Xinyuan-LilyGO/T-Deck-MAX/hardware/T-Deck Pro Max V0.1 25-09-11/T-Deck Pro Max V0.1 25-09-11.pdf

# DCDC电源

# TYPE-C

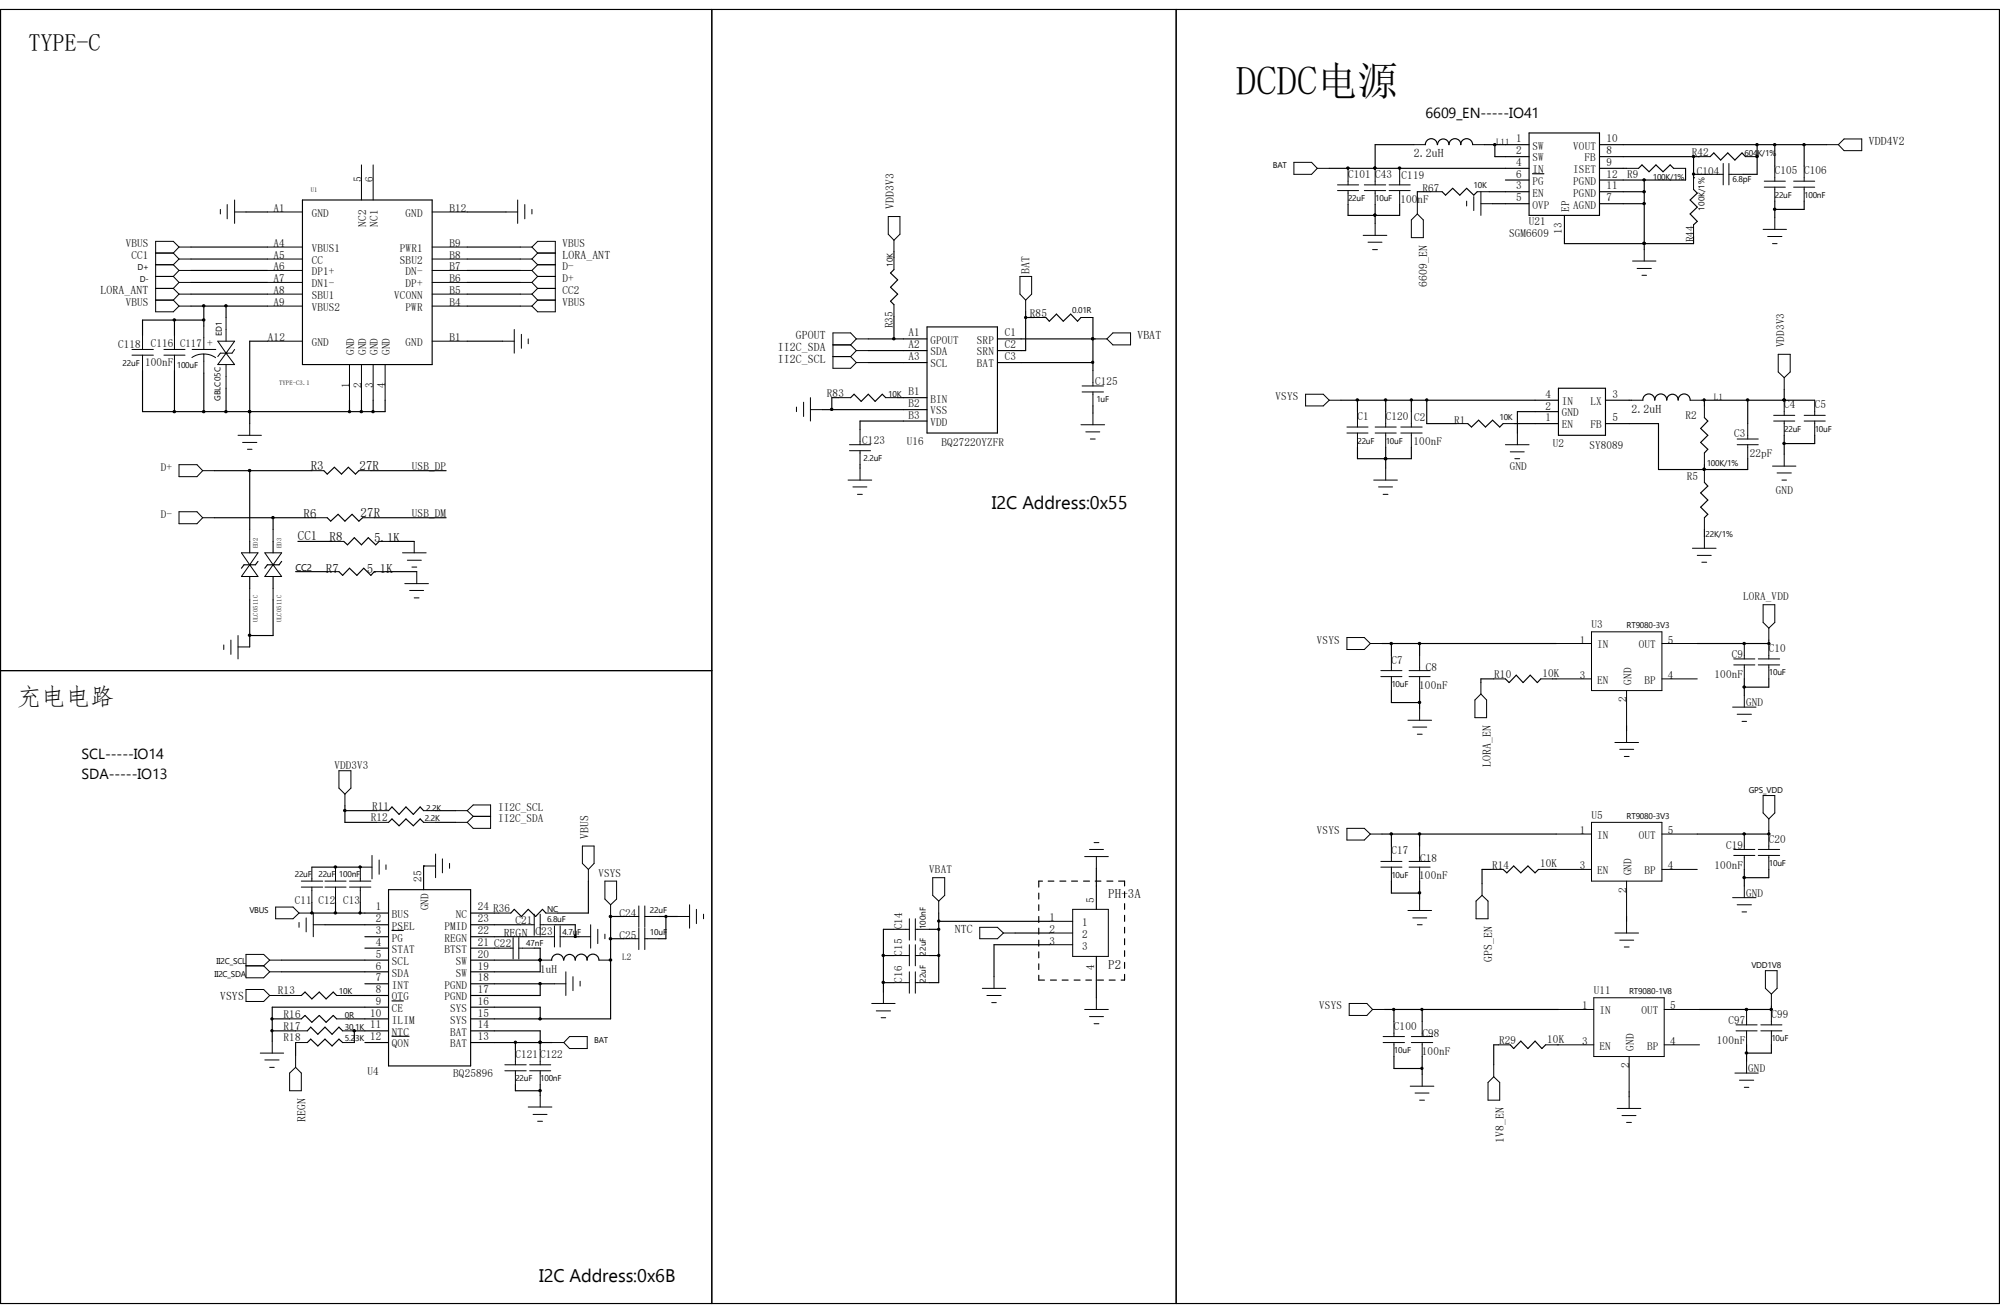
[picture p18: page 1]

STAT 5 | 20 SW
SCL 6 | 19 SW

# ESP32-S3

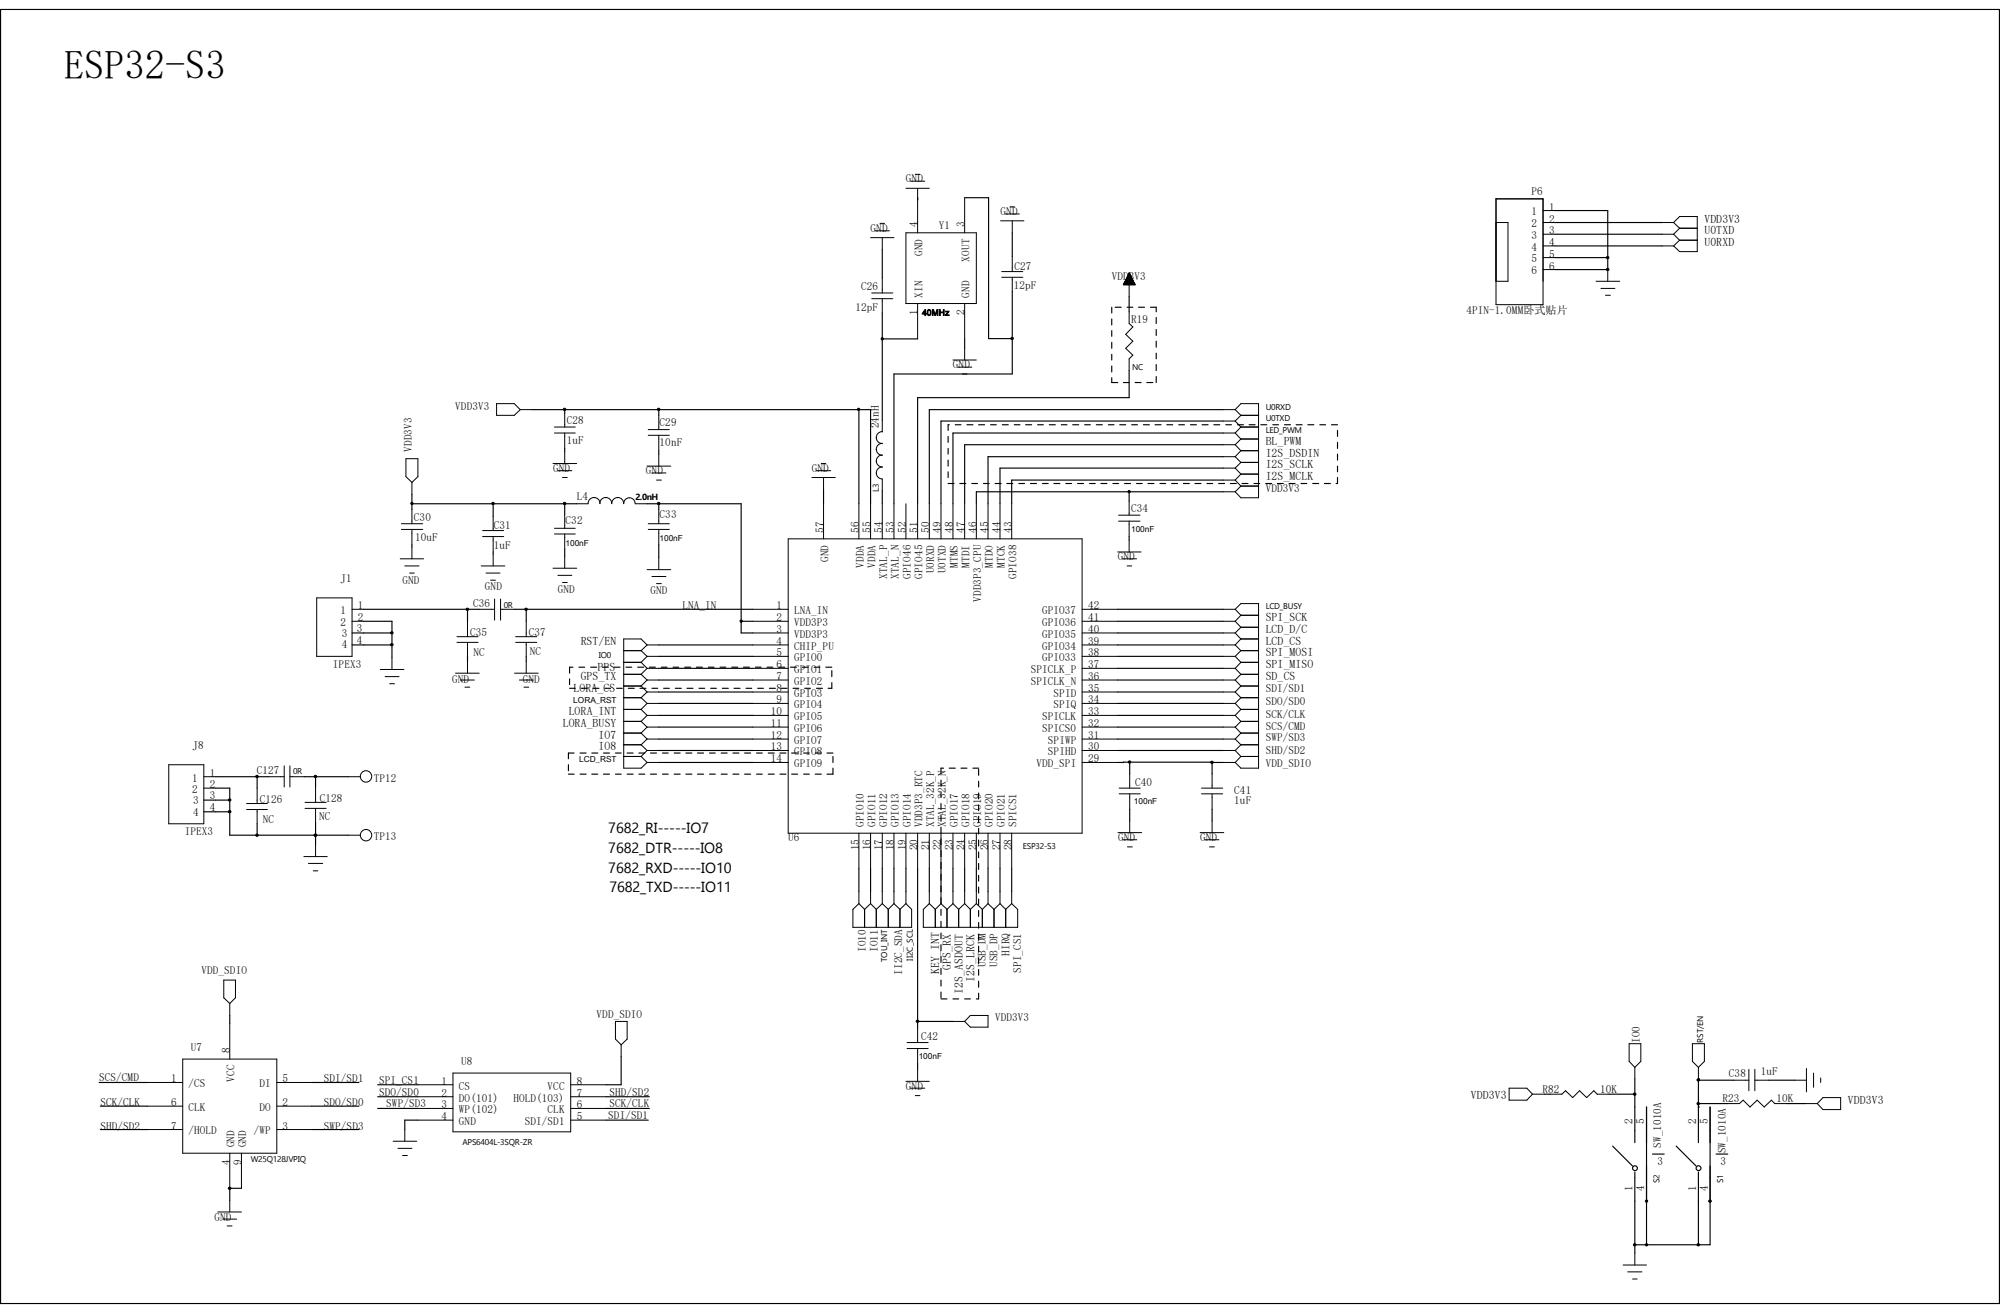
[picture p19: page 2]

# LORA_INT-----IO5 LORA_BUSY-----IO6

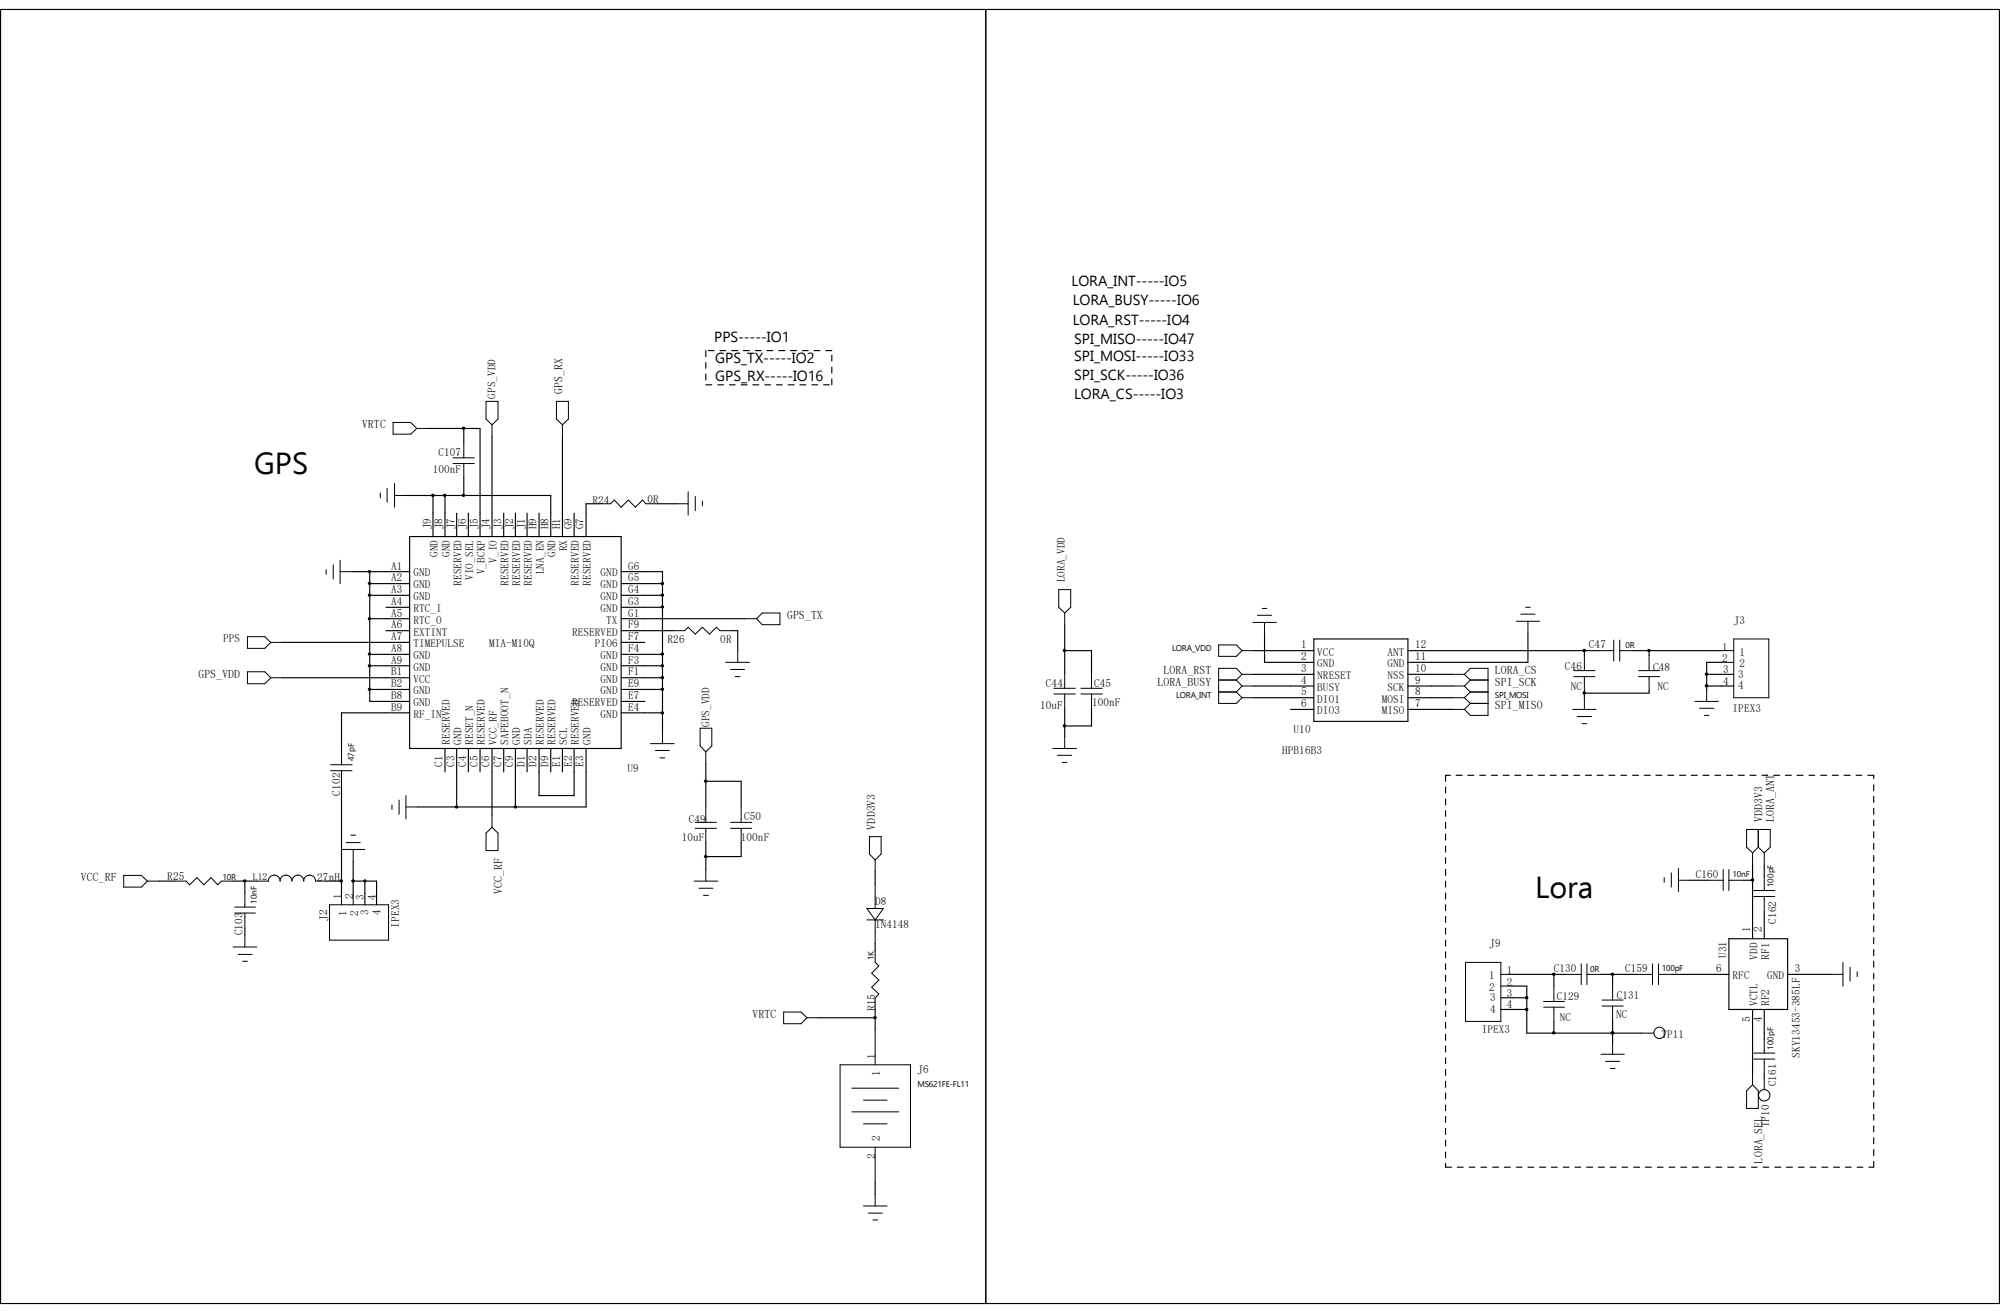
[picture p20: page 3]

G6 GND G7 RESERVED G9 RESERVED H1 RX H8 GND H9 LNA_EN J1 RESERVED J2 RESERVED J3 RESERVED J4 V_IO J5 V_BCKP J6 VIO_SEL J7 RESERVED J8 GND J9 GND

# SCL-----IO14 SDA-----IO13

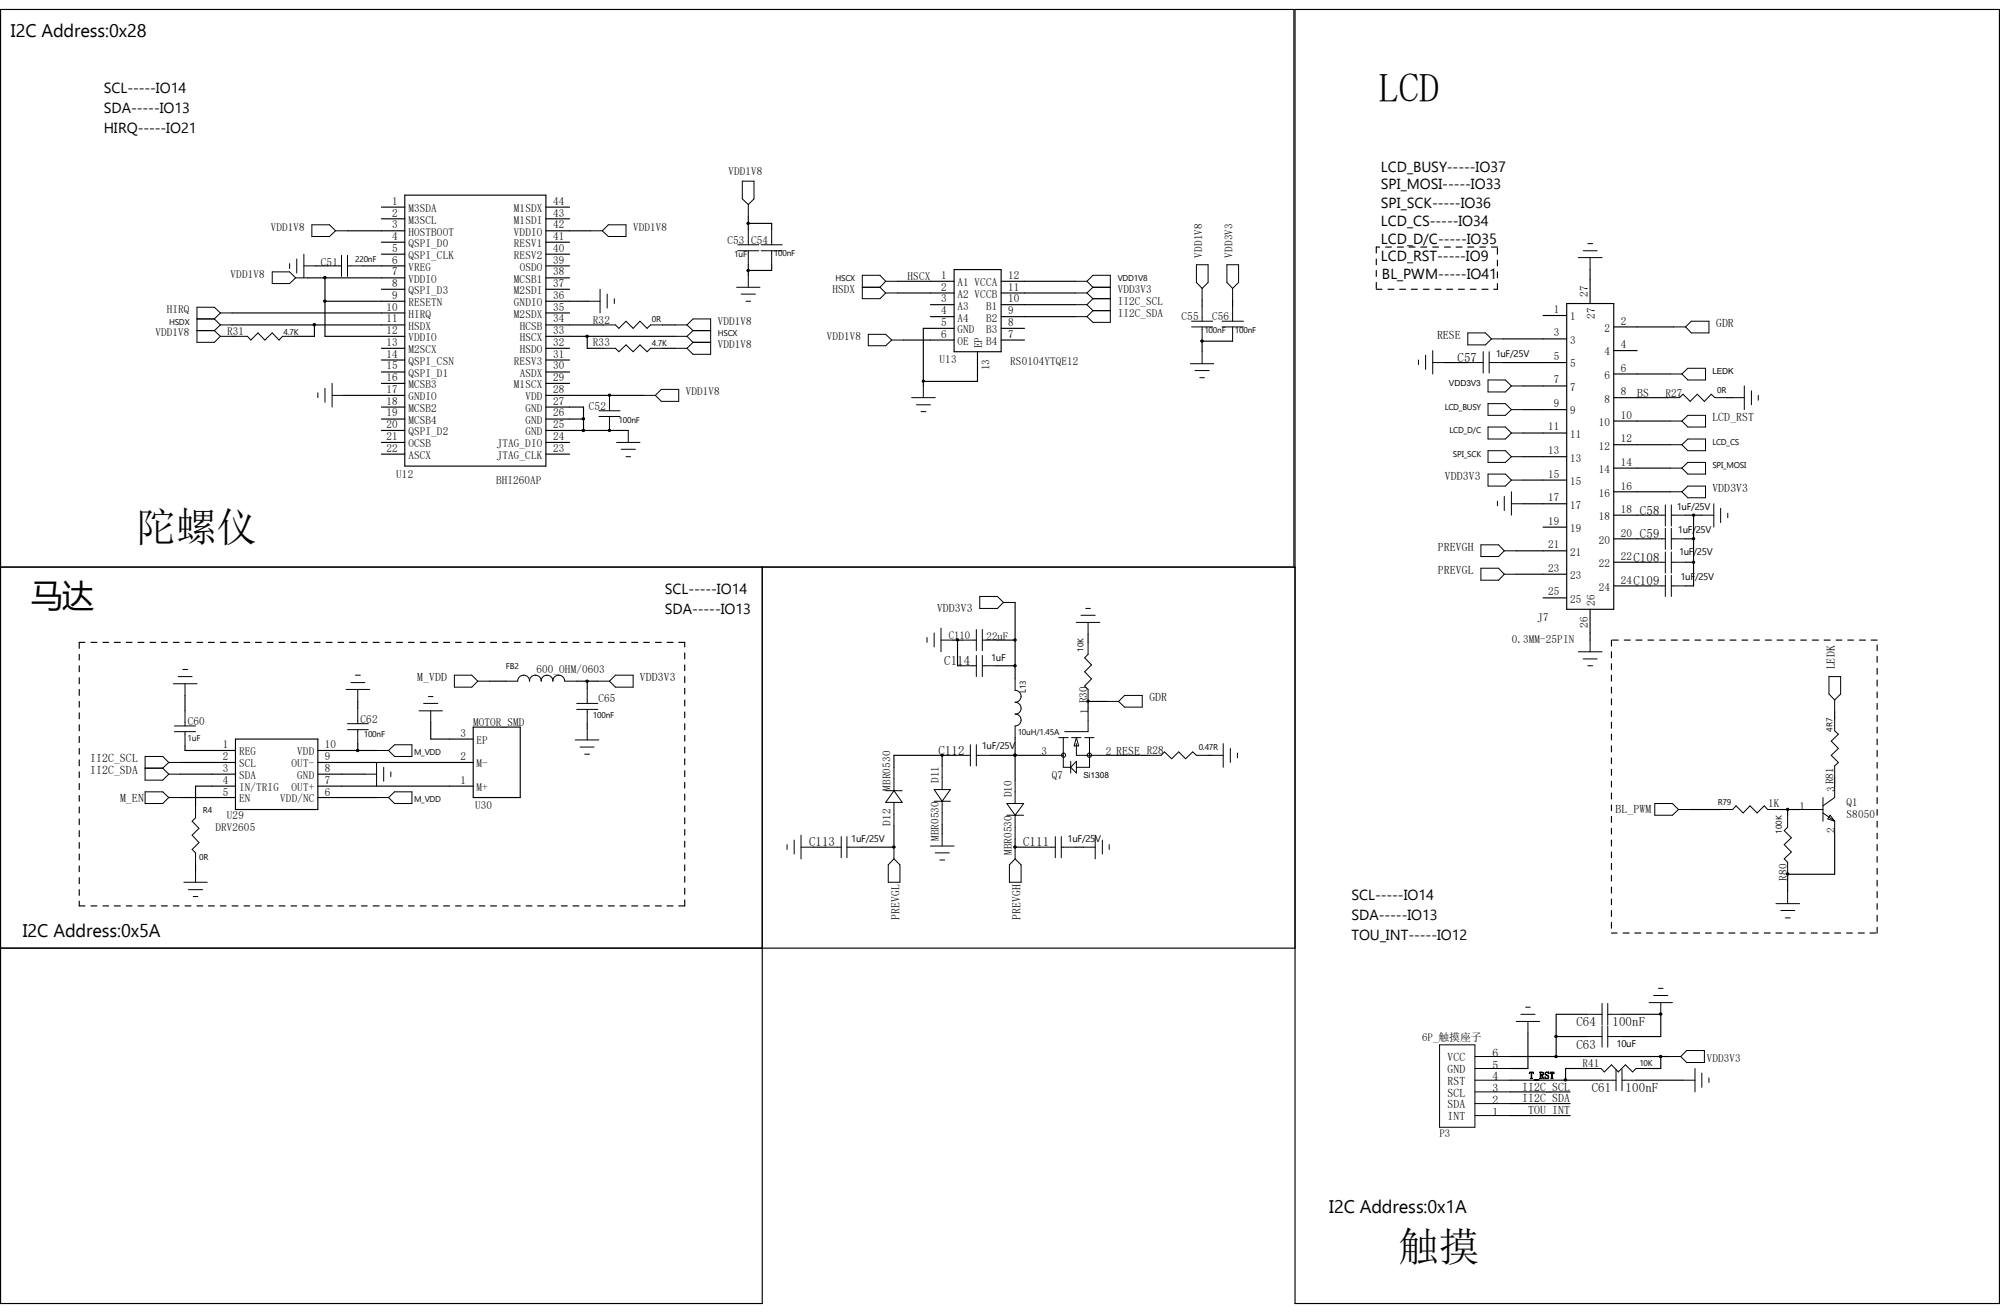
[picture p21: page 4]

7682模块

| UART1 | UART3 | DBG_UART | GSM_ANT

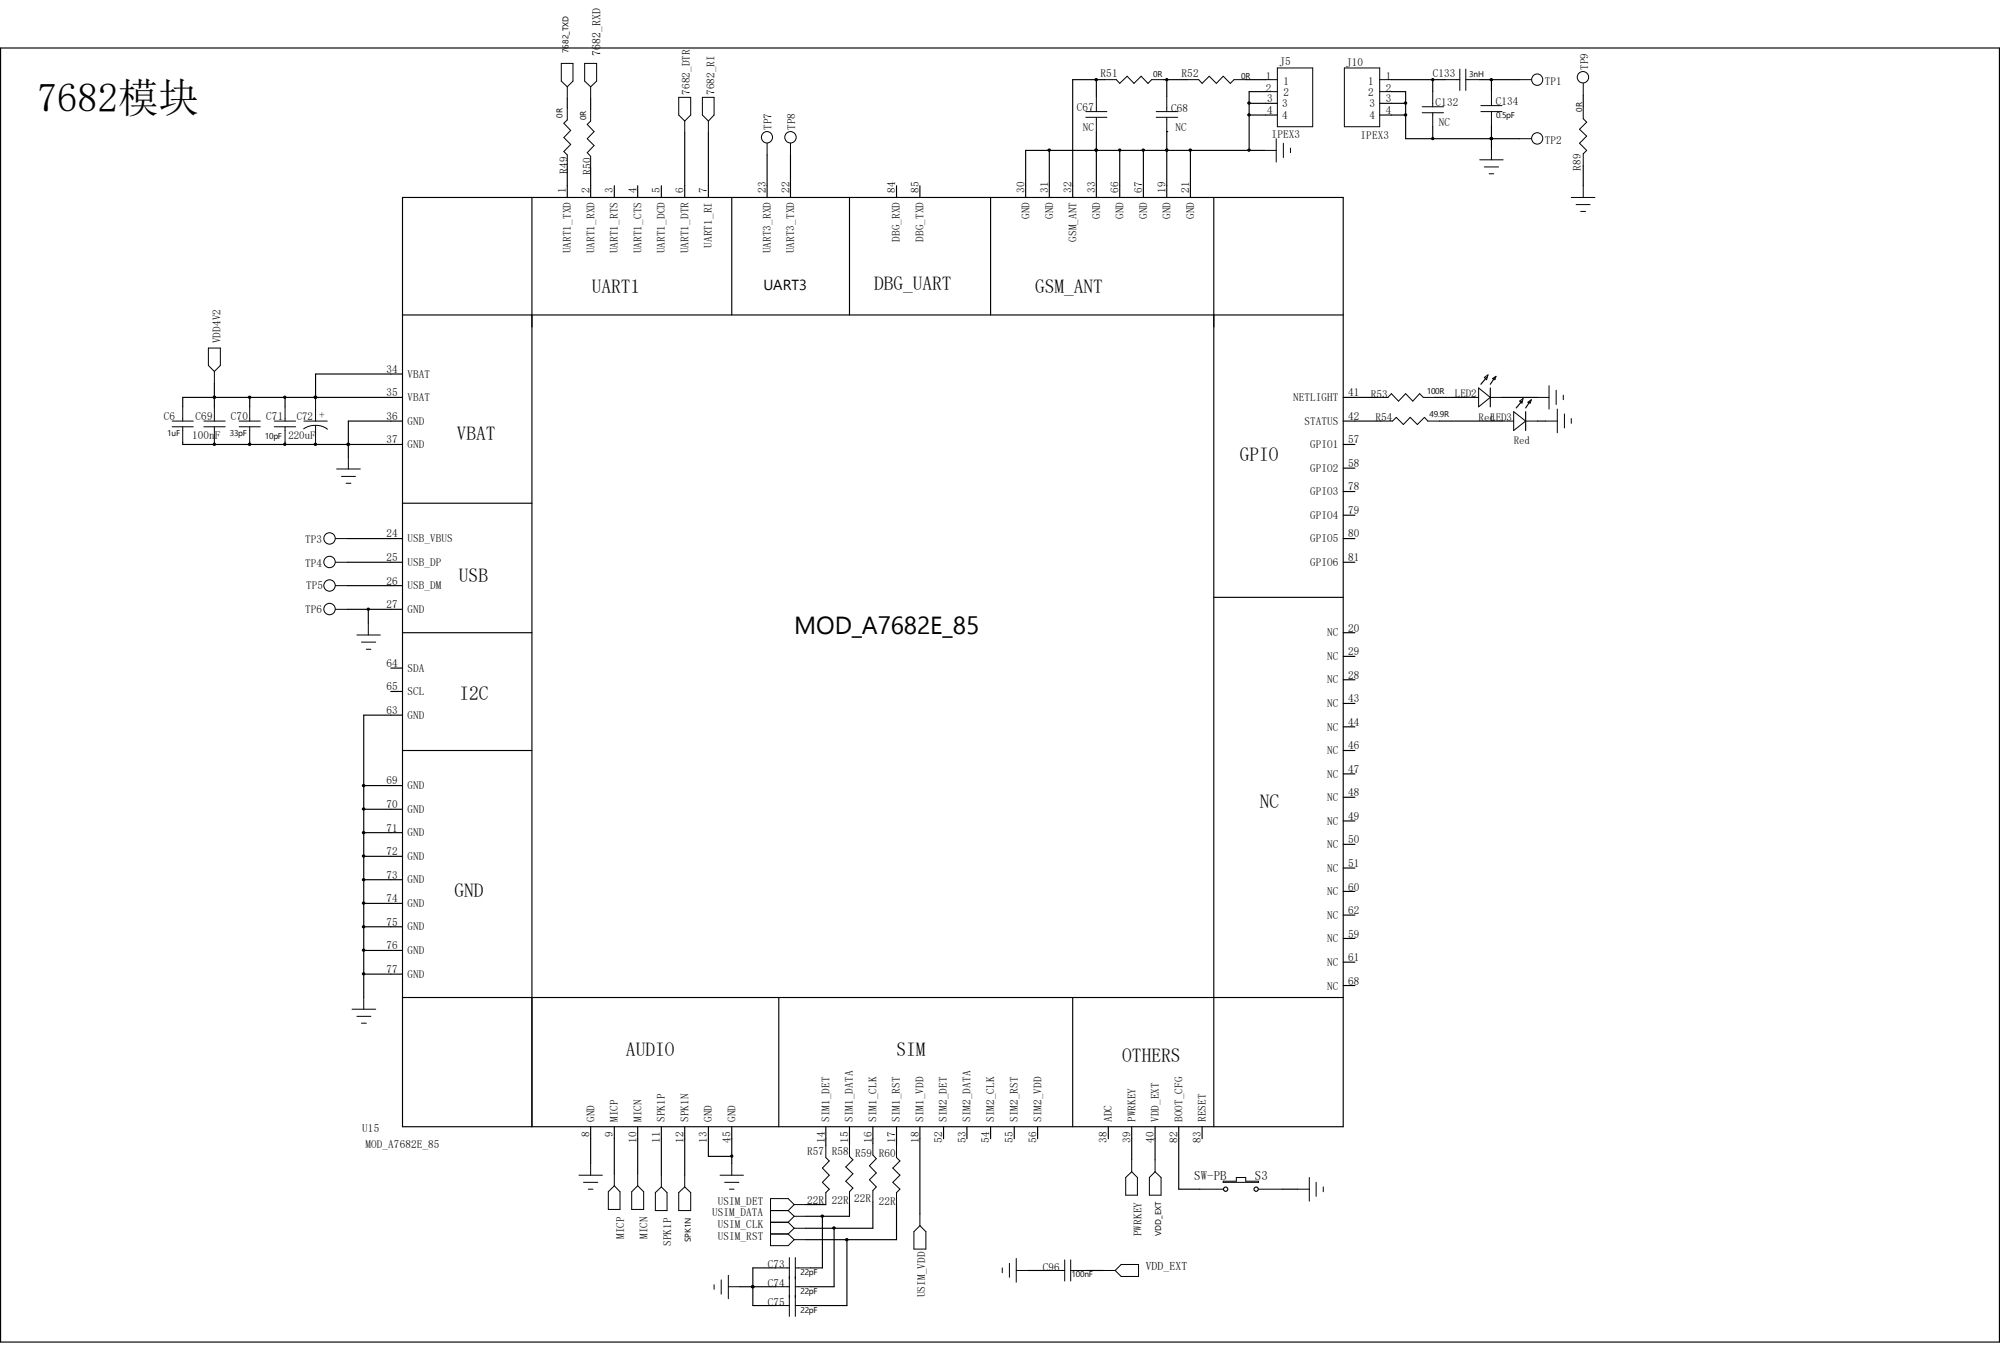
[picture p22: page 5]

9 MICP 10 MICN 11 SPK1P 12 SPK1N 13 GND 14 SIM1_DET 15 SIM1_DATA 16 SIM1_CLK 17 SIM1_RST 18 SIM1_VDD 19 GND

VBAT | | | | | GPIO | 41 NETLIGHT 42 STATUS 57 GPIO1 58 GPIO2 78 GPIO3 79 GPIO4 80 GPIO5 81 GPIO6

# SIM&SD卡座

# PWRKEY

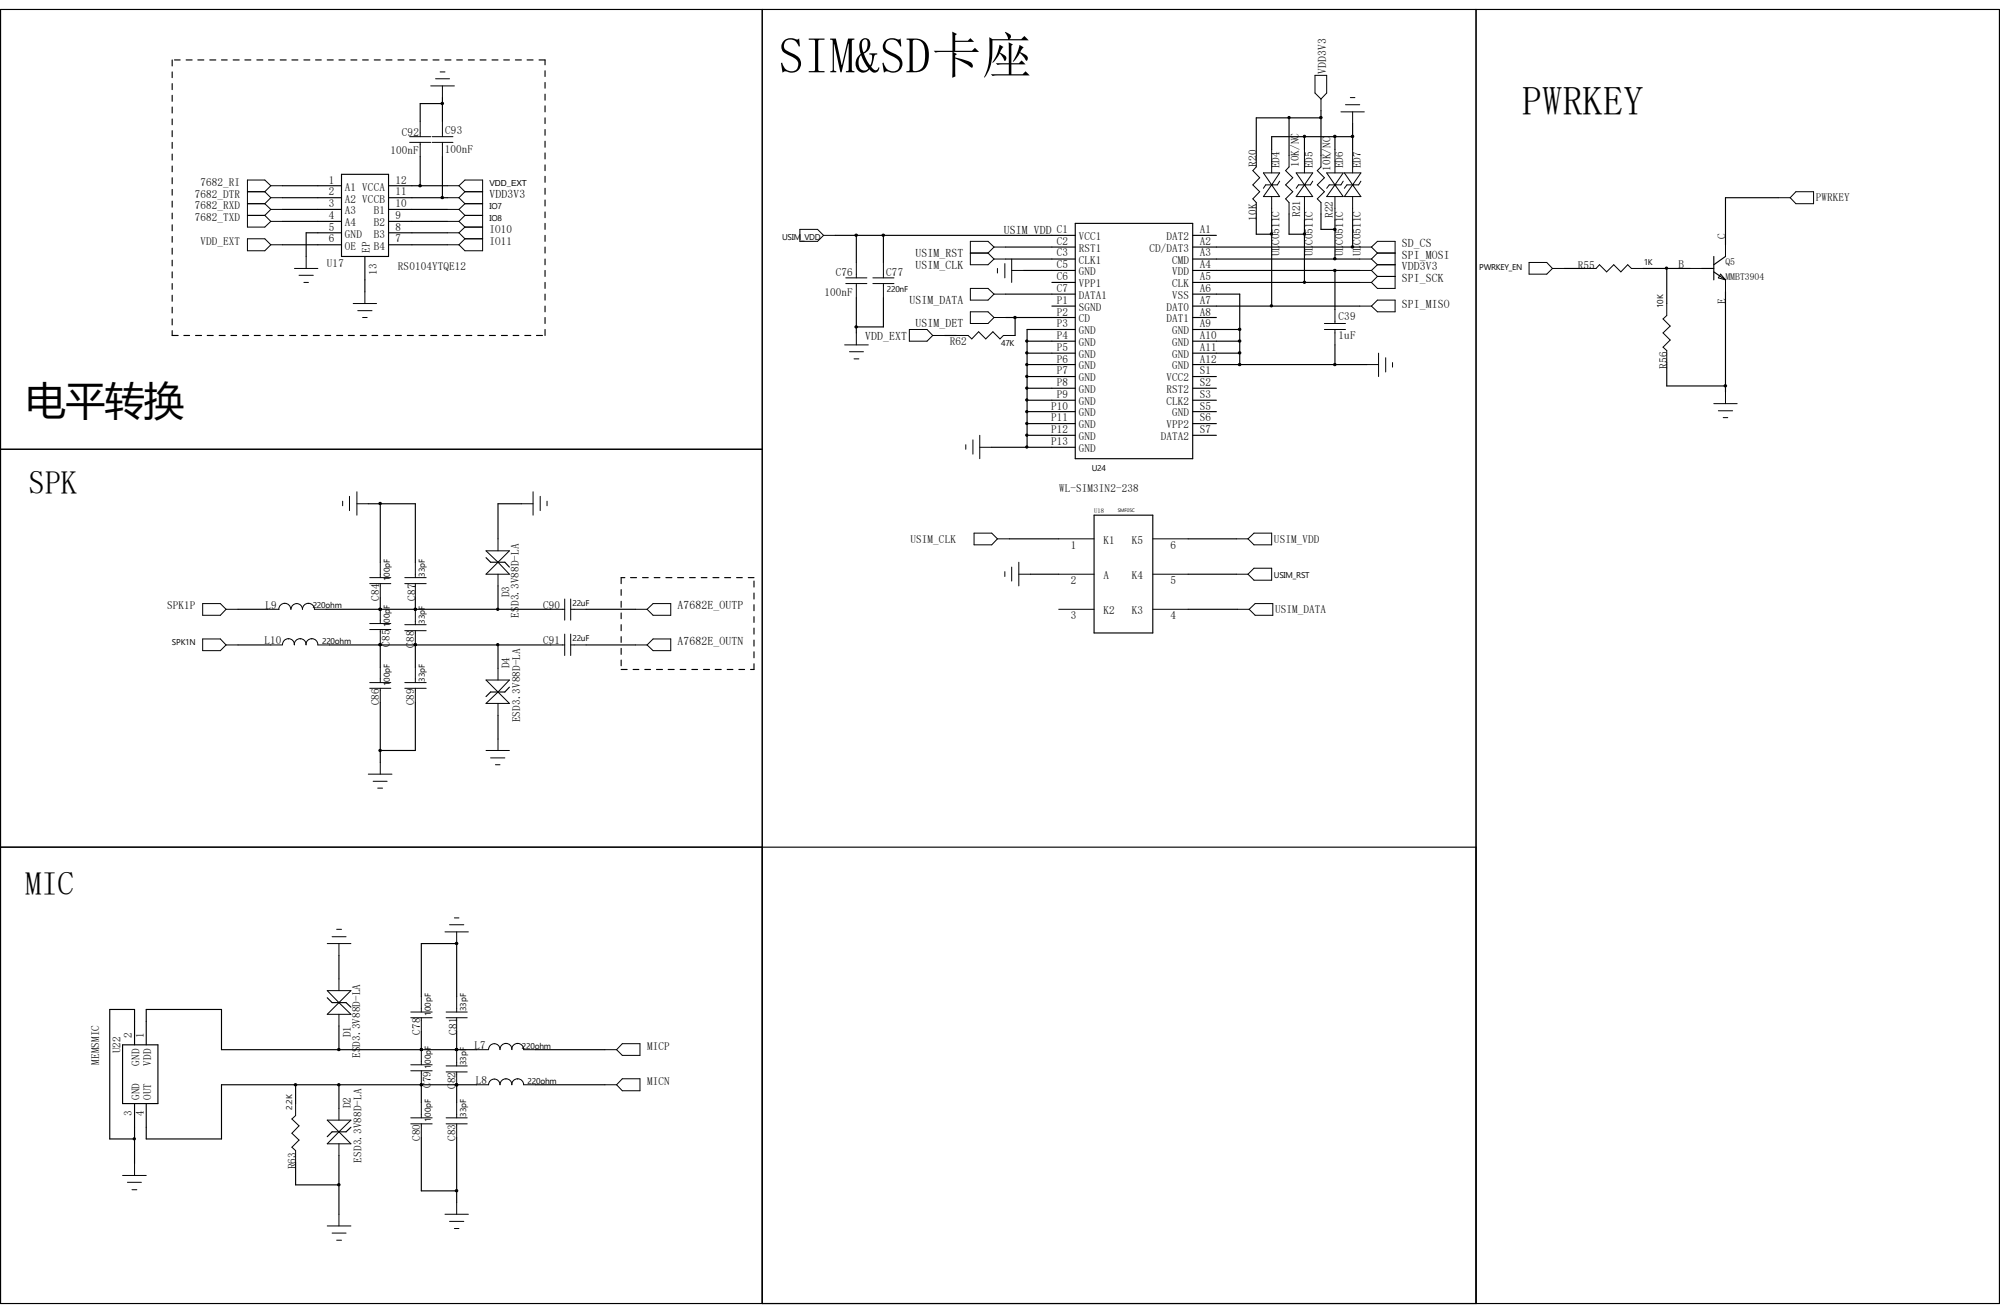
[picture p23: page 6]

# 矩阵按键

# SCL-----IO14

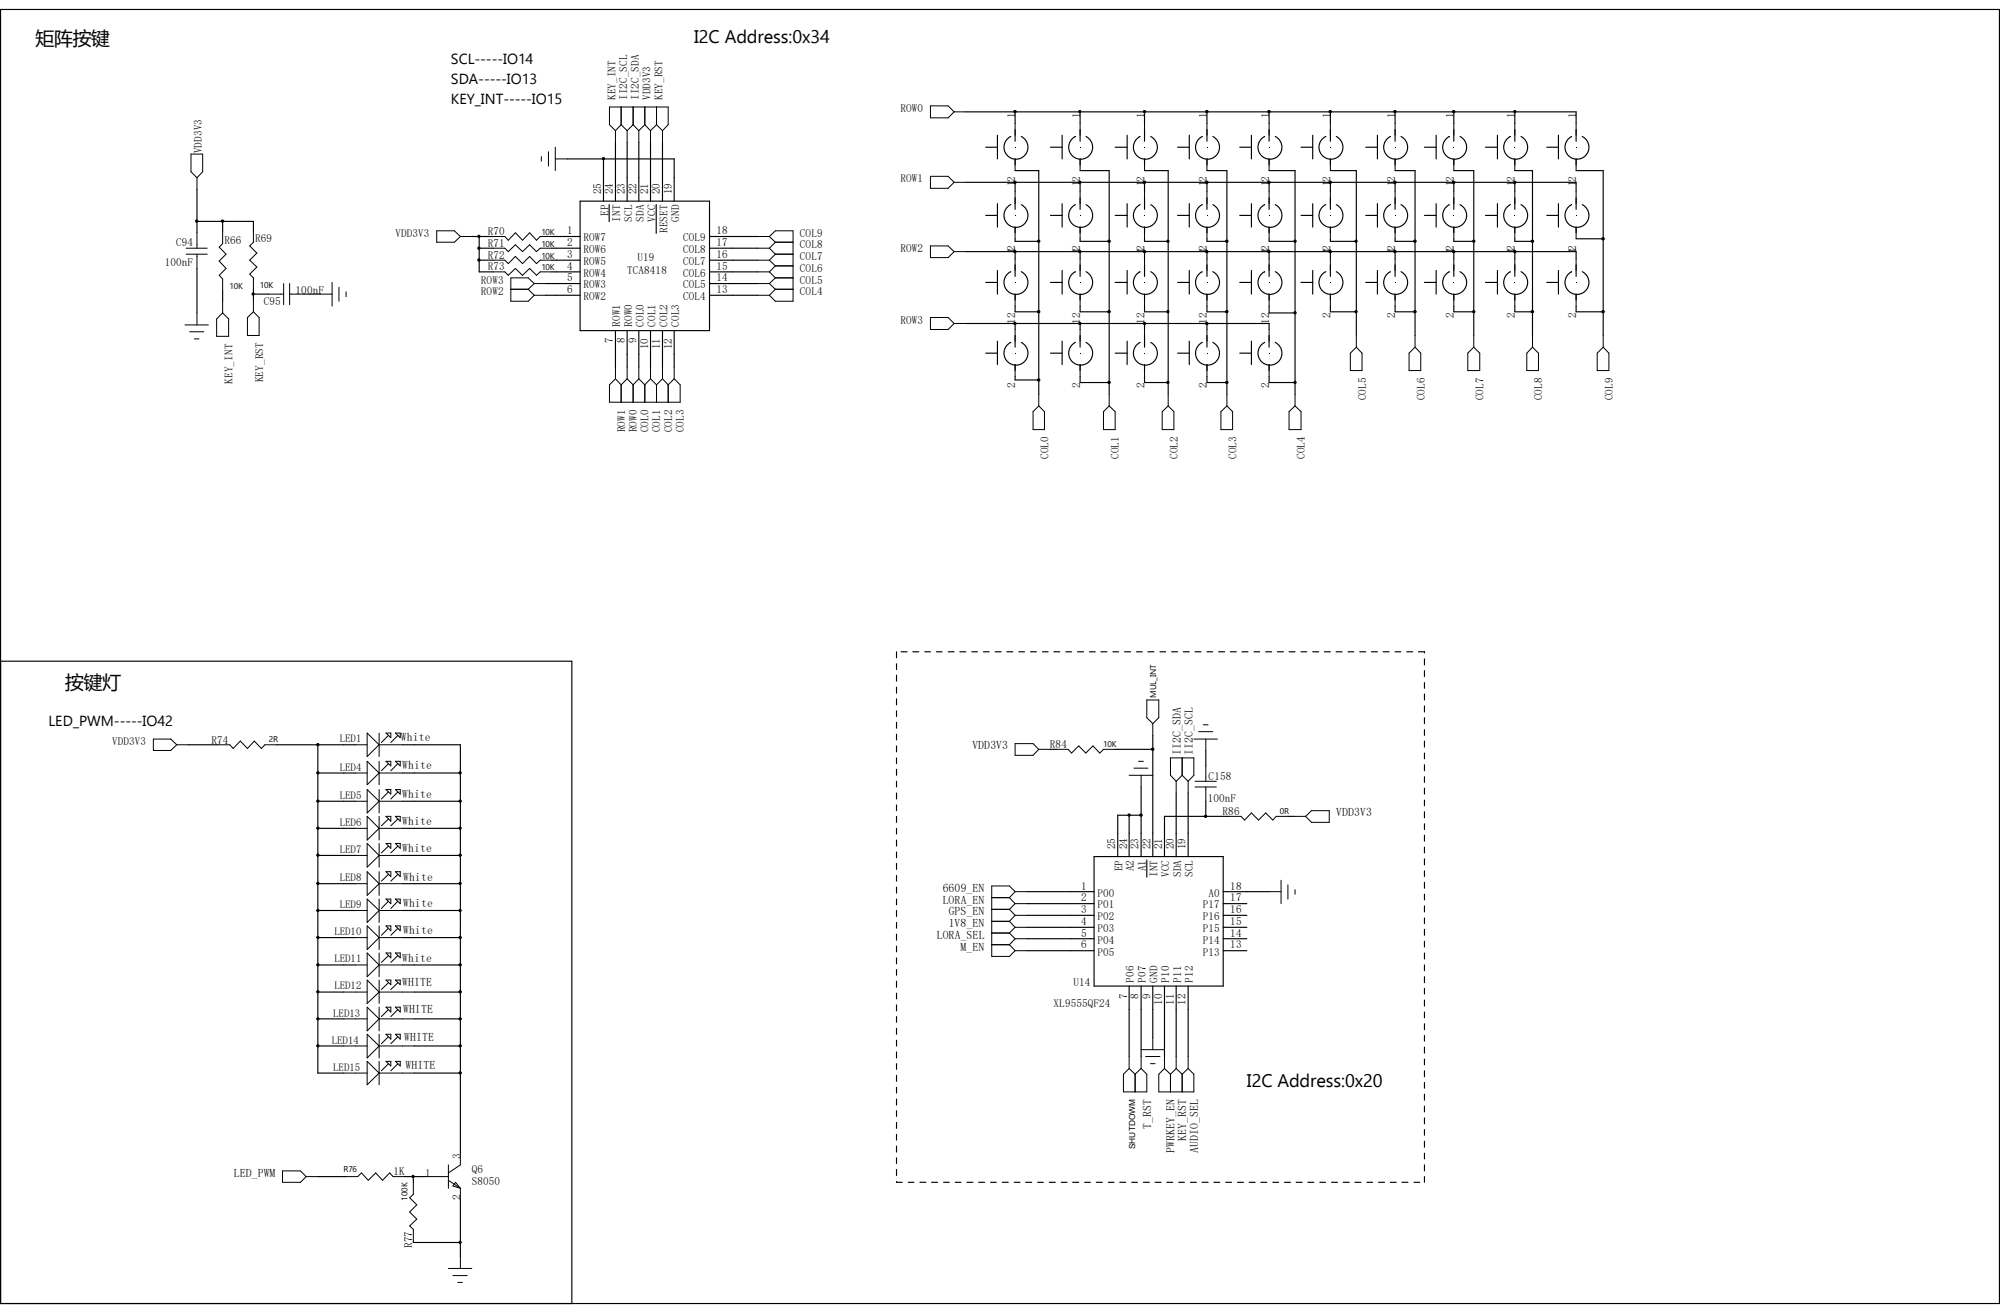
[picture p24: page 7]

18 COL9 ¹⁹ GND 20 RESET 21 VCC 22 SDA 23 SCL 24 INT 25 EP

18 A0 ¹⁹ SCL 20 SDA 21 VCC 22 INT 23 A1 24 A2 25 EP

D

6 | 5 | 4 | 3 | 2 | 1

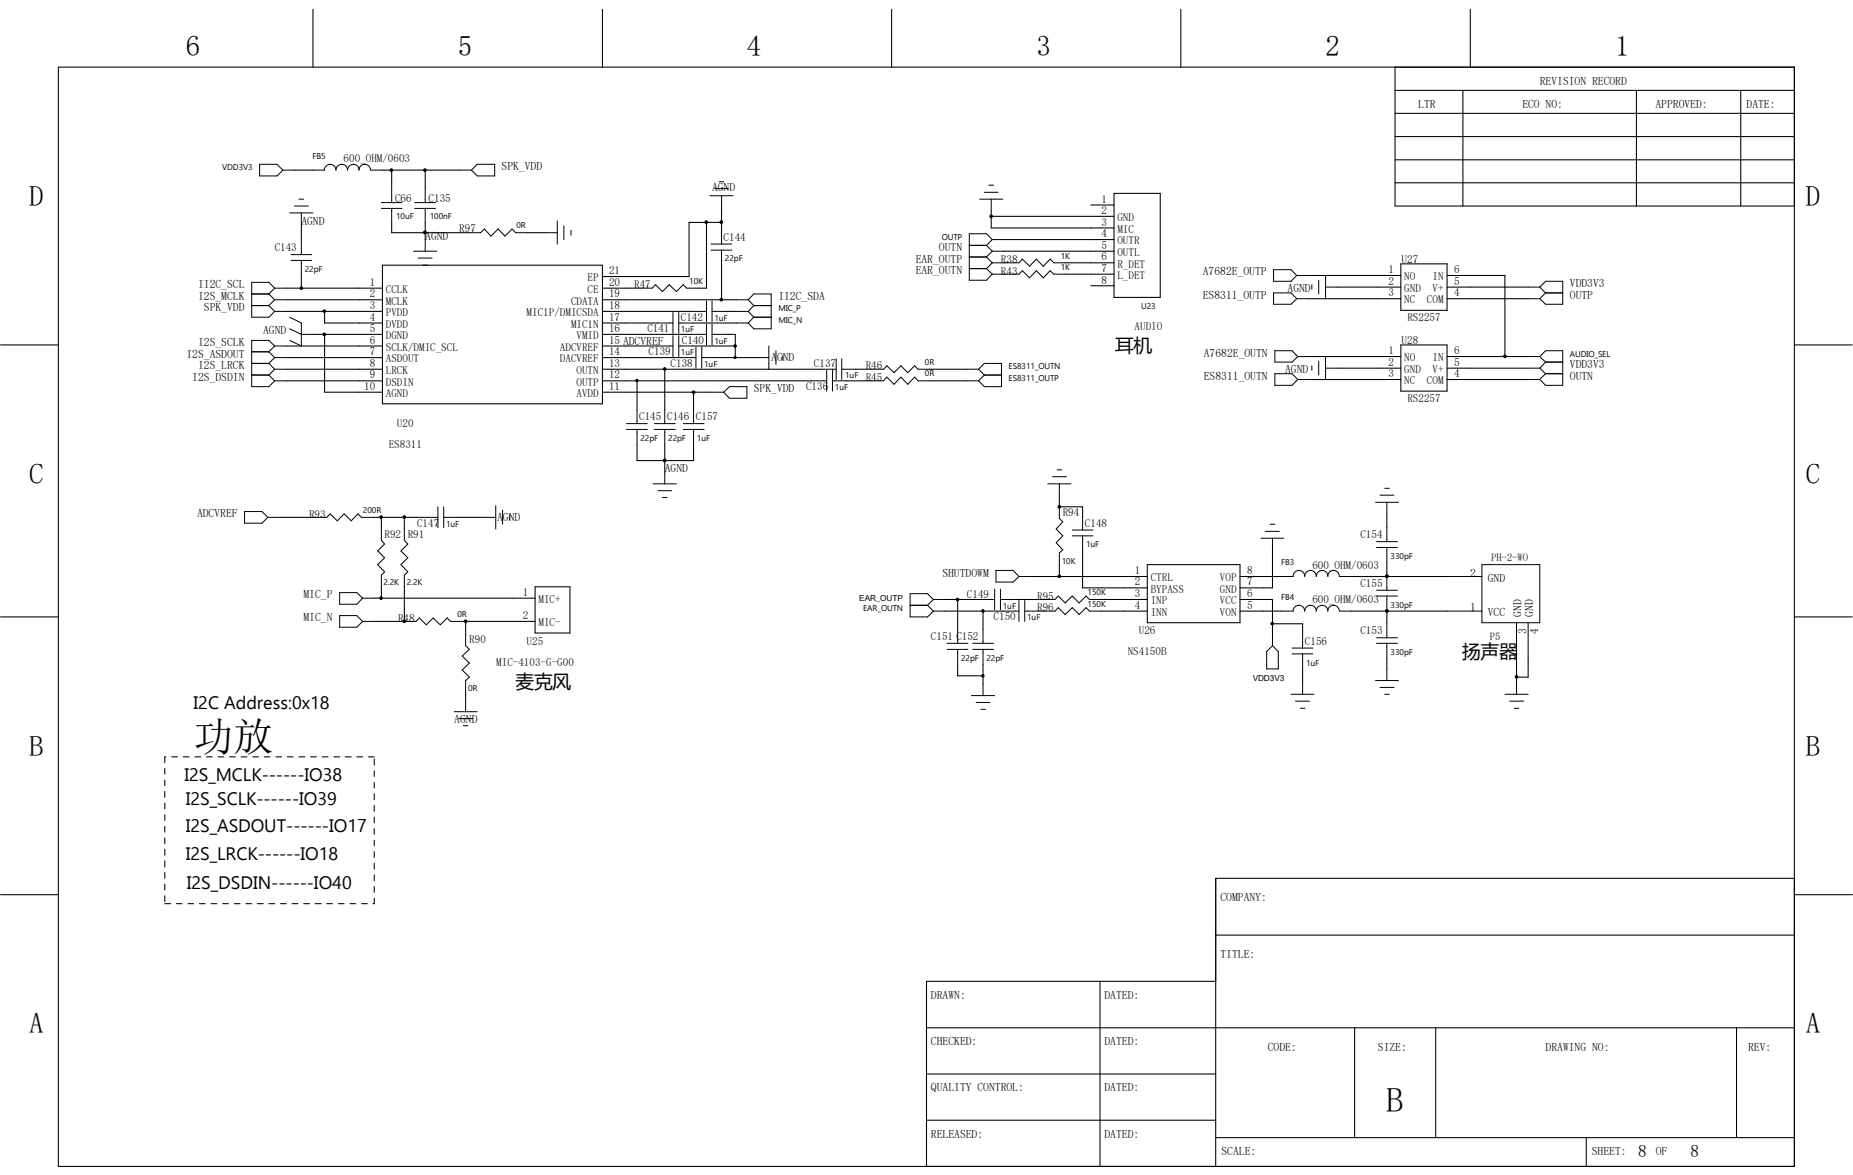
[picture p25: page 8]

REVISION RECORD

LTR | ECO NO: | APPROVED: | DATE:

17 MIC1N | C142 | 1uF

DVDD 5 | 16 VMID C141 | 1uF

DRAWN: | DATED:
CHECKED: | DATED: | CODE: | SIZE: B | DRAWING NO: | REV:

QUALITY CONTROL: | DATED:

RELEASED: | DATED:

SCALE: | 8 8 SHEET: OF
