Xinyuan-LilyGO/T-Deck-MAX/examples/motor/basic/basic.ino

// Waveform Library Effects List
// see datasheet part 11.2
// datasheet : https://github.com/Xinyuan-LilyGO/T-Deck-Pro/blob/HD-V3-250911/hardware/drv2605.pdf

#include <Wire.h>
#include <TDeckMaxBoard.h>
#include "Adafruit_DRV2605.h"
#include "ExtensionIOXL9555.hpp"

Adafruit_DRV2605 drv;
ExtensionIOXL9555 io;

void setup()
{
    Serial.begin(115200);

    Wire.begin(BOARD_I2C_SDA, BOARD_I2C_SCL);

    // XL9555 Init
    if (!io.init(Wire, BOARD_I2C_SDA, BOARD_I2C_SCL, XL9555_SLAVE_ADDRESS0)) {
        while (1) {
            Serial.println("Failed to find XL9555 - check your wiring!");
            delay(1000);
        }
    }
    io.configPort(ExtensionIOXL9555::PORT0, 0x00);   // Set PORT0 as output ,mask = 0x00 = all pin output
    io.configPort(ExtensionIOXL9555::PORT1, 0x00);   // Set PORT1 as output ,mask = 0x00 = all pin output
    io.digitalWrite(BOARD_XL9555_05_MOTOR_EN, HIGH); // Enable LoRa power

    // DRV2605 Init
    Serial.println("Adafruit DRV2605 Basic test");
    if (!drv.begin())
    {
        Serial.println("Could not find DRV2605");
        while (1)
            delay(10);
    }

    drv.selectLibrary(1);

    // I2C trigger by sending 'go' command
    // default, internal trigger when sending GO command
    drv.setMode(DRV2605_MODE_INTTRIG);
}

uint8_t effect = 1;

void loop()
{
    //  Serial.print("Effect #"); Serial.println(effect);

    if (effect == 1)
    {
        Serial.println("11.2 Waveform Library Effects List");
    }

    if (effect == 1)
    {
        Serial.println(F("1 - Strong Click - 100%"));
    }
    if (effect == 2)
    {
        Serial.println(F("2 - Strong Click - 60%"));
    }
    if (effect == 3)
    {
        Serial.println(F("3 - Strong Click - 30%"));
    }
    if (effect == 4)
    {
        Serial.println(F("4 - Sharp Click - 100%"));
    }
    if (effect == 5)
    {
        Serial.println(F("5 - Sharp Click - 60%"));
    }
    if (effect == 6)
    {
        Serial.println(F("6 - Sharp Click - 30%"));
    }
    if (effect == 7)
    {
        Serial.println(F("7 - Soft Bump - 100%"));
    }
    if (effect == 8)
    {
        Serial.println(F("8 - Soft Bump - 60%"));
    }
    if (effect == 9)
    {
        Serial.println(F("9 - Soft Bump - 30%"));
    }
    if (effect == 10)
    {
        Serial.println(F("10 - Double Click - 100%"));
    }
    if (effect == 11)
    {
        Serial.println(F("11 - Double Click - 60%"));
    }
    if (effect == 12)
    {
        Serial.println(F("12 - Triple Click - 100%"));
    }
    if (effect == 13)
    {
        Serial.println(F("13 - Soft Fuzz - 60%"));
    }
    if (effect == 14)
    {
        Serial.println(F("14 - Strong Buzz - 100%"));
    }
    if (effect == 15)
    {
        Serial.println(F("15 - 750 ms Alert 100%"));
    }
    if (effect == 16)
    {
        Serial.println(F("16 - 1000 ms Alert 100%"));
    }
    if (effect == 17)
    {
        Serial.println(F("17 - Strong Click 1 - 100%"));
    }
    if (effect == 18)
    {
        Serial.println(F("18 - Strong Click 2 - 80%"));
    }
    if (effect == 19)
    {
        Serial.println(F("19 - Strong Click 3 - 60%"));
    }
    if (effect == 20)
    {
        Serial.println(F("20 - Strong Click 4 - 30%"));
    }
    if (effect == 21)
    {
        Serial.println(F("21 - Medium Click 1 - 100%"));
    }
    if (effect == 22)
    {
        Serial.println(F("22 - Medium Click 2 - 80%"));
    }
    if (effect == 23)
    {
        Serial.println(F("23 - Medium Click 3 - 60%"));
    }
    if (effect == 24)
    {
        Serial.println(F("24 - Sharp Tick 1 - 100%"));
    }
    if (effect == 25)
    {
        Serial.println(F("25 - Sharp Tick 2 - 80%"));
    }
    if (effect == 26)
    {
        Serial.println(F("26 - Sharp Tick 3 - 60%"));
    }
    if (effect == 27)
    {
        Serial.println(F("27 - Short Double Click Strong 1 - 100%"));
    }
    if (effect == 28)
    {
        Serial.println(F("28 - Short Double Click Strong 2 - 80%"));
    }
    if (effect == 29)
    {
        Serial.println(F("29 - Short Double Click Strong 3 - 60%"));
    }
    if (effect == 30)
    {
        Serial.println(F("30 - Short Double Click Strong 4 - 30%"));
    }
    if (effect == 31)
    {
        Serial.println(F("31 - Short Double Click Medium 1 - 100%"));
    }
    if (effect == 32)
    {
        Serial.println(F("32 - Short Double Click Medium 2 - 80%"));
    }
    if (effect == 33)
    {
        Serial.println(F("33 - Short Double Click Medium 3 - 60%"));
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
    }

    // set the effect to play
    drv.setWaveform(0, effect); // play effect
    drv.setWaveform(1, 0);      // end waveform

    // play the effect!
    drv.go();

    // wait a bit
    delay(1000);

    effect++;
    if (effect > 117)
        effect = 1;
}
