Xinyuan-LilyGO/T-Deck-MAX/examples/LoRa_sx1262/lora_recv/lora_recv.ino

// notice:
// The power control pin LORA_EN of LoRa is connected to the XL9555 chip.
// So when using LoRa, you need to first enable the LORA_EN through the XL9555 chip;

/* LORA_SEL determines whether to use the internal antenna 
/  or the external antenna; Connected to XL9555 IO04
/   HIGH --- internal antenna
/   LOW --- external antenna  */

#include <RadioLib.h>
#include <TDeckMaxBoard.h>
#include "ExtensionIOXL9555.hpp"

#define RADIO_FREQ  850.0

SX1262 radio = new Module(BOARD_LORA_CS, BOARD_LORA_INT, BOARD_LORA_RST, BOARD_LORA_BUSY);
ExtensionIOXL9555 io;

// receive 
int receiveState = RADIOLIB_ERR_NONE;
volatile bool receivedFlag = false;

void set_receive_flag(void){
    receivedFlag = true;
}

void setup(){
    Serial.begin(115200);
    // while(!Serial) { delay (10); }

    // XL9555 Init
    if (!io.init(Wire, BOARD_I2C_SDA, BOARD_I2C_SCL, XL9555_SLAVE_ADDRESS0)) {
        while (1) {
            Serial.println("Failed to find XL9555 - check your wiring!");
            delay(1000);
        }
    }
    io.configPort(ExtensionIOXL9555::PORT0, 0x00); // Set PORT0 as output ,mask = 0x00 = all pin output
    io.configPort(ExtensionIOXL9555::PORT1, 0x00);  // Set PORT1 as output ,mask = 0x00 = all pin output
    io.digitalWrite(BOARD_XL9555_01_LORA_EN, HIGH); // Enable LoRa power
    io.digitalWrite(BOARD_XL9555_04_LORA_SEL, HIGH); // use internal antenna

    // LoRa Init
    SPI.begin(BOARD_SPI_SCK, BOARD_SPI_MISO, BOARD_SPI_MOSI, BOARD_LORA_CS);

    Serial.print(F("[SX1262] Initializing ... "));
    int state = radio.begin(RADIO_FREQ);
    if (state == RADIOLIB_ERR_NONE) {
        Serial.println(F("success!"));
    } else {
        Serial.print(F("failed, code "));
        Serial.println(state);
        while (true);
    }

    if (radio.setFrequency(RADIO_FREQ) == RADIOLIB_ERR_INVALID_FREQUENCY) {
        Serial.println(F("Selected frequency is invalid for this module!"));
        while (true);
    }

    // set bandwidth to 250 kHz
    if (radio.setBandwidth(125.0) == RADIOLIB_ERR_INVALID_BANDWIDTH) {
        Serial.println(F("Selected bandwidth is invalid for this module!"));
        while (true);
    }

    // set spreading factor to 10
    if (radio.setSpreadingFactor(10) == RADIOLIB_ERR_INVALID_SPREADING_FACTOR) {
        Serial.println(F("Selected spreading factor is invalid for this module!"));
        while (true);
    }

    // set coding rate to 6
    if (radio.setCodingRate(6) == RADIOLIB_ERR_INVALID_CODING_RATE) {
        Serial.println(F("Selected coding rate is invalid for this module!"));
        while (true);
    }

    // set LoRa sync word to 0xAB
    if (radio.setSyncWord(0xAB) != RADIOLIB_ERR_NONE) {
        Serial.println(F("Unable to set sync word!"));
        while (true);
    }

    // set output power to 10 dBm (accepted range is -17 - 22 dBm)
    if (radio.setOutputPower(22) == RADIOLIB_ERR_INVALID_OUTPUT_POWER) {
        Serial.println(F("Selected output power is invalid for this module!"));
        while (true);
    }

    // set over current protection limit to 80 mA (accepted range is 45 - 240 mA)
    // NOTE: set value to 0 to disable overcurrent protection
    if (radio.setCurrentLimit(140) == RADIOLIB_ERR_INVALID_CURRENT_LIMIT) {
        Serial.println(F("Selected current limit is invalid for this module!"));
        while (true);
    }

    // set LoRa preamble length to 15 symbols (accepted range is 0 - 65535)
    if (radio.setPreambleLength(15) == RADIOLIB_ERR_INVALID_PREAMBLE_LENGTH) {
        Serial.println(F("Selected preamble length is invalid for this module!"));
        while (true);
    }

    // disable CRC
    if (radio.setCRC(false) == RADIOLIB_ERR_INVALID_CRC_CONFIGURATION) {
        Serial.println(F("Selected CRC is invalid for this module!"));
        while (true);
    }

    // Some SX126x modules have TCXO (temperature compensated crystal
    // oscillator). To configure TCXO reference voltage,
    // the following method can be used.
    if (radio.setTCXO(2.4) == RADIOLIB_ERR_INVALID_TCXO_VOLTAGE) {
        Serial.println(F("Selected TCXO voltage is invalid for this module!"));
        while (true);
    }

    // Some SX126x modules use DIO2 as RF switch. To enable
    // this feature, the following method can be used.
    // NOTE: As long as DIO2 is configured to control RF switch,
    //       it can't be used as interrupt pin!
    if (radio.setDio2AsRfSwitch() != RADIOLIB_ERR_NONE) {
        Serial.println(F("Failed to set DIO2 as RF switch!"));
        while (true);
    }

    Serial.println(F("All settings succesfully changed!"));

    radio.setPacketReceivedAction(set_receive_flag);
    Serial.print(F("[SX1262] Starting to listen ... "));
    state = radio.startReceive();
    if (state == RADIOLIB_ERR_NONE) {
        Serial.println(F("success!"));
    } else {
        Serial.print(F("failed, code "));
        Serial.println(state);
    }
}

void loop()
{
  // check if the flag is set
  if(receivedFlag) {
    // reset flag
    receivedFlag = false;

    // you can read received data as an Arduino String
    String str;
    int state = radio.readData(str);

    // you can also read received data as byte array
    /*
      byte byteArr[8];
      int numBytes = radio.getPacketLength();
      int state = radio.readData(byteArr, numBytes);
    */

    if (state == RADIOLIB_ERR_NONE) {
      // packet was successfully received
      Serial.println(F("[SX1262] Received packet!"));

      // print data of the packet
      Serial.print(F("[SX1262] Data:\t\t"));
      Serial.println(str);

      // print RSSI (Received Signal Strength Indicator)
      Serial.print(F("[SX1262] RSSI:\t\t"));
      Serial.print(radio.getRSSI());
      Serial.println(F(" dBm"));

      // print SNR (Signal-to-Noise Ratio)
      Serial.print(F("[SX1262] SNR:\t\t"));
      Serial.print(radio.getSNR());
      Serial.println(F(" dB"));

      // print frequency error
      Serial.print(F("[SX1262] Frequency error:\t"));
      Serial.print(radio.getFrequencyError());
      Serial.println(F(" Hz"));

    } else if (state == RADIOLIB_ERR_CRC_MISMATCH) {
      // packet was received, but is malformed
      Serial.println(F("CRC error!"));

    } else {
      // some other error occurred
      Serial.print(F("failed, code "));
      Serial.println(state);

    }
  }
}
