Xinyuan-LilyGO/T-Deck-MAX/examples/test_BHI260AP/test_BHI260AP.ino

/**
 *
 * @license MIT License
 *
 * Copyright (c) 2023 lewis he
 *
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
 * @file      BHI260AP_6DoF.ino
 * @author    Lewis He (lewishe@outlook.com)
 * @date      2023-09-06
 *
 */
#include <Wire.h>
#include <SPI.h>
#include <Arduino.h>
#include <TDeckMaxBoard.h>
#include "SensorBHI260AP.hpp"
#include "ExtensionIOXL9555.hpp"

// The power control pin 1V8_EN of Gyroscope is connected to the XL9555 chip.
// So when using Gyroscope, you need to first enable the 1V8_EN through the XL9555 chip;

// Gyroscope
#define BHI260AP_SDA BOARD_GYROSCOPDE_SDA
#define BHI260AP_SCL BOARD_GYROSCOPDE_SCL
#define BHI260AP_IRQ BOARD_GYROSCOPDE_INT
#define BHI260AP_RST BOARD_GYROSCOPDE_RST

SensorBHI260AP bhy;
ExtensionIOXL9555 io;

void accel_process_callback(uint8_t sensor_id, uint8_t *data_ptr, uint32_t len, uint64_t *timestamp)
{
    struct bhy2_data_xyz data;
    float scaling_factor = get_sensor_default_scaling(sensor_id);
    bhy2_parse_xyz(data_ptr, &data);
    Serial.print(bhy.getSensorName(sensor_id));
    Serial.print(":");
    Serial.printf("x: %f, y: %f, z: %f;\r\n",
                  data.x * scaling_factor,
                  data.y * scaling_factor,
                  data.z * scaling_factor
                 );
}

void gyro_process_callback(uint8_t sensor_id, uint8_t *data_ptr, uint32_t len, uint64_t *timestamp)
{
    struct bhy2_data_xyz data;
    float scaling_factor = get_sensor_default_scaling(sensor_id);
    bhy2_parse_xyz(data_ptr, &data);
    Serial.print(bhy.getSensorName(sensor_id));
    Serial.print(":");
    Serial.printf("x: %f, y: %f, z: %f;\r\n",
                  data.x * scaling_factor,
                  data.y * scaling_factor,
                  data.z * scaling_factor
                 );
}

void setup()
{
    Serial.begin(115200);
    while (!Serial);

    // IO : enable gyroscope module
    // XL9555 Init
    if (!io.init(Wire, BOARD_I2C_SDA, BOARD_I2C_SCL, XL9555_SLAVE_ADDRESS0)) {
        while (1) {
            Serial.println("Failed to find XL9555 - check your wiring!");
            delay(1000);
        }
    }
    io.configPort(ExtensionIOXL9555::PORT0, 0x00); // Set PORT0 as output ,mask = 0x00 = all pin output
    io.configPort(ExtensionIOXL9555::PORT1, 0x00);  // Set PORT1 as output ,mask = 0x00 = all pin output
    io.digitalWrite(BOARD_XL9555_03_1V8_EN, HIGH); // Enable gyroscope power

    // Gyroscope Init
    // Set the reset pin and interrupt pin, if any
    bhy.setPins(BHI260AP_RST, BHI260AP_IRQ);

    // Using I2C interface
    // BHI260AP_SLAVE_ADDRESS_L = 0x28
    // BHI260AP_SLAVE_ADDRESS_H = 0x29
    if (!bhy.init(Wire, BHI260AP_SDA, BHI260AP_SCL, BHI260AP_SLAVE_ADDRESS_L)) {
        Serial.print("Failed to init BHI260AP - ");
        Serial.println(bhy.getError());
        while (1) {
            delay(1000);
        }
    }

    Serial.println("Init BHI260AP Sensor success!");

    // Output all available sensors to Serial
    bhy.printSensors(Serial);

    float sample_rate = 100.0;      /* Read out hintr_ctrl measured at 100Hz */
    uint32_t report_latency_ms = 0; /* Report immediately */

    // Enable acceleration
    bhy.configure(SENSOR_ID_ACC_PASS, sample_rate, report_latency_ms);
    // Enable gyroscope
    bhy.configure(SENSOR_ID_GYRO_PASS, sample_rate, report_latency_ms);

    // Set the acceleration sensor result callback function
    bhy.onResultEvent(SENSOR_ID_ACC_PASS, accel_process_callback);

    // Set the gyroscope sensor result callback function
    bhy.onResultEvent(SENSOR_ID_GYRO_PASS, gyro_process_callback);
}

void loop()
{
    // Update sensor fifo
    bhy.update();
    delay(200);
}
