Xinyuan-LilyGO/T-Deck-MAX/examples/A7682E/test_AT/test_AT.ino

#include "Arduino.h"
#include <TDeckMaxBoard.h>
#include "ExtensionIOXL9555.hpp"

ExtensionIOXL9555 io;
bool reply = false;

void setup(void)
{
    
    SerialMon.begin(115200);
    SerialAT.begin(115200, SERIAL_8N1, BOARD_A7682E_TXD, BOARD_A7682E_RXD);

    // XL9555 Init
    if (!io.init(Wire, BOARD_I2C_SDA, BOARD_I2C_SCL, XL9555_SLAVE_ADDRESS0)) {
        while (1) {
            Serial.println("Failed to find XL9555 - check your wiring!");
            delay(1000);
        }
    }
    io.configPort(ExtensionIOXL9555::PORT0, 0x00);      // Set PORT0 as output ,mask = 0x00 = all pin output
    io.configPort(ExtensionIOXL9555::PORT1, 0x00);      // Set PORT1 as output ,mask = 0x00 = all pin output
    io.digitalWrite(BOARD_XL9555_00_6609_EN, HIGH);     // enable A7682 module power
    io.digitalWrite(BOARD_XL9555_10_PWRKEY_EN, HIGH);   // power on
    io.digitalWrite(BOARD_XL9555_06_AMPLIFIER, HIGH);    // Enable power amplifier
    io.digitalWrite(BOARD_XL9555_12_AUDIO_SEL, HIGH);   // Audio output selection: A7682E module
    
    // A7682  Power on
    Serial.println("Power on the modem PWRKEY.");
    // A7682E_power_on();

    int i = 10;
    Serial.println("\nTesting Modem Response...\n");
    Serial.println("****");
    while (i)
    {
        SerialAT.println("AT");
        delay(500);
        if (SerialAT.available())
        {
            String r = SerialAT.readString();
            SerialAT.println(r);
            if (r.indexOf("OK") >= 0)
            {
                reply = true;
                break;
            }
        }
        delay(500);
        i--;
    }
    Serial.println("****\n");

    if (reply)
    {
        Serial.println(F("***********************************************************"));
        Serial.println(F(" You can now send AT commands"));
        Serial.println(F(" Enter \"AT\" (without quotes), and you should see \"OK\""));
        Serial.println(F(" If it doesn't work, select \"Both NL & CR\" in Serial Monitor"));
        Serial.println(F(" DISCLAIMER: Entering AT commands without knowing what they do"));
        Serial.println(F(" can have undesired consiquinces..."));
        Serial.println(F("***********************************************************\n"));
    }
    else
    {
        Serial.println(F("***********************************************************"));
        Serial.println(F(" Failed to connect to the modem! Check the baud and try again."));
        Serial.println(F("***********************************************************\n"));
    }
}

void loop(void)
{
    while (SerialAT.available())
    {
        SerialMon.write(SerialAT.read());
    }
    while (SerialMon.available())
    {
        SerialAT.write(SerialMon.read());
    }
}
