Xinyuan-LilyGO/T-Deck-MAX/examples/factory/ui_deckpro.cpp

#include "ui_deckpro.h"
#include "src/assets.h"
#include "stdio.h"
#include "ui_deckpro_port.h"
#include "Arduino.h"
#include "WiFi.h"
#include <ctype.h>

#define SETTING_PAGE_MAX_ITEM 7
#define GET_BUFF_LEN(a) sizeof(a)/sizeof(a[0])

#define FONT_BOLD_SIZE_14 &Font_Mono_Bold_14
#define FONT_BOLD_SIZE_15 &Font_Mono_Bold_15
#define FONT_BOLD_SIZE_16 &Font_Mono_Bold_16
#define FONT_BOLD_SIZE_17 &Font_Mono_Bold_17
#define FONT_BOLD_SIZE_18 &Font_Mono_Bold_18
#define FONT_BOLD_SIZE_19 &Font_Mono_Bold_19

#define FONT_BOLD_MONO_SIZE_14 &Font_Mono_Bold_14
#define FONT_BOLD_MONO_SIZE_15 &Font_Mono_Bold_15
#define FONT_BOLD_MONO_SIZE_16 &Font_Mono_Bold_16
#define FONT_BOLD_MONO_SIZE_17 &Font_Mono_Bold_17
#define FONT_BOLD_MONO_SIZE_18 &Font_Mono_Bold_18
#define FONT_BOLD_MONO_SIZE_19 &Font_Mono_Bold_19

#if LV_FONT_SIMSUN_16_CJK
#define FONT_LOW_BATTERY_POPUP &lv_font_simsun_16_cjk
#else
#define FONT_LOW_BATTERY_POPUP FONT_BOLD_MONO_SIZE_15
#endif

#define LOW_BATTERY_CHECK_PERIOD_MS        1000
#define LOW_BATTERY_SHUTDOWN_DELAY_MS     (20UL * 1000UL)
#define LOW_BATTERY_SHUTDOWN_PERCENT      5
#define LOW_BATTERY_NOMINAL_VOLTAGE_MV    3700
#define LOW_BATTERY_SHUTDOWN_VOLTAGE_MV   (LOW_BATTERY_NOMINAL_VOLTAGE_MV - 400)

#define GLOBAL_BUF_LEN 30
static char global_buf[GLOBAL_BUF_LEN];

static char phone_keypad_to_digit(char key);

static lv_timer_t *touch_chk_timer = NULL;
static lv_timer_t *taskbar_update_timer = NULL;
static lv_timer_t *low_battery_timer = NULL;
static lv_timer_t *phone_state_timer = NULL;
static lv_obj_t *label_list[10] = {0};
uint16_t taskbar_statue[TASKBAR_ID_MAX] = {0};

//************************************[ Other fun ]******************************************
#if 1
static lv_obj_t *scr_back_btn_create(lv_obj_t *parent, const char *text, lv_event_cb_t cb)
{
    lv_obj_t * btn = lv_btn_create(parent);
    lv_obj_remove_style_all(btn);
    lv_obj_set_style_pad_all(btn, 0, 0);
    lv_obj_set_height(btn, 30);
    lv_obj_align(btn, LV_ALIGN_TOP_LEFT, 3, 3);
    lv_obj_set_style_border_width(btn, 0, LV_PART_MAIN);
    lv_obj_set_style_shadow_width(btn, 0, LV_PART_MAIN);
    lv_obj_set_style_border_color(btn, DECKPRO_COLOR_FG, LV_PART_MAIN);
    lv_obj_set_style_bg_color(btn, DECKPRO_COLOR_BG, LV_PART_MAIN);
    lv_obj_add_event_cb(btn, cb, LV_EVENT_CLICKED, NULL);

    lv_obj_t *label2 = lv_label_create(btn);
    lv_obj_align(label2, LV_ALIGN_LEFT_MID, 0, 0);
    lv_obj_set_style_text_color(label2, DECKPRO_COLOR_FG, LV_PART_MAIN);
    lv_label_set_text(label2, LV_SYMBOL_LEFT);

    lv_obj_t *label = lv_label_create(parent);
    lv_obj_align_to(label, label2, LV_ALIGN_OUT_RIGHT_MID, 5, -1);
    lv_obj_set_style_text_font(label, FONT_BOLD_MONO_SIZE_15, LV_PART_MAIN);
    lv_obj_set_style_text_color(label, DECKPRO_COLOR_FG, LV_PART_MAIN);
    lv_label_set_text(label, text);
    lv_obj_add_flag(label, LV_OBJ_FLAG_CLICKABLE);
    lv_obj_add_event_cb(label, cb, LV_EVENT_CLICKED, NULL);
    lv_obj_set_ext_click_area(label, 20);

    return label;
}

static const char *line_full_format(int max_c, const char *str1, const char *str2)
{
    int len1 = 0, len2 = 0;
    int j;

    len1 = strlen(str1);

    strncpy(global_buf, str1, len1);

    len2 = strlen(str2);
    for(j = len1; j < max_c -1 - len2; j++){
        global_buf[j] = ' ';
    }
    strncpy(global_buf + j, str2, len2);
    j = j + len2;
    
    global_buf[j] = '\0'; 

    printf("[%d] buf: %s\n", __LINE__, global_buf);

    return (const char *)global_buf;
}

#endif
//************************************[ screen 0 ]****************************************** menu
#if 1
#define MENU_BTN_NUM (sizeof(menu_btn_list) / sizeof(menu_btn_list[0]))

static ui_indev_read_cb ui_get_gesture_dir = NULL;

static lv_obj_t *menu_screen1;
static lv_obj_t *menu_screen2;
static lv_obj_t *ui_Panel4;

static lv_obj_t * menu_taskbar = NULL;
static lv_obj_t * menu_taskbar_time = NULL;
static lv_obj_t * menu_taskbar_charge = NULL;
static lv_obj_t * menu_taskbar_battery = NULL;
static lv_obj_t * menu_taskbar_battery_percent = NULL;
static lv_obj_t * menu_taskbar_wifi = NULL;

static int page_num = 0;
static int page_curr = 0;

static struct menu_btn menu_btn_list[] = 
{
    {SCREEN1_ID,  &img_lora,    "Lora",     23,     13},  // Page one
    {SCREEN2_ID,  &img_setting, "Setting",  95,     13},
    {SCREEN3_ID,  &img_GPS,     "GPS",      167,    13},
    {SCREEN4_ID,  &img_wifi,    "Wifi",     23,     101},
    {SCREEN5_ID,  &img_test,    "Test",     95,     101},
    {SCREEN6_ID,  &img_batt,    "Battery",  167,    101},
    {SCREEN7_ID,  &img_touch,   "Input",    23,     189},
    {SCREEN8_ID,  &img_A7682E,  "Phone",    95,     189},
    {SCREEN9_ID,  &img_lora,    "Shutdown", 167,    189},
    {SCREEN10_ID, &img_music,   "Music",    23,     13},  // Page two
    {SCREEN11_ID, &img_sleep,   "Sleep",    95,     13},  // 
    {SCREEN12_ID, &img_motor,   "Motor",    167,    13},  // 
};

static void menu_btn_event_cb(lv_event_t *e)
{
    struct menu_btn *tgr = (struct menu_btn *)e->user_data;
    scr_mgr_push(tgr->idx, false);
}

static void menu_get_gesture_dir(int dir)
{
    if(MENU_BTN_NUM <= 9) return;

    if(dir == LV_DIR_LEFT) {
        if(page_curr < page_num){
            page_curr++;
            // ui_disp_full_refr();
        }
        else{
            return ;
        }
    } else if(dir == LV_DIR_RIGHT) {
        if(page_curr > 0){
            page_curr--;
        }
        else{
            return ;
        }
    }   

    if(page_curr == 1) {
        lv_obj_clear_flag(menu_screen2, LV_OBJ_FLAG_HIDDEN);
        lv_obj_add_flag(menu_screen1, LV_OBJ_FLAG_HIDDEN);
        lv_obj_set_style_bg_color(lv_obj_get_child(ui_Panel4, 0), lv_color_hex(0xFFFFFF), LV_PART_MAIN | LV_STATE_DEFAULT);
        lv_obj_set_style_bg_color(lv_obj_get_child(ui_Panel4, 1), lv_color_hex(0x000000), LV_PART_MAIN | LV_STATE_DEFAULT);

    } else if(page_curr == 0) {
        lv_obj_clear_flag(menu_screen1, LV_OBJ_FLAG_HIDDEN);
        lv_obj_add_flag(menu_screen2, LV_OBJ_FLAG_HIDDEN);
        lv_obj_set_style_bg_color(lv_obj_get_child(ui_Panel4, 0), lv_color_hex(0x000000), LV_PART_MAIN | LV_STATE_DEFAULT);
        lv_obj_set_style_bg_color(lv_obj_get_child(ui_Panel4, 1), lv_color_hex(0xFFFFFF), LV_PART_MAIN | LV_STATE_DEFAULT);
    }
}

static void menu_btn_create(lv_obj_t *parent, struct menu_btn *info)
{
    lv_obj_t * btn = lv_btn_create(parent);
    lv_obj_remove_style_all(btn);
    lv_obj_set_width(btn, 50);
    lv_obj_set_height(btn, 50);
    lv_obj_add_flag(btn, LV_OBJ_FLAG_OVERFLOW_VISIBLE | LV_OBJ_FLAG_SCROLL_ON_FOCUS);     /// Flags
    lv_obj_clear_flag(btn, LV_OBJ_FLAG_SCROLLABLE);      /// Flags
    lv_obj_set_style_radius(btn, 18, LV_PART_MAIN | LV_STATE_DEFAULT);
    lv_obj_set_style_border_width(btn, 0, LV_PART_MAIN | LV_STATE_DEFAULT);
    lv_obj_set_style_shadow_width(btn, 0, LV_PART_MAIN | LV_STATE_DEFAULT);
    lv_obj_set_style_shadow_spread(btn, 0, LV_PART_MAIN | LV_STATE_DEFAULT);
    lv_obj_set_style_bg_color(btn, lv_color_hex(0x000000), LV_PART_MAIN | LV_STATE_PRESSED);
    lv_obj_set_style_bg_opa(btn, 255, LV_PART_MAIN | LV_STATE_PRESSED);
    lv_obj_set_style_outline_width(btn, 3, LV_PART_MAIN | LV_STATE_PRESSED);

    lv_obj_t *label = lv_label_create(btn);
    lv_obj_set_style_text_font(label, FONT_BOLD_MONO_SIZE_14, LV_PART_MAIN);
    lv_obj_set_width(label, LV_SIZE_CONTENT);   /// 1
    lv_obj_set_height(label, LV_SIZE_CONTENT);    /// 1
    lv_obj_set_x(label, 0);
    lv_obj_set_y(label, 20);
    lv_obj_set_align(label, LV_ALIGN_BOTTOM_MID);
    lv_obj_set_style_text_color(label, lv_color_hex(0x000000), LV_PART_MAIN | LV_STATE_DEFAULT);
    lv_obj_set_style_text_opa(label, 255, LV_PART_MAIN | LV_STATE_DEFAULT);

    lv_obj_set_x(btn, info->pos_x);
    lv_obj_set_y(btn, info->pos_y);
    lv_obj_set_style_bg_img_src(btn, info->icon, LV_PART_MAIN | LV_STATE_DEFAULT);
    lv_label_set_text(label, (info->name));
    lv_obj_set_style_border_width(label, 0, LV_PART_MAIN | LV_STATE_DEFAULT);
    lv_obj_add_event_cb(btn, menu_btn_event_cb, LV_EVENT_CLICKED, (void *)info);
}

static void create0(lv_obj_t *parent) 
{
    int status_bar_height = 25;

    menu_taskbar = lv_obj_create(parent);
    lv_obj_set_size(menu_taskbar, LV_HOR_RES, status_bar_height);
    lv_obj_set_style_pad_all(menu_taskbar, 0, LV_PART_MAIN);
    lv_obj_set_style_border_width(menu_taskbar, 0, LV_PART_MAIN);
    lv_obj_set_scrollbar_mode(menu_taskbar, LV_SCROLLBAR_MODE_OFF);
    lv_obj_clear_flag(menu_taskbar, LV_OBJ_FLAG_SCROLLABLE);
    
    menu_taskbar_time = lv_label_create(menu_taskbar);
    lv_obj_set_style_border_width(menu_taskbar_time, 0, 0);
    lv_label_set_text_fmt(menu_taskbar_time, "%02d:%02d", 10, 19);
    lv_obj_set_style_text_font(menu_taskbar_time, &Font_Mono_Bold_14, LV_PART_MAIN);
    lv_obj_align(menu_taskbar_time, LV_ALIGN_LEFT_MID, 10, 0);

    lv_obj_t *status_parent = lv_obj_create(menu_taskbar);
    lv_obj_set_size(status_parent, lv_pct(80)-2, status_bar_height-2);
    lv_obj_set_style_pad_all(status_parent, 0, LV_PART_MAIN);
    lv_obj_set_style_border_width(status_parent, 0, LV_PART_MAIN);
    lv_obj_set_flex_flow(status_parent, LV_FLEX_FLOW_ROW);
    lv_obj_set_flex_align(status_parent, LV_FLEX_ALIGN_END, LV_FLEX_ALIGN_CENTER, LV_FLEX_ALIGN_CENTER);
    lv_obj_set_style_pad_left(status_parent, 0, LV_PART_MAIN | LV_STATE_DEFAULT);
    lv_obj_set_style_pad_right(status_parent, 5, LV_PART_MAIN | LV_STATE_DEFAULT);
    lv_obj_set_style_pad_top(status_parent, 0, LV_PART_MAIN | LV_STATE_DEFAULT);
    lv_obj_set_style_pad_bottom(status_parent, 0, LV_PART_MAIN | LV_STATE_DEFAULT);
    lv_obj_set_style_pad_row(status_parent, 0, LV_PART_MAIN | LV_STATE_DEFAULT);
    lv_obj_set_style_pad_column(status_parent, 5, LV_PART_MAIN | LV_STATE_DEFAULT);
    lv_obj_set_scrollbar_mode(status_parent, LV_SCROLLBAR_MODE_OFF);
    lv_obj_clear_flag(status_parent, LV_OBJ_FLAG_SCROLLABLE);
    lv_obj_align(status_parent, LV_ALIGN_RIGHT_MID, 0, 0);

    menu_taskbar_wifi = lv_label_create(status_parent);
    lv_label_set_text_fmt(menu_taskbar_wifi, "%s", LV_SYMBOL_WIFI);
    lv_obj_add_flag(menu_taskbar_wifi, LV_OBJ_FLAG_HIDDEN);

    menu_taskbar_charge = lv_label_create(status_parent);
    lv_label_set_text_fmt(menu_taskbar_charge, "%s", LV_SYMBOL_CHARGE);
    lv_obj_add_flag(menu_taskbar_charge, LV_OBJ_FLAG_HIDDEN);

    if(taskbar_statue[TASKBAR_ID_WIFI])
        lv_obj_clear_flag(menu_taskbar_wifi, LV_OBJ_FLAG_HIDDEN);

    if(taskbar_statue[TASKBAR_ID_CHARGE])
        lv_obj_clear_flag(menu_taskbar_charge, LV_OBJ_FLAG_HIDDEN);

    menu_taskbar_battery = lv_label_create(status_parent);
    
    menu_taskbar_battery_percent = lv_label_create(status_parent);
    lv_obj_set_style_text_font(menu_taskbar_battery_percent, &Font_Mono_Bold_14, LV_PART_MAIN);

    //
    page_num = MENU_BTN_NUM / 9;

    menu_screen1 = lv_obj_create(parent);
    lv_obj_set_size(menu_screen1, lv_pct(100), LV_VER_RES - status_bar_height);
    lv_obj_set_style_bg_color(menu_screen1, DECKPRO_COLOR_BG, LV_PART_MAIN);
    lv_obj_set_scrollbar_mode(menu_screen1, LV_SCROLLBAR_MODE_OFF);
    lv_obj_set_style_border_width(menu_screen1, 1, LV_PART_MAIN);
    lv_obj_set_style_border_color(menu_screen1, DECKPRO_COLOR_FG, LV_PART_MAIN);
    lv_obj_set_style_border_side(menu_screen1, LV_BORDER_SIDE_TOP, LV_PART_MAIN);
    lv_obj_set_style_pad_all(menu_screen1, 0, LV_PART_MAIN);
    lv_obj_align(menu_screen1, LV_ALIGN_BOTTOM_MID, 0, 0);
    // lv_obj_add_flag(menu_screen1, LV_OBJ_FLAG_HIDDEN);

    menu_screen2 = lv_obj_create(parent);
    lv_obj_set_size(menu_screen2, lv_pct(100), LV_VER_RES - status_bar_height);
    lv_obj_set_style_bg_color(menu_screen2, DECKPRO_COLOR_BG, LV_PART_MAIN);
    lv_obj_set_scrollbar_mode(menu_screen2, LV_SCROLLBAR_MODE_OFF);
    lv_obj_set_style_border_width(menu_screen2, 1, LV_PART_MAIN);
    lv_obj_set_style_border_color(menu_screen2, DECKPRO_COLOR_FG, LV_PART_MAIN);
    lv_obj_set_style_border_side(menu_screen2, LV_BORDER_SIDE_TOP, LV_PART_MAIN);
    lv_obj_set_style_pad_all(menu_screen2, 0, LV_PART_MAIN);
    lv_obj_align(menu_screen2, LV_ALIGN_BOTTOM_MID, 0, 0);
    lv_obj_add_flag(menu_screen2, LV_OBJ_FLAG_HIDDEN);

    for(int i = 0; i < MENU_BTN_NUM; i++) {
        if(i < 9) {
            menu_btn_create(menu_screen1, &menu_btn_list[i]);
        } else {
            menu_btn_create(menu_screen2, &menu_btn_list[i]);
        }
    }

    if(MENU_BTN_NUM > 9) {
        ui_Panel4 = lv_obj_create(parent);
        lv_obj_set_width(ui_Panel4, 240);
        lv_obj_set_height(ui_Panel4, 25);
        lv_obj_set_align(ui_Panel4, LV_ALIGN_BOTTOM_MID);
        lv_obj_set_flex_flow(ui_Panel4, LV_FLEX_FLOW_ROW);
        lv_obj_set_flex_align(ui_Panel4, LV_FLEX_ALIGN_CENTER, LV_FLEX_ALIGN_START, LV_FLEX_ALIGN_START);
        lv_obj_clear_flag(ui_Panel4, LV_OBJ_FLAG_SCROLLABLE);      /// Flags
        lv_obj_set_style_radius(ui_Panel4, 0, LV_PART_MAIN | LV_STATE_DEFAULT);
        lv_obj_set_style_bg_color(ui_Panel4, lv_color_hex(0xFFFFFF), LV_PART_MAIN | LV_STATE_DEFAULT);
        lv_obj_set_style_bg_opa(ui_Panel4, 0, LV_PART_MAIN | LV_STATE_DEFAULT);
        lv_obj_set_style_border_width(ui_Panel4, 0, LV_PART_MAIN | LV_STATE_DEFAULT);
        lv_obj_set_style_shadow_width(ui_Panel4, 0, LV_PART_MAIN | LV_STATE_DEFAULT);
        lv_obj_set_style_shadow_spread(ui_Panel4, 0, LV_PART_MAIN | LV_STATE_DEFAULT);
        lv_obj_set_style_border_width(ui_Panel4, 0, LV_PART_SCROLLBAR | LV_STATE_DEFAULT);
        lv_obj_set_style_shadow_width(ui_Panel4, 0, LV_PART_SCROLLBAR | LV_STATE_DEFAULT);
        lv_obj_set_style_shadow_spread(ui_Panel4, 0, LV_PART_SCROLLBAR | LV_STATE_DEFAULT);

        lv_obj_t *ui_Button11 = lv_btn_create(ui_Panel4);
        lv_obj_set_width(ui_Button11, 10);
        lv_obj_set_height(ui_Button11, 10);
        lv_obj_add_flag(ui_Button11, LV_OBJ_FLAG_SCROLL_ON_FOCUS);     /// Flags
        lv_obj_clear_flag(ui_Button11, LV_OBJ_FLAG_CHECKABLE);      /// Flags
        lv_obj_set_style_radius(ui_Button11, 10, LV_PART_MAIN | LV_STATE_DEFAULT);
        lv_obj_set_style_border_width(ui_Button11, 2, LV_PART_MAIN | LV_STATE_DEFAULT);
        lv_obj_set_style_bg_color(ui_Button11, DECKPRO_COLOR_FG, LV_PART_MAIN | LV_STATE_DEFAULT);

        lv_obj_t *ui_Button12 = lv_btn_create(ui_Panel4);
        lv_obj_set_width(ui_Button12, 10);
        lv_obj_set_height(ui_Button12, 10);
        lv_obj_add_flag(ui_Button12, LV_OBJ_FLAG_SCROLL_ON_FOCUS);     /// Flags
        lv_obj_clear_flag(ui_Button12, LV_OBJ_FLAG_CHECKABLE);      /// Flags
        lv_obj_set_style_radius(ui_Button12, 10, LV_PART_MAIN | LV_STATE_DEFAULT);
        lv_obj_set_style_border_width(ui_Button12, 2, LV_PART_MAIN | LV_STATE_DEFAULT);
    }
}

static void entry0(void) {
    ui_get_gesture_dir = menu_get_gesture_dir;
    lv_timer_resume(touch_chk_timer);
    lv_timer_resume(taskbar_update_timer);

    lv_label_set_text_fmt(menu_taskbar_battery, "%s", ui_battert_27220_get_percent_level());

    lv_label_set_text_fmt(menu_taskbar_battery_percent, "%d", ui_battery_27220_get_percent());
}
static void exit0(void) {
    ui_get_gesture_dir = NULL;
    lv_timer_pause(touch_chk_timer);
    lv_timer_pause(taskbar_update_timer);
}
static void destroy0(void) {
    if(menu_taskbar) {
        lv_obj_del(menu_taskbar);
        menu_taskbar = NULL;
    }
}

static scr_lifecycle_t screen0 = {
    .create = create0,
    .entry = entry0,
    .exit  = exit0,
    .destroy = destroy0,
};
#endif
//************************************[ screen 1 ]****************************************** lora
// --------------------- screen 1 --------------------- lora
#if 1
lv_obj_t * scr1_list;
static lv_obj_t *scr1_lab_buf[20];

static void scr1_list_event(lv_event_t *e)
{
    lv_event_code_t code = lv_event_get_code(e);
    lv_obj_t * obj = lv_event_get_target(e);
    for(int i = 0; i < lv_obj_get_child_cnt(obj); i++) 
    {
        lv_obj_t * child = lv_obj_get_child(obj, i);
        if(lv_obj_check_type(child, &lv_label_class)) {
            char *str = lv_label_get_text(child);

            if(strcmp("- Auto Test", str) == 0)
            {
                scr_mgr_push(SCREEN1_1_ID, false);
            }
            if(strcmp("- Lora Setting", str) == 0)
            {
                scr_mgr_push(SCREEN1_2_ID, false);
            }
            printf("%s\n", str);
        }
    }
}

static void scr1_item_create(const char *name, lv_event_cb_t cb)
{
    lv_obj_t * obj = lv_obj_class_create_obj(&lv_list_btn_class, scr1_list);
    lv_obj_class_init_obj(obj);
    lv_obj_set_size(obj, LV_PCT(100), LV_SIZE_CONTENT);

    lv_obj_t *label = lv_label_create(obj);
    lv_label_set_text(label, name);
    lv_label_set_long_mode(label, LV_LABEL_LONG_SCROLL_CIRCULAR);
    lv_obj_align(label, LV_ALIGN_LEFT_MID, 10, 0);

    lv_obj_set_height(obj, LV_VER_RES / 6);
    lv_obj_set_style_text_font(obj, FONT_BOLD_SIZE_15, LV_PART_MAIN);
    // lv_obj_set_style_bg_color(obj, lv_color_hex(EPD_COLOR_BG), LV_PART_MAIN);
    // lv_obj_set_style_text_color(obj, lv_color_hex(EPD_COLOR_FG), LV_PART_MAIN);
    lv_obj_set_style_border_width(obj, 1, LV_PART_MAIN | LV_STATE_DEFAULT);
    lv_obj_set_style_border_width(obj, 1, LV_PART_MAIN | LV_STATE_PRESSED);
    lv_obj_set_style_outline_width(obj, 1, LV_PART_MAIN | LV_STATE_PRESSED);
    lv_obj_set_style_radius(obj, 10, LV_PART_MAIN | LV_STATE_DEFAULT);

    lv_obj_add_event_cb(obj, cb, LV_EVENT_CLICKED, NULL); 
}

static void scr1_btn_event_cb(lv_event_t * e)
{
    if(e->code == LV_EVENT_CLICKED){
        // ui_full_refresh();
        scr_mgr_pop(false);
    }
}

static void create1(lv_obj_t *parent) 
{
    scr1_list = lv_list_create(parent);
    lv_obj_set_size(scr1_list, lv_pct(93), lv_pct(91));
    lv_obj_align(scr1_list, LV_ALIGN_BOTTOM_MID, 0, 0);
    // lv_obj_set_style_bg_color(scr1_list, lv_color_hex(EPD_COLOR_BG), LV_PART_MAIN);
    lv_obj_set_style_pad_top(scr1_list, 10, LV_PART_MAIN);
    lv_obj_set_style_pad_row(scr1_list, 15, LV_PART_MAIN);
    lv_obj_set_style_radius(scr1_list, 0, LV_PART_MAIN);
    // lv_obj_set_style_outline_pad(scr1_list, 1, LV_PART_MAIN);
    lv_obj_set_style_border_width(scr1_list, 0, LV_PART_MAIN);
    // lv_obj_set_style_border_color(scr1_list, lv_color_hex(EPD_COLOR_FG), LV_PART_MAIN);
    lv_obj_set_style_shadow_width(scr1_list, 0, LV_PART_MAIN);

    scr1_item_create("- Auto Test", scr1_list_event);
    scr1_item_create("- Lora Setting", scr1_list_event);

    // back
    scr_back_btn_create(parent, "Lora", scr1_btn_event_cb);
}

static void entry1(void) 
{
    ui_disp_full_refr();
}
static void exit1(void) {
    ui_disp_full_refr();
}
static void destroy1(void) { }

static scr_lifecycle_t screen1 = {
    .create = create1,
    .entry = entry1,
    .exit  = exit1,
    .destroy = destroy1,
};
#endif
// --------------------- screen 1.1 --------------------- Auto Send
#if 1
static lv_obj_t *scr1_1_cont;
static lv_obj_t *lora_lab_buf[11] = {0};
static lv_obj_t *lora_sw_btn;
static lv_obj_t *lora_sw_btn_info;
static lv_timer_t *lora_RT_timer = NULL;
static lv_timer_t *lora_recv_timer = NULL;
static int lora_cnt = 0;

static void scr1_1_btn_event_cb(lv_event_t * e)
{
    if(e->code == LV_EVENT_CLICKED){
        scr_mgr_pop(false);
    }
}

static void lora_mode_sw_event(lv_event_t * e)
{
    if(e->code == LV_EVENT_CLICKED){
        if(ui_lora_get_mode() == LORA_MODE_SEND) {
            ui_lora_set_mode(LORA_MODE_RECV);
            lv_label_set_text(lora_sw_btn_info, "Recv");
            for(int i = 0; i < GET_BUFF_LEN(lora_lab_buf); i++){
                lv_label_set_text_fmt(lora_lab_buf[i], " ", i);
            }
            lora_cnt = 0;
        } else if(ui_lora_get_mode() == LORA_MODE_RECV) {
            ui_lora_set_mode(LORA_MODE_SEND);
            lv_label_set_text(lora_sw_btn_info, "Send");
            for(int i = 0; i < GET_BUFF_LEN(lora_lab_buf); i++){
                lv_label_set_text_fmt(lora_lab_buf[i], " ", i);
            }
            lora_cnt = 0;
        }
    }
}

static void lora_recv_loop_event(lv_timer_t *t)
{
    ui_lora_recv_loop();
}

static void lora_RT_timer_event(lv_timer_t *t)
{
    static int data = 0;
    char buf[32];
    const char *recv_info = NULL;
    int recv_rssi = 0;
    
    if(ui_lora_get_mode() == LORA_MODE_SEND) 

    {
        lv_snprintf(buf, 32, "DeckPro #%d", data++);
        lv_label_set_text_fmt(lora_lab_buf[lora_cnt], "send-> %s", buf);
        ui_lora_send(buf);

        lora_cnt++;
        if(lora_cnt >= GET_BUFF_LEN(lora_lab_buf)) {
            lora_cnt = 0;
        }
    }
    else if(ui_lora_get_mode() == LORA_MODE_RECV)
    {
        if(ui_lora_get_recv(&recv_info, &recv_rssi))
        {
            ui_lora_set_recv_flag();
            lv_label_set_text_fmt(lora_lab_buf[lora_cnt], "recv-> %s [%d]", recv_info, recv_rssi);

            lora_cnt++;
            if(lora_cnt >= GET_BUFF_LEN(lora_lab_buf)) {
                lora_cnt = 0;
            }
        }
    }
}

static lv_obj_t * scr2_create_label(lv_obj_t *parent)
{
    lv_obj_t *label = lv_label_create(parent);
    lv_obj_set_width(label, LV_HOR_RES - 26);
    lv_obj_set_style_text_font(label, FONT_BOLD_SIZE_15, LV_PART_MAIN);   
    lv_obj_set_style_border_width(label, 0, LV_PART_MAIN);
    lv_label_set_long_mode(label, LV_LABEL_LONG_CLIP);
    return label;
}
static void create1_1(lv_obj_t *parent) 
{
    scr1_1_cont = lv_obj_create(parent);
    lv_obj_set_size(scr1_1_cont, lv_pct(100), lv_pct(85));
    lv_obj_set_style_bg_color(scr1_1_cont, DECKPRO_COLOR_BG, LV_PART_MAIN);
    lv_obj_set_scrollbar_mode(scr1_1_cont, LV_SCROLLBAR_MODE_OFF);
    lv_obj_clear_flag(scr1_1_cont, LV_OBJ_FLAG_SCROLLABLE);
    lv_obj_set_style_border_width(scr1_1_cont, 0, LV_PART_MAIN);
    lv_obj_set_style_pad_all(scr1_1_cont, 0, LV_PART_MAIN);
    lv_obj_set_style_pad_left(scr1_1_cont, 13, LV_PART_MAIN);
    lv_obj_set_flex_flow(scr1_1_cont, LV_FLEX_FLOW_COLUMN);
    lv_obj_set_style_pad_row(scr1_1_cont, 5, LV_PART_MAIN);
    lv_obj_set_style_pad_column(scr1_1_cont, 5, LV_PART_MAIN);
    lv_obj_set_align(scr1_1_cont, LV_ALIGN_BOTTOM_MID);

    for(int i = 0; i < GET_BUFF_LEN(lora_lab_buf); i++){
        lora_lab_buf[i] = scr2_create_label(scr1_1_cont);
        lv_label_set_text_fmt(lora_lab_buf[i], " ", i);
    }

    lora_sw_btn = lv_btn_create(parent);
    lv_obj_set_size(lora_sw_btn, 70, 25);
    lv_obj_set_style_radius(lora_sw_btn, 5, LV_PART_MAIN);
    lv_obj_set_style_border_width(lora_sw_btn, 2, LV_PART_MAIN);
    lora_sw_btn_info = lv_label_create(lora_sw_btn);
    lv_obj_set_style_text_font(lora_sw_btn_info, FONT_BOLD_SIZE_15, LV_PART_MAIN);
    lv_obj_set_style_text_align(lora_sw_btn_info, LV_TEXT_ALIGN_CENTER, 0);
    lv_label_set_text(lora_sw_btn_info, "Send");
    lv_obj_center(lora_sw_btn_info);
    lv_obj_align(lora_sw_btn, LV_ALIGN_TOP_MID, 0, 5);
    lv_obj_add_event_cb(lora_sw_btn, lora_mode_sw_event, LV_EVENT_CLICKED, NULL);

    lv_obj_t *lab = lv_label_create(parent);
    lv_obj_set_style_text_font(lab, FONT_BOLD_SIZE_15, LV_PART_MAIN);
    lv_label_set_text_fmt(lab, "%.1fM", ui_lora_get_freq());
    lv_obj_align(lab, LV_ALIGN_TOP_RIGHT, -10, 10);

    ui_lora_set_mode(LORA_MODE_SEND);
    lora_cnt = 0;

    // back
    scr_back_btn_create(parent, ("Lora"), scr1_1_btn_event_cb);
}
static void entry1_1(void) 
{
    ui_disp_full_refr();
    lora_RT_timer = lv_timer_create(lora_RT_timer_event, 2000, NULL);
    lora_recv_timer = lv_timer_create(lora_recv_loop_event, 400, NULL);
}
static void exit1_1(void) {
    ui_disp_full_refr();
    if(lora_RT_timer) {
        lv_timer_del(lora_RT_timer);
        lora_RT_timer = NULL;
    }
    if(lora_recv_timer) {
        lv_timer_del(lora_recv_timer);
        lora_recv_timer = NULL;
    }
}
static void destroy1_1(void) { }

static scr_lifecycle_t screen1_1 = {
    .create = create1_1,
    .entry = entry1_1,
    .exit  = exit1_1,
    .destroy = destroy1_1,
};
#endif
// --------------------- screen 1.2 --------------------- Lora Setting
#if 1

#define RADIO_FREQUENCY_LIST "433MHz\n 850MHz\n 868MHz\n 915MHz\n 920MHz"
#define RADIO_BANDWIDTH "125KHz\n 250KHz\n 500KHz"
#define RADIO_TX_POWER "10dBm\n 22dBm"
//   HIGH --- internal antenna 
//   LOW --- external antenna
#define RADIO_ANTENNA_DIR "internal\n external"

static float lora_freq_list[] = {433.0, 850.0, 868.0, 915.0, 920.0};
static int lora_band_list[] = {125, 250, 500};
static int lora_power_list[] = {10, 22};
static bool lora_antenna_list[] = {1, 0};

static lv_obj_t *scr1_2_cont;
static lv_obj_t *dropdown_antenna;
static lv_obj_t *dropdown_freq;
static lv_obj_t *dropdown_band;
static lv_obj_t *dropdown_power;

static void scr1_2_btn_event_cb(lv_event_t * e)
{
    if(e->code == LV_EVENT_CLICKED){
        scr_mgr_pop(false);
    }
}

static void lora_setting_event_handler(lv_event_t * e)
{
    char buf[32]={0};
    lv_event_code_t code = lv_event_get_code(e);
    lv_obj_t * obj = lv_event_get_target(e);
    const char *flag = ( const char *)lv_event_get_user_data(e);
    int select = lv_dropdown_get_selected(obj);

    lv_dropdown_get_selected_str(obj, buf, sizeof(buf));
    switch (*flag)
    {
    case 'a':
        for(int i = 0; i < GET_BUFF_LEN(lora_antenna_list); i++) {
            if(lora_antenna_list[select] == lora_antenna_list[i]) {
                printf("set antenna dir %s\n", (lora_antenna_list[i] ? "internal" : "external"));
                ui_lora_set_ante_dir(lora_antenna_list[i]);
            }
        }
        break;
    case 'f': 
        for(int i = 0; i < GET_BUFF_LEN(lora_freq_list); i++) {
            if(lora_freq_list[select] == lora_freq_list[i]) {
                printf("set freq %.1fMHz\n", lora_freq_list[i]);
                ui_lora_set_freq(lora_freq_list[i]);
            }
        }
        break;
    case 'b': 
        for(int i = 0; i < GET_BUFF_LEN(lora_band_list); i++) {
            if(lora_band_list[select] == lora_band_list[i]) {
                printf("set bandwidth %dKhz\n", lora_band_list[i]);
                ui_lora_set_bandwidth(lora_band_list[i]);
            }
        }
        break;
    case 'p': 
        for(int i = 0; i < GET_BUFF_LEN(lora_power_list); i++) {
            if(lora_power_list[select] == lora_power_list[i]) {
                printf("set power %ddBm\n", lora_power_list[i]);
                ui_lora_set_power(lora_power_list[i]);
            }
        }
        break;
    
    default:
        break;
    }
}

static lv_obj_t * scr1_2_lora_setting_create(lv_obj_t *parent, const char *text, int width)
{
    lv_obj_t *ui_Container1 = lv_obj_create(parent);
    lv_obj_remove_style_all(ui_Container1);
    lv_obj_set_height(ui_Container1, 42);
    lv_obj_set_width(ui_Container1, lv_pct(100));
    lv_obj_set_x(ui_Container1, 35);
    lv_obj_set_y(ui_Container1, -16);
    lv_obj_set_align(ui_Container1, LV_ALIGN_CENTER);
    lv_obj_set_flex_flow(ui_Container1, LV_FLEX_FLOW_ROW);
    lv_obj_set_flex_align(ui_Container1, LV_FLEX_ALIGN_CENTER, LV_FLEX_ALIGN_CENTER, LV_FLEX_ALIGN_START);
    lv_obj_clear_flag(ui_Container1, LV_OBJ_FLAG_CLICKABLE | LV_OBJ_FLAG_SCROLLABLE);      /// Flags
    lv_obj_set_style_pad_row(ui_Container1, 0, LV_PART_MAIN | LV_STATE_DEFAULT);
    lv_obj_set_style_pad_column(ui_Container1, 20, LV_PART_MAIN | LV_STATE_DEFAULT);

    lv_obj_t *ui_Label14 = lv_label_create(ui_Container1);
    lv_obj_set_width(ui_Label14, LV_SIZE_CONTENT);   /// 1
    lv_obj_set_height(ui_Label14, LV_SIZE_CONTENT);    /// 1
    lv_obj_set_x(ui_Label14, -60);
    lv_obj_set_y(ui_Label14, -42);
    lv_obj_set_align(ui_Label14, LV_ALIGN_CENTER);
    lv_label_set_text(ui_Label14, text);
    lv_obj_set_style_text_font(ui_Label14, FONT_BOLD_MONO_SIZE_15, LV_PART_MAIN);   

    lv_obj_t *ui_Dropdown1 = lv_dropdown_create(ui_Container1);
    lv_obj_set_width(ui_Dropdown1, width);
    lv_obj_set_height(ui_Dropdown1, LV_SIZE_CONTENT);    /// 1
    lv_obj_set_x(ui_Dropdown1, 19);
    lv_obj_set_y(ui_Dropdown1, -1);
    lv_obj_add_flag(ui_Dropdown1, LV_OBJ_FLAG_SCROLL_ON_FOCUS);     /// Flags

    // lv_obj_set_style_bg_opa(ui_Dropdown1, LV_OPA_TRANSP, LV_PART_MAIN | LV_STATE_PRESSED);
    lv_obj_set_style_border_width(ui_Dropdown1, 1, LV_PART_MAIN | LV_STATE_PRESSED);
    // lv_obj_set_style_shadow_width(ui_Dropdown1, LV_OPA_TRANSP, LV_PART_MAIN | LV_STATE_PRESSED);

    return ui_Dropdown1;
}

static void create1_2(lv_obj_t *parent) 
{
    scr1_2_cont = lv_obj_create(parent);
    lv_obj_remove_style_all(scr1_2_cont);
    lv_obj_set_width(scr1_2_cont, lv_pct(100));
    lv_obj_set_height(scr1_2_cont, lv_pct(85));
    lv_obj_set_align(scr1_2_cont, LV_ALIGN_CENTER);
    lv_obj_set_flex_flow(scr1_2_cont, LV_FLEX_FLOW_COLUMN);
    lv_obj_set_flex_align(scr1_2_cont, LV_FLEX_ALIGN_START, LV_FLEX_ALIGN_START, LV_FLEX_ALIGN_START);
    lv_obj_clear_flag(scr1_2_cont, LV_OBJ_FLAG_CLICKABLE | LV_OBJ_FLAG_SCROLLABLE);      /// Flags
    lv_obj_set_style_pad_row(scr1_2_cont, 10, LV_PART_MAIN | LV_STATE_DEFAULT);
    lv_obj_set_style_pad_column(scr1_2_cont, 0, LV_PART_MAIN | LV_STATE_DEFAULT);
    // lv_obj_set_style_border_width(scr1_2_cont, 3, LV_PART_MAIN);
    lv_obj_set_align(scr1_2_cont, LV_ALIGN_BOTTOM_MID);

    dropdown_antenna = scr1_2_lora_setting_create(scr1_2_cont, "Antenna:", lv_pct(52));
    lv_dropdown_set_options(dropdown_antenna, RADIO_ANTENNA_DIR);
    for(int i = 0; i < GET_BUFF_LEN(lora_antenna_list); i++) {
        if(ui_lora_get_ante_dir() == lora_antenna_list[i]) {
            lv_dropdown_set_selected(dropdown_antenna, i);
        }
    }

    dropdown_freq = scr1_2_lora_setting_create(scr1_2_cont, "Freq: ", lv_pct(60));
    lv_dropdown_set_options(dropdown_freq, RADIO_FREQUENCY_LIST);
    for(int i = 0; i < GET_BUFF_LEN(lora_freq_list); i++) {
        if(ui_lora_get_freq() == lora_freq_list[i]) {
            lv_dropdown_set_selected(dropdown_freq, i);
        }
    }

    dropdown_band = scr1_2_lora_setting_create(scr1_2_cont, "Band: ", lv_pct(60));
    lv_dropdown_set_options(dropdown_band, RADIO_BANDWIDTH);
    for(int i = 0; i < GET_BUFF_LEN(lora_band_list); i++) {
        if(ui_lora_get_bandwidth() == lora_band_list[i]) {
            lv_dropdown_set_selected(dropdown_band, i);
        }
    }

    dropdown_power = scr1_2_lora_setting_create(scr1_2_cont, "Power:", lv_pct(60));
    lv_dropdown_set_options(dropdown_power, RADIO_TX_POWER);
    for(int i = 0; i < GET_BUFF_LEN(lora_power_list); i++) {
        if(ui_lora_get_power() == lora_power_list[i]) {
            lv_dropdown_set_selected(dropdown_power, i);
        }
    }
    static const char ante_flag = 'a';
    static const char freq_flag = 'f';
    static const char band_flag = 'b';
    static const char power_flag = 'p';
    lv_obj_add_event_cb(dropdown_antenna, lora_setting_event_handler, LV_EVENT_VALUE_CHANGED, (void *)&ante_flag);
    lv_obj_add_event_cb(dropdown_freq, lora_setting_event_handler, LV_EVENT_VALUE_CHANGED, (void *)&freq_flag);
    lv_obj_add_event_cb(dropdown_band, lora_setting_event_handler, LV_EVENT_VALUE_CHANGED, (void *)&band_flag);
    lv_obj_add_event_cb(dropdown_power,   lora_setting_event_handler, LV_EVENT_VALUE_CHANGED, (void *)&power_flag);
    // back
    scr_back_btn_create(parent, ("Lora Setting"), scr1_2_btn_event_cb);
}
static void entry1_2(void) 
{
    ui_disp_full_refr();
}
static void exit1_2(void) {
    ui_disp_full_refr();
    ui_lora_param_set();
}
static void destroy1_2(void) { }

static scr_lifecycle_t screen1_2 = {
    .create = create1_2,
    .entry = entry1_2,
    .exit  = exit1_2,
    .destroy = destroy1_2,
};
#endif
//************************************[ screen 2 ]****************************************** Setting
// --------------------- screen 2.1 --------------------- About System
#if 1
static lv_obj_t *scr2_1_cont;

static void scr2_1_btn_event_cb(lv_event_t * e)
{
    if(e->code == LV_EVENT_CLICKED){
        scr_mgr_pop(false);
    }
}

static void create2_1(lv_obj_t *parent) 
{
    lv_obj_t *info = lv_label_create(parent);
    lv_obj_set_width(info, LV_HOR_RES * 0.9);
    lv_obj_set_style_text_color(info, DECKPRO_COLOR_FG, LV_PART_MAIN);
    lv_obj_set_style_text_font(info, &Font_Mono_Bold_14, LV_PART_MAIN);
    lv_obj_set_style_text_align(info, LV_TEXT_ALIGN_CENTER, 0);
    lv_label_set_long_mode(info, LV_LABEL_LONG_WRAP);

    String str = "";

    str += "                           \n";
    str += line_full_format(28, "SF Version:", ui_setting_get_sf_ver());
    str += "\n                           \n";

    str += line_full_format(28, "HD Version:", ui_setting_get_hd_ver());
    str += "\n                           \n";

    char buf[30];
    uint64_t total=0, used=0;
    ui_setting_get_sd_capacity(&total, &used);
    lv_snprintf(buf, 30, "%lluMB", total);
    str += line_full_format(28, "SD total:", (const char *)buf);
    str += "\n                           \n";

    lv_snprintf(buf, 30, "%lluMB", used);
    str += line_full_format(28, "SD used:", (const char *)buf);
    str += "\n                           \n";


    lv_label_set_text_fmt(info, "%s", str.c_str());
    
    lv_obj_align(info, LV_ALIGN_TOP_MID, 0, 35);
    
    lv_obj_t *back2_1_label = scr_back_btn_create(parent, ("About System"), scr2_1_btn_event_cb);
}
static void entry2_1(void) 
{
    ui_disp_full_refr();
}
static void exit2_1(void) {
    ui_disp_full_refr();
}
static void destroy2_1(void) { }

static scr_lifecycle_t screen2_1 = {
    .create = create2_1,
    .entry = entry2_1,
    .exit  = exit2_1,
    .destroy = destroy2_1,
};
#endif
// --------------------- screen 2 --------------------- Setting
#if 1
static lv_obj_t *setting_list;
static lv_obj_t *setting_page;
static int setting_num = 0;
static int setting_page_num = 0;
static int setting_curr_page = 0;
static ui_setting_handle setting_handle_list[] = {
    {.name = "Keypad Backlight", .type=UI_SETTING_TYPE_SW,  .set_cb = ui_setting_set_keypad_light, .get_cb = ui_setting_get_keypad_light},
    {.name = "Motor Status",     .type=UI_SETTING_TYPE_SW,  .set_cb = ui_setting_set_motor_status, .get_cb = ui_setting_get_motor_status},
    {.name = "Power GPS",        .type=UI_SETTING_TYPE_SW,  .set_cb = ui_setting_set_gps_status,   .get_cb = ui_setting_get_gps_status},
    {.name = "Power Lora",       .type=UI_SETTING_TYPE_SW,  .set_cb = ui_setting_set_lora_status,  .get_cb = ui_setting_get_lora_status},
    {.name = "Power Gyro",       .type=UI_SETTING_TYPE_SW,  .set_cb = ui_setting_set_gyro_status,  .get_cb = ui_setting_get_gyro_status},
    {.name = "Power A7682",      .type=UI_SETTING_TYPE_SW,  .set_cb = ui_setting_set_a7682_status, .get_cb = ui_setting_get_a7682_status},
    {.name = "- About System",   .type=UI_SETTING_TYPE_SUB, .sub_id = SCREEN2_1_ID},
};

static void setting_item_create(int curr_apge);

static void scr2_btn_event_cb(lv_event_t * e)
{
    if(e->code == LV_EVENT_CLICKED){
        scr_mgr_pop(false);
    }
}

static void setting_scr_event(lv_event_t *e)
{
    lv_obj_t *tgt = (lv_obj_t *)e->target;
    ui_setting_handle *h = (ui_setting_handle *)e->user_data;

    if(e->code == LV_EVENT_CLICKED) {
        switch (h->type)
        {
        case UI_SETTING_TYPE_SW:
            h->set_cb(!h->get_cb());
            lv_label_set_text_fmt(h->st, "%s", (h->get_cb() ? "ON" : "OFF"));
            break;
        case UI_SETTING_TYPE_SUB:
            scr_mgr_push(h->sub_id, false);
            break;
        default:
            break;
        }
    }
}

static void setting_page_switch_cb(lv_event_t *e)
{
    char opt = (int)e->user_data;
    
    if(setting_num < SETTING_PAGE_MAX_ITEM) return;

    int child_cnt = lv_obj_get_child_cnt(setting_list);
    
    for(int i = 0; i < child_cnt; i++)
    {
        lv_obj_t *child = lv_obj_get_child(setting_list, 0);
        if(child)
            lv_obj_del(child);
    }

    if(opt == 'p')
    {
        setting_curr_page = (setting_curr_page < setting_page_num) ? setting_curr_page + 1 : 0;
    }
    else if(opt == 'n')
    {
        setting_curr_page = (setting_curr_page > 0) ? setting_curr_page - 1 : setting_page_num;
    }

    setting_item_create(setting_curr_page);
    lv_label_set_text_fmt(setting_page, "%d / %d", setting_curr_page, setting_page_num);
}

static void setting_item_create(int curr_apge)
{
    printf("setting_curr_page = %d\n", setting_curr_page);
    int start = (curr_apge * SETTING_PAGE_MAX_ITEM);
    int end = start + SETTING_PAGE_MAX_ITEM;
    if(end > setting_num) end = setting_num;

    printf("start=%d, end=%d\n", start, end);

    for(int i = start; i < end; i++) {
        ui_setting_handle *h = &setting_handle_list[i];
        

        switch (h->type)
        {
        case UI_SETTING_TYPE_SW:
            h->obj = lv_list_add_btn(setting_list, NULL, h->name);
            h->st = lv_label_create(h->obj);
            lv_obj_set_style_text_font(h->st, FONT_BOLD_SIZE_15, LV_PART_MAIN);
            lv_obj_align(h->st, LV_ALIGN_RIGHT_MID, 0, 0);
            lv_label_set_text_fmt(h->st, "%s", (h->get_cb() ? "ON" : "OFF"));
            break;
        case UI_SETTING_TYPE_SUB:
            h->obj = lv_list_add_btn(setting_list, NULL, h->name);
            break;
        default:
            break;
        }

        // style
        lv_obj_set_height(h->obj, 28);
        lv_obj_set_style_text_font(h->obj, FONT_BOLD_SIZE_14, LV_PART_MAIN);
        lv_obj_set_style_bg_color(h->obj, DECKPRO_COLOR_BG, LV_PART_MAIN);
        lv_obj_set_style_text_color(h->obj, DECKPRO_COLOR_FG, LV_PART_MAIN);
        lv_obj_set_style_border_width(h->obj, 1, LV_PART_MAIN | LV_STATE_DEFAULT);
        lv_obj_set_style_border_width(h->obj, 1, LV_PART_MAIN | LV_STATE_PRESSED);
        lv_obj_set_style_outline_width(h->obj, 3, LV_PART_MAIN | LV_STATE_PRESSED);
        lv_obj_set_style_radius(h->obj, 5, LV_PART_MAIN | LV_STATE_DEFAULT);
        lv_obj_add_event_cb(h->obj, setting_scr_event, LV_EVENT_CLICKED, (void *)h);
    }
}

static void create2(lv_obj_t *parent) 
{
    setting_list = lv_list_create(parent);
    lv_obj_set_size(setting_list, LV_HOR_RES, lv_pct(88));
    lv_obj_align(setting_list, LV_ALIGN_BOTTOM_MID, 0, 0);
    lv_obj_set_style_bg_color(setting_list, DECKPRO_COLOR_BG, LV_PART_MAIN);
    lv_obj_set_style_pad_top(setting_list, 2, LV_PART_MAIN);
    lv_obj_set_style_pad_row(setting_list, 3, LV_PART_MAIN);
    lv_obj_set_style_radius(setting_list, 0, LV_PART_MAIN);
    // lv_obj_set_style_outline_pad(setting_list, 2, LV_PART_MAIN);
    lv_obj_set_style_border_width(setting_list, 0, LV_PART_MAIN);
    lv_obj_set_style_border_color(setting_list, DECKPRO_COLOR_FG, LV_PART_MAIN);
    lv_obj_set_style_shadow_width(setting_list, 0, LV_PART_MAIN);

    setting_num = sizeof(setting_handle_list) / sizeof(setting_handle_list[0]);
    setting_page_num = setting_num / SETTING_PAGE_MAX_ITEM;

    setting_item_create(setting_curr_page);

    lv_obj_t * ui_Button2 = lv_btn_create(parent);
    lv_obj_set_width(ui_Button2, 71);
    lv_obj_set_height(ui_Button2, 40);
    lv_obj_set_x(ui_Button2, -70);
    lv_obj_set_y(ui_Button2, 130);
    lv_obj_set_align(ui_Button2, LV_ALIGN_CENTER);
    lv_obj_add_flag(ui_Button2, LV_OBJ_FLAG_SCROLL_ON_FOCUS);     /// Flags
    lv_obj_clear_flag(ui_Button2, LV_OBJ_FLAG_SCROLLABLE);      /// Flags
    lv_obj_set_style_bg_color(ui_Button2, lv_color_hex(0xFFFFFF), LV_PART_MAIN | LV_STATE_DEFAULT);
    lv_obj_set_style_bg_opa(ui_Button2, 255, LV_PART_MAIN | LV_STATE_DEFAULT);
    lv_obj_set_style_border_width(ui_Button2, 2, LV_PART_MAIN | LV_STATE_DEFAULT);
    lv_obj_set_style_shadow_width(ui_Button2, 0, LV_PART_MAIN | LV_STATE_DEFAULT);
    lv_obj_set_style_shadow_spread(ui_Button2, 0, LV_PART_MAIN | LV_STATE_DEFAULT);
    lv_obj_set_style_border_width(ui_Button2, 0, LV_PART_MAIN | LV_STATE_CHECKED | LV_STATE_PRESSED);
    lv_obj_set_style_shadow_width(ui_Button2, 0, LV_PART_MAIN | LV_STATE_CHECKED | LV_STATE_PRESSED);
    lv_obj_set_style_shadow_spread(ui_Button2, 0, LV_PART_MAIN | LV_STATE_CHECKED | LV_STATE_PRESSED);
    lv_obj_set_style_radius(ui_Button2, 10, LV_PART_MAIN | LV_STATE_DEFAULT);

    lv_obj_t * ui_Label1 = lv_label_create(ui_Button2);
    lv_obj_set_width(ui_Label1, LV_SIZE_CONTENT);   /// 1
    lv_obj_set_height(ui_Label1, LV_SIZE_CONTENT);    /// 1
    lv_obj_set_align(ui_Label1, LV_ALIGN_CENTER);
    lv_label_set_text(ui_Label1, "Back");
    lv_obj_set_style_text_color(ui_Label1, lv_color_hex(0x000000), LV_PART_MAIN | LV_STATE_DEFAULT);
    lv_obj_set_style_text_opa(ui_Label1, 255, LV_PART_MAIN | LV_STATE_DEFAULT);

    lv_obj_t * ui_Button14 = lv_btn_create(parent);
    lv_obj_set_width(ui_Button14, 71);
    lv_obj_set_height(ui_Button14, 40);
    lv_obj_set_x(ui_Button14, 70);
    lv_obj_set_y(ui_Button14, 130);
    lv_obj_set_align(ui_Button14, LV_ALIGN_CENTER);
    lv_obj_add_flag(ui_Button14, LV_OBJ_FLAG_SCROLL_ON_FOCUS);     /// Flags
    lv_obj_clear_flag(ui_Button14, LV_OBJ_FLAG_SCROLLABLE);      /// Flags
    lv_obj_set_style_bg_color(ui_Button14, lv_color_hex(0xFFFFFF), LV_PART_MAIN | LV_STATE_DEFAULT);
    lv_obj_set_style_bg_opa(ui_Button14, 255, LV_PART_MAIN | LV_STATE_DEFAULT);
    lv_obj_set_style_border_width(ui_Button14, 2, LV_PART_MAIN | LV_STATE_DEFAULT);
    lv_obj_set_style_shadow_width(ui_Button14, 0, LV_PART_MAIN | LV_STATE_DEFAULT);
    lv_obj_set_style_shadow_spread(ui_Button14, 0, LV_PART_MAIN | LV_STATE_DEFAULT);
    lv_obj_set_style_border_width(ui_Button14, 0, LV_PART_MAIN | LV_STATE_CHECKED | LV_STATE_PRESSED);
    lv_obj_set_style_shadow_width(ui_Button14, 0, LV_PART_MAIN | LV_STATE_CHECKED | LV_STATE_PRESSED);
    lv_obj_set_style_shadow_spread(ui_Button14, 0, LV_PART_MAIN | LV_STATE_CHECKED | LV_STATE_PRESSED);
    lv_obj_set_style_radius(ui_Button14, 10, LV_PART_MAIN | LV_STATE_DEFAULT);

    lv_obj_t * ui_Label15 = lv_label_create(ui_Button14);
    lv_obj_set_width(ui_Label15, LV_SIZE_CONTENT);   /// 1
    lv_obj_set_height(ui_Label15, LV_SIZE_CONTENT);    /// 1
    lv_obj_set_align(ui_Label15, LV_ALIGN_CENTER);
    lv_label_set_text(ui_Label15, "Next");
    lv_obj_set_style_text_color(ui_Label15, lv_color_hex(0x000000), LV_PART_MAIN | LV_STATE_DEFAULT);
    lv_obj_set_style_text_opa(ui_Label15, 255, LV_PART_MAIN | LV_STATE_DEFAULT);

    lv_obj_add_event_cb(ui_Button2, setting_page_switch_cb, LV_EVENT_CLICKED, (void*)'n');
    lv_obj_add_event_cb(ui_Button14, setting_page_switch_cb, LV_EVENT_CLICKED, (void*)'p');

    setting_page = lv_label_create(parent);
    lv_obj_set_width(setting_page, LV_SIZE_CONTENT);   /// 1
    lv_obj_set_height(setting_page, LV_SIZE_CONTENT);    /// 1
    lv_obj_align(setting_page, LV_ALIGN_BOTTOM_MID, 0, -23);
    lv_label_set_text_fmt(setting_page, "%d / %d", setting_curr_page, setting_page_num);
    lv_obj_set_style_text_color(setting_page, lv_color_hex(0x000000), LV_PART_MAIN | LV_STATE_DEFAULT);
    lv_obj_set_style_text_opa(setting_page, 255, LV_PART_MAIN | LV_STATE_DEFAULT);

    scr_back_btn_create(parent, ("Setting"), scr2_btn_event_cb);
}
static void entry2(void) {
    ui_disp_full_refr();
}
static void exit2(void) {
    ui_disp_full_refr();
}
static void destroy2(void) { }

static scr_lifecycle_t screen2 = {
    .create = create2,
    .entry = entry2,
    .exit  = exit2,
    .destroy = destroy2,
};
#endif
//************************************[ screen 3 ]****************************************** GPS
#if 1
#define line_max 23
static lv_obj_t *scr3_cont;
static lv_obj_t *scr3_cnt_lab;
static lv_timer_t *GPS_loop_timer = NULL;

static void gps_set_line(lv_obj_t *label, const char *str1, const char *str2)
{
    int w2 = strlen(str2);
    int w1 = line_max - w2;
    lv_label_set_text_fmt(label, "%-*s%-*s", w1, str1, w2, str2);
}

static lv_obj_t * scr3_create_label(lv_obj_t *parent)
{
    lv_obj_t *label = lv_label_create(parent);
    lv_obj_set_width(label, lv_pct(90));
    lv_obj_set_style_text_font(label, FONT_BOLD_MONO_SIZE_15, LV_PART_MAIN);   
    lv_obj_set_style_border_width(label, 1, LV_PART_MAIN);
    lv_label_set_long_mode(label, LV_LABEL_LONG_WRAP);
    lv_obj_set_style_border_side(label, LV_BORDER_SIDE_BOTTOM, LV_PART_MAIN);
    return label;
}

static void scr3_GPS_updata(void)
{
    double lat      = 0; // Latitude
    double lon      = 0; // Longitude
    double speed    = 0; // Speed over ground
    float alt      = 0; // Altitude
    float accuracy = 0; // Accuracy
    uint32_t   vsat     = 0; // Visible Satellites
    int   usat     = 0; // Used Satellites
    uint16_t   year     = 0; // 
    uint8_t   month    = 0; // 
    uint8_t   day      = 0; // 
    uint8_t   hour     = 0; // 
    uint8_t   min      = 0; // 
    uint8_t   sec      = 0; // 

    static int cnt = 0;

    lv_label_set_text_fmt(scr3_cnt_lab, " %05d ", ++cnt);

    ui_gps_get_coord(&lat, &lon);
    ui_gps_get_data(&year, &month, &day);
    ui_gps_get_time(&hour, &min, &sec);
    ui_gps_get_satellites(&vsat);
    ui_gps_get_speed(&speed);

    char buf[32];

    lv_snprintf(buf, 16, "%0.1f", lat);
    gps_set_line(label_list[0], "Latitude:", buf);

    lv_snprintf(buf, 16, "%0.1f", lon);
    gps_set_line(label_list[1], "Longitude:", buf);

    lv_snprintf(buf, 16, "%0.3fkmph", speed);
    gps_set_line(label_list[2], "Speed:", buf);

    lv_snprintf(buf, 16, "%d", vsat);
    gps_set_line(label_list[3], "vsat:", buf);
    
    lv_snprintf(buf, 16, "%d", year);
    gps_set_line(label_list[4], "year:", buf);

    lv_snprintf(buf, 16, "%d", month);
    gps_set_line(label_list[5], "month:", buf);

    lv_snprintf(buf, 16, "%d", day);
    gps_set_line(label_list[6], "day:", buf);

    lv_snprintf(buf, 16, "%02d:%02d:%02d", hour, min, sec);
    gps_set_line(label_list[7], "time:", buf);
}

static void GPS_loop_timer_event(lv_timer_t * t)
{
    scr3_GPS_updata();
}

static void scr3_btn_event_cb(lv_event_t * e)
{
    if(e->code == LV_EVENT_CLICKED){
        scr_mgr_pop(false);
    }
}

static void create3(lv_obj_t *parent) 
{   
    scr3_cont = lv_obj_create(parent);
    lv_obj_set_size(scr3_cont, lv_pct(100), lv_pct(88));
    lv_obj_set_style_bg_color(scr3_cont, DECKPRO_COLOR_BG, LV_PART_MAIN);
    lv_obj_set_scrollbar_mode(scr3_cont, LV_SCROLLBAR_MODE_OFF);
    lv_obj_clear_flag(scr3_cont, LV_OBJ_FLAG_SCROLLABLE);
    lv_obj_set_style_border_width(scr3_cont, 0, LV_PART_MAIN);
    lv_obj_set_style_pad_all(scr3_cont, 0, LV_PART_MAIN);
    lv_obj_set_style_pad_hor(scr3_cont, 0, LV_PART_MAIN);
    lv_obj_set_style_pad_row(scr3_cont, 5, LV_PART_MAIN);
    lv_obj_set_style_pad_column(scr3_cont, 0, LV_PART_MAIN);
    lv_obj_set_align(scr3_cont, LV_ALIGN_BOTTOM_LEFT);
    lv_obj_set_flex_flow(scr3_cont, LV_FLEX_FLOW_COLUMN);
    lv_obj_set_flex_align(scr3_cont, LV_FLEX_ALIGN_START, LV_FLEX_ALIGN_START, LV_FLEX_ALIGN_CENTER);

    for(int i = 0; i < sizeof(label_list) / sizeof(label_list[0]); i++) {
        label_list[i] = scr3_create_label(scr3_cont);
        lv_label_set_text(label_list[i], " ");
    }

    scr3_cnt_lab = lv_label_create(parent);
    lv_obj_set_style_text_font(scr3_cnt_lab, FONT_BOLD_MONO_SIZE_15, LV_PART_MAIN);
    lv_obj_set_style_radius(scr3_cnt_lab, 5, LV_PART_MAIN);
    lv_obj_set_style_border_width(scr3_cnt_lab, 2, LV_PART_MAIN);
    lv_obj_set_style_text_align(scr3_cnt_lab, LV_TEXT_ALIGN_CENTER, 0);
    lv_label_set_text_fmt(scr3_cnt_lab, " %05d ", 0);
    lv_obj_center(scr3_cnt_lab);
    lv_obj_align(scr3_cnt_lab, LV_ALIGN_TOP_RIGHT, -10, 10);

    lv_obj_t *back3_label = scr_back_btn_create(parent, ("GPS"), scr3_btn_event_cb);
}
static void entry3(void) 
{
    scr3_GPS_updata();

    ui_gps_task_resume();

    GPS_loop_timer = lv_timer_create(GPS_loop_timer_event, 3000, NULL);
    ui_disp_full_refr();
}
static void exit3(void) {
    ui_gps_task_suspend();
    if(GPS_loop_timer) {
        lv_timer_del(GPS_loop_timer);
        GPS_loop_timer = NULL;
    }
    ui_disp_full_refr();
}
static void destroy3(void) { }

static scr_lifecycle_t screen3 = {
    .create = create3,
    .entry = entry3,
    .exit  = exit3,
    .destroy = destroy3,
};

#undef line_max

#endif
//************************************[ screen 4 ]****************************************** Wifi Scan
// --------------------- screen 4 --------------------- WIFI
#if 1
lv_obj_t * scr4_list;
static lv_obj_t *scr4_lab_buf[20];

static void scr4_list_event(lv_event_t *e)
{
    lv_event_code_t code = lv_event_get_code(e);
    lv_obj_t * obj = lv_event_get_target(e);
    for(int i = 0; i < lv_obj_get_child_cnt(obj); i++) 
    {
        lv_obj_t * child = lv_obj_get_child(obj, i);
        if(lv_obj_check_type(child, &lv_label_class)) {
            char *str = lv_label_get_text(child);

            if(strcmp("- WIFI Config", str) == 0)
            {
                scr_mgr_push(SCREEN4_1_ID, false);
            }
            if(strcmp("- WIFI Scan", str) == 0)
            {
                scr_mgr_push(SCREEN4_2_ID, false);
            }
            printf("%s\n", str);
        }
    }
}

static void scr4_item_create(const char *name, lv_event_cb_t cb)
{
    lv_obj_t * obj = lv_obj_class_create_obj(&lv_list_btn_class, scr4_list);
    lv_obj_class_init_obj(obj);
    lv_obj_set_size(obj, LV_PCT(100), LV_SIZE_CONTENT);

    lv_obj_t *label = lv_label_create(obj);
    lv_label_set_text(label, name);
    lv_label_set_long_mode(label, LV_LABEL_LONG_SCROLL_CIRCULAR);
    lv_obj_align(label, LV_ALIGN_LEFT_MID, 10, 0);

    lv_obj_set_height(obj, LV_VER_RES / 6);
    lv_obj_set_style_text_font(obj, FONT_BOLD_SIZE_15, LV_PART_MAIN);
    // lv_obj_set_style_bg_color(obj, lv_color_hex(EPD_COLOR_BG), LV_PART_MAIN);
    // lv_obj_set_style_text_color(obj, lv_color_hex(EPD_COLOR_FG), LV_PART_MAIN);
    lv_obj_set_style_border_width(obj, 1, LV_PART_MAIN | LV_STATE_DEFAULT);
    lv_obj_set_style_border_width(obj, 1, LV_PART_MAIN | LV_STATE_PRESSED);
    lv_obj_set_style_outline_width(obj, 1, LV_PART_MAIN | LV_STATE_PRESSED);
    lv_obj_set_style_radius(obj, 10, LV_PART_MAIN | LV_STATE_DEFAULT);

    lv_obj_add_event_cb(obj, cb, LV_EVENT_CLICKED, NULL); 
}

static void scr4_btn_event_cb(lv_event_t * e)
{
    if(e->code == LV_EVENT_CLICKED){
        // ui_full_refresh();
        scr_mgr_pop(false);
    }
}

static void create4(lv_obj_t *parent) 
{
    scr4_list = lv_list_create(parent);
    lv_obj_set_size(scr4_list, lv_pct(93), lv_pct(91));
    lv_obj_align(scr4_list, LV_ALIGN_BOTTOM_MID, 0, 0);
    // lv_obj_set_style_bg_color(scr4_list, lv_color_hex(EPD_COLOR_BG), LV_PART_MAIN);
    lv_obj_set_style_pad_top(scr4_list, 10, LV_PART_MAIN);
    lv_obj_set_style_pad_row(scr4_list, 15, LV_PART_MAIN);
    lv_obj_set_style_radius(scr4_list, 0, LV_PART_MAIN);
    // lv_obj_set_style_outline_pad(scr4_list, 1, LV_PART_MAIN);
    lv_obj_set_style_border_width(scr4_list, 0, LV_PART_MAIN);
    // lv_obj_set_style_border_color(scr4_list, lv_color_hex(EPD_COLOR_FG), LV_PART_MAIN);
    lv_obj_set_style_shadow_width(scr4_list, 0, LV_PART_MAIN);

    scr4_item_create("- WIFI Config", scr4_list_event);
    scr4_item_create("- WIFI Scan", scr4_list_event);

    // back
    scr_back_btn_create(parent, "WIFI", scr4_btn_event_cb);
}

static void entry4(void) 
{
    ui_disp_full_refr();
}
static void exit4(void) {
    ui_disp_full_refr();
}
static void destroy4(void) { }

static scr_lifecycle_t screen4 = {
    .create = create4,
    .entry = entry4,
    .exit  = exit4,
    .destroy = destroy4,
};
#endif
// --------------------- screen 4.2 --------------------- Wifi Config
#if 1
static void scr4_1_btn_event_cb(lv_event_t * e)
{
    if(e->code == LV_EVENT_CLICKED){
        scr_mgr_pop(false);
    }
}

static void create4_1(lv_obj_t *parent) 
{


    // back
    scr_back_btn_create(parent, "Wifi Config", scr4_1_btn_event_cb);
}

static void entry4_1(void) 
{
    ui_disp_full_refr();
}
static void exit4_1(void) {
    ui_disp_full_refr();
}
static void destroy4_1(void) { }

static scr_lifecycle_t screen4_1 = {
    .create = create4_1,
    .entry = entry4_1,
    .exit  = exit4_1,
    .destroy = destroy4_1,
};
#endif
// --------------------- screen 4.2 --------------------- Wifi Scan
#if 1
static lv_obj_t *scr4_2_cont;
static lv_obj_t *wifi_scan_lab;
static lv_timer_t *wifi_scan_timer = NULL;

static ui_wifi_scan_info_t wifi_info_list[UI_WIFI_SCAN_ITEM_MAX];
static lv_obj_t *wifi_list = NULL;
static char wifi_selected_ssid[UI_WIFI_SSID_MAX_LEN];
static char wifi_password_input_buf[64];
static lv_obj_t *wifi_ssid_title_lab = NULL;
static lv_obj_t *wifi_password_ta = NULL;
static lv_timer_t *wifi_connect_timer = NULL;
static lv_obj_t *wifi_connect_status_lab = NULL;
static lv_obj_t *wifi_password_hint_lab = NULL;
static bool wifi_connect_in_progress = false;
static lv_timer_t *wifi_keypad_timer = NULL;
#define WIFI_KEYPAD_ROWS 4
#define WIFI_KEYPAD_COLS 10
#define WIFI_PASSWORD_LONG_PRESS_MS 650UL
#define WIFI_CONNECT_TIMEOUT_MS 15000UL
#define WIFI_PASSWORD_REFRESH_MS 250UL
#define WIFI_PASSWORD_HINT_TEXT "ALT abc/ABC  Hold UP=chars\nENT=OK  DEL=erase/clear  SYM=show/back"

static const char wifi_password_raw_map[WIFI_KEYPAD_ROWS][WIFI_KEYPAD_COLS] = {
    {'q', 'w', 'e', 'r', 't', 'y', 'u', 'i', 'o', 'p'},
    {'a', 's', 'd', 'f', 'g', 'h', 'j', 'k', 'l', KEYPAD_KEY_DEL},
    {KEYPAD_KEY_ALT, 'z', 'x', 'c', 'v', 'b', 'n', 'm', '$', KEYPAD_KEY_ENT},
    {KEYPAD_KEY_NONE, KEYPAD_KEY_NONE, KEYPAD_KEY_NONE, KEYPAD_KEY_NONE, KEYPAD_KEY_NONE, KEYPAD_KEY_UP, '0', KEYPAD_KEY_SPACE, KEYPAD_KEY_SYM, KEYPAD_KEY_UP},
};

static const char wifi_password_lowercase_map[WIFI_KEYPAD_ROWS][WIFI_KEYPAD_COLS] = {
    {'q', 'w', 'e', 'r', 't', 'y', 'u', 'i', 'o', 'p'},
    {'a', 's', 'd', 'f', 'g', 'h', 'j', 'k', 'l', KEYPAD_KEY_DEL},
    {KEYPAD_KEY_ALT, 'z', 'x', 'c', 'v', 'b', 'n', 'm', '$', KEYPAD_KEY_ENT},
    {KEYPAD_KEY_NONE, KEYPAD_KEY_NONE, KEYPAD_KEY_NONE, KEYPAD_KEY_NONE, KEYPAD_KEY_NONE, KEYPAD_KEY_UP, KEYPAD_KEY_NONE, KEYPAD_KEY_SPACE, KEYPAD_KEY_SYM, KEYPAD_KEY_UP},
};

static const char wifi_password_uppercase_map[WIFI_KEYPAD_ROWS][WIFI_KEYPAD_COLS] = {
    {'Q', 'W', 'E', 'R', 'T', 'Y', 'U', 'I', 'O', 'P'},
    {'A', 'S', 'D', 'F', 'G', 'H', 'J', 'K', 'L', KEYPAD_KEY_DEL},
    {KEYPAD_KEY_ALT, 'Z', 'X', 'C', 'V', 'B', 'N', 'M', '$', KEYPAD_KEY_ENT},
    {KEYPAD_KEY_NONE, KEYPAD_KEY_NONE, KEYPAD_KEY_NONE, KEYPAD_KEY_NONE, KEYPAD_KEY_NONE, KEYPAD_KEY_UP, KEYPAD_KEY_NONE, KEYPAD_KEY_SPACE, KEYPAD_KEY_SYM, KEYPAD_KEY_UP},
};

static const char wifi_password_chat_map[WIFI_KEYPAD_ROWS][WIFI_KEYPAD_COLS] = {
    {'#', '1', '2', '3', '(', ')', '_', '-', '+', '@'},
    {'*', '4', '5', '6', '/', ':', ';', '\'', '"', KEYPAD_KEY_DEL},
    {KEYPAD_KEY_ALT, '7', '8', '9', '?', '!', ',', '.', KEYPAD_KEY_NONE, KEYPAD_KEY_ENT},
    {KEYPAD_KEY_NONE, KEYPAD_KEY_NONE, KEYPAD_KEY_NONE, KEYPAD_KEY_NONE, KEYPAD_KEY_NONE, KEYPAD_KEY_UP, KEYPAD_KEY_NONE, KEYPAD_KEY_SPACE, KEYPAD_KEY_SYM, KEYPAD_KEY_UP},
};

static bool wifi_password_uppercase = false;
static bool wifi_password_visible = false;
static uint8_t wifi_password_shift_hold_count = 0;
static uint32_t wifi_password_del_press_ms = 0;
static uint32_t wifi_password_sym_press_ms = 0;
static uint32_t wifi_connect_started_ms = 0;
static wl_status_t wifi_last_status = WL_IDLE_STATUS;
static bool wifi_password_del_long_handled = false;
static bool wifi_password_sym_long_handled = false;
static bool wifi_password_status_locked = false;

static void wifi_password_set_status(const char *text, lv_color_t color)
{
    if (wifi_connect_status_lab == NULL) {
        return;
    }

    lv_label_set_text(wifi_connect_status_lab, text);
    lv_obj_set_style_text_color(wifi_connect_status_lab, color, LV_PART_MAIN);
}

static void wifi_password_set_hint_text(const char *text)
{
    if (wifi_password_hint_lab == NULL) {
        return;
    }

    lv_label_set_text(wifi_password_hint_lab, text != NULL ? text : "");
}

static void wifi_password_set_connected_view(bool connected)
{
    if (wifi_ssid_title_lab != NULL) {
        if (connected) {
            lv_obj_add_flag(wifi_ssid_title_lab, LV_OBJ_FLAG_HIDDEN);
        } else {
            lv_obj_clear_flag(wifi_ssid_title_lab, LV_OBJ_FLAG_HIDDEN);
        }
    }

    if (wifi_password_ta != NULL) {
        if (connected) {
            lv_obj_add_flag(wifi_password_ta, LV_OBJ_FLAG_HIDDEN);
        } else {
            lv_obj_clear_flag(wifi_password_ta, LV_OBJ_FLAG_HIDDEN);
        }
    }

    if (wifi_connect_status_lab != NULL) {
        lv_obj_set_width(wifi_connect_status_lab, lv_pct(96));
        lv_obj_set_height(wifi_connect_status_lab, LV_SIZE_CONTENT);
        if (connected) {
            lv_obj_align(wifi_connect_status_lab, LV_ALIGN_CENTER, 0, -8);
            lv_obj_set_style_text_font(wifi_connect_status_lab, FONT_BOLD_SIZE_16, LV_PART_MAIN);
        } else {
            lv_obj_align(wifi_connect_status_lab, LV_ALIGN_TOP_MID, 0, 102);
            lv_obj_set_style_text_font(wifi_connect_status_lab, FONT_BOLD_SIZE_14, LV_PART_MAIN);
        }
    }

    if (connected) {
        wifi_password_set_hint_text("Long SYM = Back");
    } else {
        wifi_password_set_hint_text(WIFI_PASSWORD_HINT_TEXT);
    }
}

static void wifi_password_lock_status(bool locked)
{
    wifi_password_status_locked = locked;
}

static void wifi_password_request_refresh(uint32_t duration_ms = WIFI_PASSWORD_REFRESH_MS, bool full_refresh = false)
{
    if (full_refresh) {
        ui_disp_full_refr();
        return;
    }

    ui_disp_partial_refr_for(duration_ms);
}

static void wifi_password_show_connected_info(void)
{
    String ip_text = WiFi.localIP().toString();
    long rssi = WiFi.RSSI();
    char info[160] = {0};
    lv_snprintf(info, sizeof(info),
                "WiFi: %s\nIP: %s\nRSSI: %ld dBm",
                WiFi.SSID().c_str(),
                ip_text.c_str(),
                rssi);
    wifi_password_set_connected_view(true);
    wifi_password_set_status(info, DECKPRO_COLOR_FG);
}

static void wifi_password_apply_visibility(void)
{
    if (wifi_password_ta == NULL) {
        return;
    }

    lv_textarea_set_password_mode(wifi_password_ta, !wifi_password_visible);
}

static void wifi_password_reset_state(void)
{
    wifi_password_uppercase = false;
    wifi_password_visible = false;
    wifi_password_shift_hold_count = 0;
    wifi_password_del_press_ms = 0;
    wifi_password_sym_press_ms = 0;
    wifi_connect_started_ms = 0;
    wifi_last_status = WL_IDLE_STATUS;
    wifi_password_del_long_handled = false;
    wifi_password_sym_long_handled = false;
    wifi_password_status_locked = false;
}

static void wifi_password_refresh_status_hint(void)
{
    wifi_password_set_connected_view(false);

    if (wifi_connect_status_lab == NULL || wifi_connect_in_progress || wifi_password_status_locked) {
        return;
    }

    const char *mode = wifi_password_shift_hold_count > 0 ? "chars" :
                       (wifi_password_uppercase ? "ABC" : "abc");
    const char *visibility = wifi_password_visible ? "show" : "hide";
    char status[96] = {0};
    lv_snprintf(status, sizeof(status), "SSID: %.20s  %s  %s", wifi_selected_ssid, mode, visibility);
    wifi_password_set_status(status, DECKPRO_COLOR_FG);
}

static const char (*wifi_password_active_map(void))[WIFI_KEYPAD_COLS]
{
    if (wifi_password_shift_hold_count > 0) {
        return wifi_password_chat_map;
    }
    return wifi_password_uppercase ? wifi_password_uppercase_map : wifi_password_lowercase_map;
}

static char wifi_password_map_key(char key)
{
    const char (*active_map)[WIFI_KEYPAD_COLS] = wifi_password_active_map();

    for (int row = 0; row < WIFI_KEYPAD_ROWS; ++row) {
        for (int col = 0; col < WIFI_KEYPAD_COLS; ++col) {
            if (wifi_password_raw_map[row][col] == key) {
                return active_map[row][col];
            }
        }
    }

    return KEYPAD_KEY_NONE;
}

static void wifi_password_clear_text(void)
{
    if (wifi_password_ta == NULL) {
        return;
    }

    lv_textarea_set_text(wifi_password_ta, "");
    wifi_password_lock_status(false);
    wifi_password_request_refresh();
}

static void wifi_password_toggle_visibility(void)
{
    wifi_password_visible = !wifi_password_visible;
    wifi_password_apply_visibility();
    wifi_password_lock_status(false);
    wifi_password_request_refresh();
}

static void wifi_password_cancel(void)
{
    wifi_connect_in_progress = false;
    memset(wifi_selected_ssid, 0, sizeof(wifi_selected_ssid));
    memset(wifi_password_input_buf, 0, sizeof(wifi_password_input_buf));
    wifi_password_reset_state();
    wifi_password_set_connected_view(false);
    scr_mgr_pop(false);
}

static void scr4_2_btn_event_cb(lv_event_t * e)
{
    if(e->code == LV_EVENT_CLICKED){
        scr_mgr_pop(false);
    }
}

static void wifi_list_event(lv_event_t *e)
{
    lv_event_code_t code = lv_event_get_code(e);
    if (code != LV_EVENT_CLICKED) return;

    lv_obj_t *obj = lv_event_get_target(e);
    int idx = (int)(uintptr_t)lv_obj_get_user_data(obj);
    if (idx < 0 || idx >= UI_WIFI_SCAN_ITEM_MAX) return;
    if (strcmp(wifi_info_list[idx].name, "") == 0) return;

    memset(wifi_selected_ssid, 0, sizeof(wifi_selected_ssid));
    strncpy(wifi_selected_ssid, wifi_info_list[idx].name, sizeof(wifi_selected_ssid) - 1);

    scr_mgr_push(SCREEN4_3_ID, false);
}

static void show_wifi_scan(void)
{
    if (wifi_list) {
        lv_obj_del(wifi_list);
        wifi_list = NULL;
    }

    wifi_list = lv_list_create(scr4_2_cont);
    lv_obj_set_size(wifi_list, lv_pct(95), lv_pct(70));
    lv_obj_set_style_pad_top(wifi_list, 5, LV_PART_MAIN);
    lv_obj_set_style_pad_row(wifi_list, 5, LV_PART_MAIN);
    lv_obj_set_style_radius(wifi_list, 0, LV_PART_MAIN);
    lv_obj_set_style_border_width(wifi_list, 0, LV_PART_MAIN);
    lv_obj_set_style_shadow_width(wifi_list, 0, LV_PART_MAIN);

    for (int i = 0; i < UI_WIFI_SCAN_ITEM_MAX; i++) {
        if (strcmp(wifi_info_list[i].name, "") == 0 && wifi_info_list[i].rssi == 0) {
            break;
        }

        char item_text[24];
        lv_snprintf(item_text, sizeof(item_text), "%-16.16s %4d",
                    wifi_info_list[i].name, wifi_info_list[i].rssi);

        lv_obj_t *btn = lv_list_add_btn(wifi_list, NULL, item_text);
        lv_obj_set_height(btn, 28);
        lv_obj_set_style_text_font(btn, FONT_BOLD_MONO_SIZE_14, LV_PART_MAIN);
        lv_obj_set_user_data(btn, (void *)(uintptr_t)i);
        lv_obj_add_event_cb(btn, wifi_list_event, LV_EVENT_CLICKED, NULL);
    }
}

static void create4_2(lv_obj_t *parent)
{
    scr4_2_cont = lv_obj_create(parent);
    lv_obj_set_size(scr4_2_cont, lv_pct(100), lv_pct(90));
    lv_obj_set_style_bg_color(scr4_2_cont, DECKPRO_COLOR_BG, LV_PART_MAIN);
    lv_obj_set_scrollbar_mode(scr4_2_cont, LV_SCROLLBAR_MODE_OFF);
    lv_obj_clear_flag(scr4_2_cont, LV_OBJ_FLAG_SCROLLABLE);
    lv_obj_set_style_border_width(scr4_2_cont, 0, LV_PART_MAIN);
    lv_obj_set_style_pad_all(scr4_2_cont, 0, LV_PART_MAIN);
    lv_obj_set_style_pad_left(scr4_2_cont, 13, LV_PART_MAIN);
    lv_obj_set_flex_flow(scr4_2_cont, LV_FLEX_FLOW_COLUMN);
    lv_obj_set_style_pad_row(scr4_2_cont, 5, LV_PART_MAIN);
    lv_obj_set_style_pad_column(scr4_2_cont, 5, LV_PART_MAIN);
    lv_obj_set_align(scr4_2_cont, LV_ALIGN_BOTTOM_MID);

    wifi_scan_lab = lv_label_create(scr4_2_cont);
    lv_obj_set_width(wifi_scan_lab, lv_pct(95));
    lv_obj_set_style_pad_all(wifi_scan_lab, 0, LV_PART_MAIN);
    lv_obj_set_style_text_font(wifi_scan_lab, FONT_BOLD_MONO_SIZE_15, LV_PART_MAIN);
    lv_obj_set_style_border_width(wifi_scan_lab, 0, LV_PART_MAIN);
    lv_label_set_long_mode(wifi_scan_lab, LV_LABEL_LONG_WRAP);
    lv_label_set_text(wifi_scan_lab, "Press Scan to search WiFi");

    lv_obj_t *scan_btn = lv_btn_create(scr4_2_cont);
    lv_obj_set_height(scan_btn, 36);
    lv_obj_set_style_bg_color(scan_btn, DECKPRO_COLOR_FG, LV_PART_MAIN);
    lv_obj_set_style_text_color(scan_btn, DECKPRO_COLOR_BG, LV_PART_MAIN);
    lv_obj_t *scan_btn_lab = lv_label_create(scan_btn);
    lv_label_set_text(scan_btn_lab, "Scan");
    lv_obj_center(scan_btn_lab);
    lv_obj_add_event_cb(scan_btn, [](lv_event_t *e) {
        if (e->code == LV_EVENT_CLICKED) {
            ui_wifi_get_scan_info(wifi_info_list, UI_WIFI_SCAN_ITEM_MAX);
            show_wifi_scan();
        }
    }, LV_EVENT_CLICKED, NULL);

    lv_obj_t *back4_label = scr_back_btn_create(parent, ("Wifi"), scr4_2_btn_event_cb);
}
static void entry4_2(void)
{
    ui_disp_full_refr();
}
static void exit4_2(void) {
    ui_disp_full_refr();
    if (wifi_list) {
        lv_obj_del(wifi_list);
        wifi_list = NULL;
    }
}

static void destroy4_2(void) { }

static scr_lifecycle_t screen4_2 = {
    .create = create4_2,
    .entry = entry4_2,
    .exit  = exit4_2,
    .destroy = destroy4_2,
};
#endif

// --------------------- screen 4.3 --------------------- WiFi Password Input
#if 1
static void wifi_connect_timer_cb(lv_timer_t *t)
{
    (void)t;
    wl_status_t status = ui_wifi_get_status();
    uint32_t elapsed_ms = wifi_connect_started_ms > 0 ? (millis() - wifi_connect_started_ms) : 0;

    if (status != wifi_last_status) {
        Serial.printf("[WiFi UI] status=%d elapsed=%lu ssid=%s\n",
                      (int)status,
                      (unsigned long)elapsed_ms,
                      wifi_selected_ssid);
        wifi_last_status = status;
    }

    if (status == WL_CONNECTED) {
        lv_timer_pause(wifi_connect_timer);
        wifi_connect_in_progress = false;
        wifi_connect_started_ms = 0;
        wifi_password_lock_status(true);
        wifi_password_show_connected_info();
        wifi_password_request_refresh(0, true);
    } else if (status == WL_CONNECT_FAILED || status == WL_NO_SSID_AVAIL) {
        lv_timer_pause(wifi_connect_timer);
        wifi_connect_in_progress = false;
        wifi_connect_started_ms = 0;
        wifi_password_lock_status(true);
        wifi_password_set_status("Connection failed", DECKPRO_COLOR_FG);
        wifi_password_request_refresh(0, true);
    } else if ((status == WL_CONNECTION_LOST || status == WL_DISCONNECTED) &&
               elapsed_ms >= 5000UL) {
        lv_timer_pause(wifi_connect_timer);
        wifi_connect_in_progress = false;
        wifi_connect_started_ms = 0;
        wifi_password_lock_status(true);
        wifi_password_set_status("Disconnected\nCheck SSID / password", DECKPRO_COLOR_FG);
        wifi_password_request_refresh(0, true);
    } else if (wifi_connect_started_ms > 0 &&
               elapsed_ms >= WIFI_CONNECT_TIMEOUT_MS) {
        lv_timer_pause(wifi_connect_timer);
        wifi_connect_in_progress = false;
        wifi_connect_started_ms = 0;
        wifi_password_lock_status(true);
        wifi_password_set_status("Connection timeout", DECKPRO_COLOR_FG);
        wifi_password_request_refresh(0, true);
    }
}

static void wifi_password_submit(void)
{
    if (wifi_connect_in_progress) {
        return;
    }

    const char *password = lv_textarea_get_text(wifi_password_ta);
    if (password == NULL || strlen(password) == 0) {
        wifi_password_lock_status(true);
        wifi_password_set_status("Password cannot be empty", DECKPRO_COLOR_FG);
        wifi_password_request_refresh(0, true);
        return;
    }

    if (!ui_wifi_connect(wifi_selected_ssid, password)) {
        wifi_password_lock_status(true);
        wifi_password_set_status("Unable to start WiFi", DECKPRO_COLOR_FG);
        wifi_password_request_refresh(0, true);
        return;
    }

    wifi_connect_in_progress = true;
    wifi_connect_started_ms = millis();
    wifi_last_status = WL_IDLE_STATUS;
    wifi_password_lock_status(true);
    wifi_password_set_status("Connecting...", DECKPRO_COLOR_FG);
    if (wifi_connect_timer == NULL) {
        wifi_connect_timer = lv_timer_create(wifi_connect_timer_cb, 500, NULL);
    }
    lv_timer_reset(wifi_connect_timer);
    lv_timer_resume(wifi_connect_timer);
    wifi_password_request_refresh(0, true);
}

static bool wifi_password_handle_long_press_actions(void)
{
    if (wifi_password_del_press_ms > 0 &&
        !wifi_password_del_long_handled &&
        millis() - wifi_password_del_press_ms >= WIFI_PASSWORD_LONG_PRESS_MS) {
        wifi_password_clear_text();
        wifi_password_del_long_handled = true;
    }

    if (wifi_password_sym_press_ms > 0 &&
        !wifi_password_sym_long_handled &&
        millis() - wifi_password_sym_press_ms >= WIFI_PASSWORD_LONG_PRESS_MS) {
        wifi_password_sym_long_handled = true;
        wifi_password_cancel();
        return true;
    }

    return false;
}

static bool wifi_password_process_event(char key, int state)
{
    if (key == KEYPAD_KEY_NONE) {
        return false;
    }

    switch (key) {
    case KEYPAD_KEY_UP:
        if (state == KEYPAD_PRESS) {
            ++wifi_password_shift_hold_count;
        } else if (wifi_password_shift_hold_count > 0) {
            --wifi_password_shift_hold_count;
        }
        wifi_password_lock_status(false);
        wifi_password_refresh_status_hint();
        return false;
    case KEYPAD_KEY_ALT:
        if (state == KEYPAD_PRESS) {
            wifi_password_uppercase = !wifi_password_uppercase;
            wifi_password_lock_status(false);
            wifi_password_refresh_status_hint();
            wifi_password_request_refresh();
        }
        return false;
    case KEYPAD_KEY_DEL:
        if (state == KEYPAD_PRESS) {
            wifi_password_del_press_ms = millis();
            wifi_password_del_long_handled = false;
        } else {
            if (!wifi_password_del_long_handled && wifi_password_ta != NULL) {
                lv_textarea_del_char(wifi_password_ta);
            }
            wifi_password_del_press_ms = 0;
            wifi_password_del_long_handled = false;
            wifi_password_lock_status(false);
            wifi_password_refresh_status_hint();
            wifi_password_request_refresh();
        }
        return false;
    case KEYPAD_KEY_SYM:
        if (state == KEYPAD_PRESS) {
            wifi_password_sym_press_ms = millis();
            wifi_password_sym_long_handled = false;
        } else {
            if (!wifi_password_sym_long_handled) {
                wifi_password_toggle_visibility();
            }
            wifi_password_sym_press_ms = 0;
            wifi_password_sym_long_handled = false;
            wifi_password_lock_status(false);
            wifi_password_refresh_status_hint();
            wifi_password_request_refresh();
        }
        return false;
    case KEYPAD_KEY_ENT:
        if (state == KEYPAD_PRESS) {
            wifi_password_submit();
        }
        return false;
    default:
        if (state != KEYPAD_PRESS) {
            return false;
        }

        char mapped = wifi_password_map_key(key);
        if (mapped != KEYPAD_KEY_NONE) {
            char txt[2] = {mapped, '\0'};
            wifi_password_lock_status(false);
            wifi_password_request_refresh();
            lv_textarea_add_text(wifi_password_ta, txt);
            wifi_password_refresh_status_hint();
        }
        return false;
    }
}

static void wifi_password_keypad_handler(void)
{
    if (wifi_password_ta == NULL) {
        return;
    }

    char key = KEYPAD_KEY_NONE;
    int state = KEYPAD_RELEASE;
    while (ui_input_get_keypay_event(&key, &state)) {
        if (wifi_password_process_event(key, state)) {
            return;
        }
    }

    if (wifi_password_handle_long_press_actions()) {
        return;
    }
}

static void create4_3(lv_obj_t *parent)
{
    wifi_ssid_title_lab = lv_label_create(parent);
    lv_obj_set_width(wifi_ssid_title_lab, lv_pct(95));
    lv_obj_align(wifi_ssid_title_lab, LV_ALIGN_TOP_MID, 0, 10);
    lv_obj_set_style_text_font(wifi_ssid_title_lab, FONT_BOLD_SIZE_16, LV_PART_MAIN);
    lv_obj_set_style_text_align(wifi_ssid_title_lab, LV_TEXT_ALIGN_CENTER, LV_PART_MAIN);
    char ssid_title[40];
    lv_snprintf(ssid_title, sizeof(ssid_title), "SSID: %s", wifi_selected_ssid);
    lv_label_set_text(wifi_ssid_title_lab, ssid_title);

    wifi_password_ta = lv_textarea_create(parent);
    lv_textarea_set_password_mode(wifi_password_ta, true);
    lv_textarea_set_one_line(wifi_password_ta, true);
    lv_obj_set_size(wifi_password_ta, 224, 42);
    lv_obj_align(wifi_password_ta, LV_ALIGN_TOP_MID, 0, 48);
    lv_obj_clear_flag(wifi_password_ta, LV_OBJ_FLAG_CLICKABLE);
    lv_obj_set_style_text_font(wifi_password_ta, &Font_Mono_Bold_20, LV_PART_MAIN);
    lv_obj_set_style_text_align(wifi_password_ta, LV_TEXT_ALIGN_CENTER, LV_PART_MAIN);
    lv_obj_set_style_pad_top(wifi_password_ta, 7, LV_PART_MAIN);
    lv_textarea_set_placeholder_text(wifi_password_ta, "Password");
    lv_textarea_set_max_length(wifi_password_ta, 63);

    wifi_connect_status_lab = lv_label_create(parent);
    lv_obj_set_width(wifi_connect_status_lab, lv_pct(96));
    lv_obj_align(wifi_connect_status_lab, LV_ALIGN_TOP_MID, 0, 102);
    lv_obj_set_style_text_align(wifi_connect_status_lab, LV_TEXT_ALIGN_CENTER, LV_PART_MAIN);
    lv_obj_set_style_text_font(wifi_connect_status_lab, FONT_BOLD_SIZE_14, LV_PART_MAIN);
    lv_label_set_long_mode(wifi_connect_status_lab, LV_LABEL_LONG_WRAP);
    lv_label_set_text(wifi_connect_status_lab, "");

    wifi_password_hint_lab = lv_label_create(parent);
    lv_obj_set_width(wifi_password_hint_lab, lv_pct(96));
    lv_obj_align(wifi_password_hint_lab, LV_ALIGN_BOTTOM_MID, 0, -18);
    lv_obj_set_style_text_align(wifi_password_hint_lab, LV_TEXT_ALIGN_CENTER, LV_PART_MAIN);
    lv_obj_set_style_text_font(wifi_password_hint_lab, FONT_BOLD_MONO_SIZE_14, LV_PART_MAIN);
    lv_label_set_long_mode(wifi_password_hint_lab, LV_LABEL_LONG_WRAP);
    lv_label_set_text(wifi_password_hint_lab, WIFI_PASSWORD_HINT_TEXT);
}

static void entry4_3(void)
{
    wifi_password_reset_state();
    wifi_connect_in_progress = false;
    wifi_password_set_connected_view(false);
    wifi_password_apply_visibility();
    wifi_keypad_timer = lv_timer_create([](lv_timer_t *t) {
        (void)t;
        wifi_password_keypad_handler();
    }, 20, NULL);

    wifi_connect_timer = lv_timer_create(wifi_connect_timer_cb, 500, NULL);
    lv_timer_pause(wifi_connect_timer);
    wifi_password_refresh_status_hint();

    ui_disp_full_refr();
}

static void exit4_3(void)
{
    wifi_connect_in_progress = false;
    wifi_password_reset_state();
    if (wifi_keypad_timer) {
        lv_timer_del(wifi_keypad_timer);
        wifi_keypad_timer = NULL;
    }
    if (wifi_connect_timer) {
        lv_timer_del(wifi_connect_timer);
        wifi_connect_timer = NULL;
    }
    ui_disp_full_refr();
}

static void destroy4_3(void)
{
    wifi_password_reset_state();
    wifi_ssid_title_lab = NULL;
    wifi_password_ta = NULL;
    wifi_connect_status_lab = NULL;
    wifi_password_hint_lab = NULL;
}

static scr_lifecycle_t screen4_3 = {
    .create = create4_3,
    .entry = entry4_3,
    .exit  = exit4_3,
    .destroy = destroy4_3,
};
#endif
//************************************[ screen 5 ]****************************************** Test
#if 1
static lv_obj_t *test_list;
static lv_obj_t *test_page;
static int test_num = 0;
static int test_page_num = 0;
static int test_curr_page = 0;

static ui_test_handle test_handle_list[] = {
    { .name="Lora",       .peri_id=E_PERI_LORA       , .cb=ui_test_get },
    { .name="Touch",      .peri_id=E_PERI_TOUCH      , .cb=ui_test_get },
    { .name="SY6970",    .peri_id=E_PERI_BQ25896    , .cb=ui_test_get },
    { .name="BQ27220",    .peri_id=E_PERI_BQ27220    , .cb=ui_test_get },
    { .name="SD Card",    .peri_id=E_PERI_SD         , .cb=ui_test_get },
    { .name="A7682E",     .peri_id=E_PERI_A7682E     , .cb=ui_test_get },
    { .name="ES8311",     .peri_id=E_PERI_ES8311     , .cb=ui_test_get },
    { .name="Keypad",     .peri_id=E_PERI_KYEPAD     , .cb=ui_test_get },
    { .name="GPS",        .peri_id=E_PERI_GPS        , .cb=ui_test_get },
    { .name="BHI260AP",   .peri_id=E_PERI_BHI260AP   , .cb=ui_test_get },
    { .name="INK_SCREEN", .peri_id=E_PERI_INK_SCREEN , .cb=ui_test_get },
};

static void test_item_create(int curr_apge);

static void scr5_btn_event_cb(lv_event_t * e)
{
    if(e->code == LV_EVENT_CLICKED){
        scr_mgr_pop(false);
    }
}

static void test_page_switch_cb(lv_event_t *e)
{
    char opt = (int)e->user_data;
    
    if(test_num < SETTING_PAGE_MAX_ITEM) return;

    int child_cnt = lv_obj_get_child_cnt(test_list);
    
    for(int i = 0; i < child_cnt; i++)
    {
        lv_obj_t *child = lv_obj_get_child(test_list, 0);
        if(child)
            lv_obj_del(child);
    }

    if(opt == 'p')
    {
        test_curr_page = (test_curr_page < test_page_num) ? test_curr_page + 1 : 0;
    }
    else if(opt == 'n')
    {
        test_curr_page = (test_curr_page > 0) ? test_curr_page - 1 : test_page_num;
    }

    test_item_create(test_curr_page);
    lv_label_set_text_fmt(test_page, "%d / %d", test_curr_page, test_page_num);
}

static void test_item_create(int curr_apge)
{
    printf("test_curr_page = %d\n", test_curr_page);
    int start = (curr_apge * SETTING_PAGE_MAX_ITEM);
    int end = start + SETTING_PAGE_MAX_ITEM;
    if(end > test_num) end = test_num;

    printf("start=%d, end=%d\n", start, end);

    for(int i = start; i < end; i++) {
        ui_test_handle *h = &test_handle_list[i];
        h->obj = lv_list_add_btn(test_list, NULL, h->name);
        h->st = lv_label_create(h->obj);
        lv_obj_set_style_text_font(h->st, FONT_BOLD_SIZE_15, LV_PART_MAIN);
        lv_obj_align(h->st, LV_ALIGN_RIGHT_MID, 0, 0);
        lv_label_set_text_fmt(h->st, "%s", (h->cb(h->peri_id) ? "PASS" : "----"));
        // style
        lv_obj_set_style_text_font(h->obj, FONT_BOLD_SIZE_15, LV_PART_MAIN);
        lv_obj_set_style_bg_color(h->obj, DECKPRO_COLOR_BG, LV_PART_MAIN);
        lv_obj_set_style_text_color(h->obj, DECKPRO_COLOR_FG, LV_PART_MAIN);
        lv_obj_set_style_border_width(h->obj, 1, LV_PART_MAIN | LV_STATE_DEFAULT);
        lv_obj_set_style_border_width(h->obj, 1, LV_PART_MAIN | LV_STATE_PRESSED);
        lv_obj_set_style_outline_width(h->obj, 3, LV_PART_MAIN | LV_STATE_PRESSED);
        lv_obj_set_style_radius(h->obj, 5, LV_PART_MAIN | LV_STATE_DEFAULT);
        // lv_obj_add_event_cb(h->obj, test_scr_event, LV_EVENT_CLICKED, (void *)h);
    }
}

static void create5(lv_obj_t *parent) 
{
    test_list = lv_list_create(parent);
    lv_obj_set_size(test_list, LV_HOR_RES, lv_pct(88));
    lv_obj_align(test_list, LV_ALIGN_BOTTOM_MID, 0, 0);
    lv_obj_set_style_bg_color(test_list, DECKPRO_COLOR_BG, LV_PART_MAIN);
    lv_obj_set_style_pad_top(test_list, 2, LV_PART_MAIN);
    lv_obj_set_style_pad_row(test_list, 3, LV_PART_MAIN);
    lv_obj_set_style_radius(test_list, 0, LV_PART_MAIN);
    // lv_obj_set_style_outline_pad(test_list, 2, LV_PART_MAIN);
    lv_obj_set_style_border_width(test_list, 0, LV_PART_MAIN);
    lv_obj_set_style_border_color(test_list, DECKPRO_COLOR_FG, LV_PART_MAIN);
    lv_obj_set_style_shadow_width(test_list, 0, LV_PART_MAIN);

    test_num = sizeof(test_handle_list) / sizeof(test_handle_list[0]);
    test_page_num = test_num / SETTING_PAGE_MAX_ITEM;
    test_item_create(test_curr_page);

    lv_obj_t * ui_Button2 = lv_btn_create(parent);
    lv_obj_set_width(ui_Button2, 71);
    lv_obj_set_height(ui_Button2, 40);
    lv_obj_set_x(ui_Button2, -70);
    lv_obj_set_y(ui_Button2, 130);
    lv_obj_set_align(ui_Button2, LV_ALIGN_CENTER);
    lv_obj_add_flag(ui_Button2, LV_OBJ_FLAG_SCROLL_ON_FOCUS);     /// Flags
    lv_obj_clear_flag(ui_Button2, LV_OBJ_FLAG_SCROLLABLE);      /// Flags
    lv_obj_set_style_bg_color(ui_Button2, lv_color_hex(0xFFFFFF), LV_PART_MAIN | LV_STATE_DEFAULT);
    lv_obj_set_style_bg_opa(ui_Button2, 255, LV_PART_MAIN | LV_STATE_DEFAULT);
    lv_obj_set_style_border_width(ui_Button2, 2, LV_PART_MAIN | LV_STATE_DEFAULT);
    lv_obj_set_style_shadow_width(ui_Button2, 0, LV_PART_MAIN | LV_STATE_DEFAULT);
    lv_obj_set_style_shadow_spread(ui_Button2, 0, LV_PART_MAIN | LV_STATE_DEFAULT);
    lv_obj_set_style_border_width(ui_Button2, 0, LV_PART_MAIN | LV_STATE_CHECKED | LV_STATE_PRESSED);
    lv_obj_set_style_shadow_width(ui_Button2, 0, LV_PART_MAIN | LV_STATE_CHECKED | LV_STATE_PRESSED);
    lv_obj_set_style_shadow_spread(ui_Button2, 0, LV_PART_MAIN | LV_STATE_CHECKED | LV_STATE_PRESSED);
    lv_obj_set_style_radius(ui_Button2, 10, LV_PART_MAIN | LV_STATE_DEFAULT);

    lv_obj_t * ui_Label1 = lv_label_create(ui_Button2);
    lv_obj_set_width(ui_Label1, LV_SIZE_CONTENT);   /// 1
    lv_obj_set_height(ui_Label1, LV_SIZE_CONTENT);    /// 1
    lv_obj_set_align(ui_Label1, LV_ALIGN_CENTER);
    lv_label_set_text(ui_Label1, "Back");
    lv_obj_set_style_text_color(ui_Label1, lv_color_hex(0x000000), LV_PART_MAIN | LV_STATE_DEFAULT);
    lv_obj_set_style_text_opa(ui_Label1, 255, LV_PART_MAIN | LV_STATE_DEFAULT);

    lv_obj_t * ui_Button14 = lv_btn_create(parent);
    lv_obj_set_width(ui_Button14, 71);
    lv_obj_set_height(ui_Button14, 40);
    lv_obj_set_x(ui_Button14, 70);
    lv_obj_set_y(ui_Button14, 130);
    lv_obj_set_align(ui_Button14, LV_ALIGN_CENTER);
    lv_obj_add_flag(ui_Button14, LV_OBJ_FLAG_SCROLL_ON_FOCUS);     /// Flags
    lv_obj_clear_flag(ui_Button14, LV_OBJ_FLAG_SCROLLABLE);      /// Flags
    lv_obj_set_style_bg_color(ui_Button14, lv_color_hex(0xFFFFFF), LV_PART_MAIN | LV_STATE_DEFAULT);
    lv_obj_set_style_bg_opa(ui_Button14, 255, LV_PART_MAIN | LV_STATE_DEFAULT);
    lv_obj_set_style_border_width(ui_Button14, 2, LV_PART_MAIN | LV_STATE_DEFAULT);
    lv_obj_set_style_shadow_width(ui_Button14, 0, LV_PART_MAIN | LV_STATE_DEFAULT);
    lv_obj_set_style_shadow_spread(ui_Button14, 0, LV_PART_MAIN | LV_STATE_DEFAULT);
    lv_obj_set_style_border_width(ui_Button14, 0, LV_PART_MAIN | LV_STATE_CHECKED | LV_STATE_PRESSED);
    lv_obj_set_style_shadow_width(ui_Button14, 0, LV_PART_MAIN | LV_STATE_CHECKED | LV_STATE_PRESSED);
    lv_obj_set_style_shadow_spread(ui_Button14, 0, LV_PART_MAIN | LV_STATE_CHECKED | LV_STATE_PRESSED);
    lv_obj_set_style_radius(ui_Button14, 10, LV_PART_MAIN | LV_STATE_DEFAULT);

    lv_obj_t * ui_Label15 = lv_label_create(ui_Button14);
    lv_obj_set_width(ui_Label15, LV_SIZE_CONTENT);   /// 1
    lv_obj_set_height(ui_Label15, LV_SIZE_CONTENT);    /// 1
    lv_obj_set_align(ui_Label15, LV_ALIGN_CENTER);
    lv_label_set_text(ui_Label15, "Next");
    lv_obj_set_style_text_color(ui_Label15, lv_color_hex(0x000000), LV_PART_MAIN | LV_STATE_DEFAULT);
    lv_obj_set_style_text_opa(ui_Label15, 255, LV_PART_MAIN | LV_STATE_DEFAULT);

    lv_obj_add_event_cb(ui_Button2, test_page_switch_cb, LV_EVENT_CLICKED, (void*)'n');
    lv_obj_add_event_cb(ui_Button14, test_page_switch_cb, LV_EVENT_CLICKED, (void*)'p');

    test_page = lv_label_create(parent);
    lv_obj_set_width(test_page, LV_SIZE_CONTENT);   /// 1
    lv_obj_set_height(test_page, LV_SIZE_CONTENT);    /// 1
    lv_obj_align(test_page, LV_ALIGN_BOTTOM_MID, 0, -23);
    lv_label_set_text_fmt(test_page, "%d / %d", test_curr_page, test_page_num);
    lv_obj_set_style_text_color(test_page, lv_color_hex(0x000000), LV_PART_MAIN | LV_STATE_DEFAULT);
    lv_obj_set_style_text_opa(test_page, 255, LV_PART_MAIN | LV_STATE_DEFAULT);

    lv_obj_t *back5_label = scr_back_btn_create(parent, ("Test"), scr5_btn_event_cb);
}
static void entry5(void) 
{
    ui_disp_full_refr();
}
static void exit5(void) {
    ui_disp_full_refr();
}
static void destroy5(void) { }

static scr_lifecycle_t screen5 = {
    .create = create5,
    .entry = entry5,
    .exit  = exit5,
    .destroy = destroy5,
};
#endif
//************************************[ screen 6 ]****************************************** Battery
// --------------------- screen 6 --------------------- Battery
#if 1
lv_obj_t * scr6_list;
static lv_obj_t *scr6_lab_buf[20];

static void scr6_list_event(lv_event_t *e)
{
    lv_event_code_t code = lv_event_get_code(e);
    lv_obj_t * obj = lv_event_get_target(e);
    for(int i = 0; i < lv_obj_get_child_cnt(obj); i++) 
    {
        lv_obj_t * child = lv_obj_get_child(obj, i);
        if(lv_obj_check_type(child, &lv_label_class)) {
            char *str = lv_label_get_text(child);

            if(strcmp("- SY6970", str) == 0)
            {
                scr_mgr_push(SCREEN6_1_ID, false);
            }
            if(strcmp("- BQ27220", str) == 0)
            {
                scr_mgr_push(SCREEN6_2_ID, false);
            }
            printf("%s\n", str);
        }
    }
}

static void scr6_item_create(const char *name, lv_event_cb_t cb)
{
    lv_obj_t * obj = lv_obj_class_create_obj(&lv_list_btn_class, scr6_list);
    lv_obj_class_init_obj(obj);
    lv_obj_set_size(obj, LV_PCT(100), LV_SIZE_CONTENT);

    lv_obj_t *label = lv_label_create(obj);
    lv_label_set_text(label, name);
    lv_label_set_long_mode(label, LV_LABEL_LONG_SCROLL_CIRCULAR);
    lv_obj_align(label, LV_ALIGN_LEFT_MID, 10, 0);

    lv_obj_set_height(obj, LV_VER_RES / 6);
    lv_obj_set_style_text_font(obj, FONT_BOLD_SIZE_15, LV_PART_MAIN);
    // lv_obj_set_style_bg_color(obj, lv_color_hex(EPD_COLOR_BG), LV_PART_MAIN);
    // lv_obj_set_style_text_color(obj, lv_color_hex(EPD_COLOR_FG), LV_PART_MAIN);
    lv_obj_set_style_border_width(obj, 1, LV_PART_MAIN | LV_STATE_DEFAULT);
    lv_obj_set_style_border_width(obj, 1, LV_PART_MAIN | LV_STATE_PRESSED);
    lv_obj_set_style_outline_width(obj, 1, LV_PART_MAIN | LV_STATE_PRESSED);
    lv_obj_set_style_radius(obj, 10, LV_PART_MAIN | LV_STATE_DEFAULT);

    lv_obj_add_event_cb(obj, cb, LV_EVENT_CLICKED, NULL); 
}

static void scr6_btn_event_cb(lv_event_t * e)
{
    if(e->code == LV_EVENT_CLICKED){
        // ui_full_refresh();
        scr_mgr_pop(false);
    }
}

static void create6(lv_obj_t *parent) 
{
    scr6_list = lv_list_create(parent);
    lv_obj_set_size(scr6_list, lv_pct(93), lv_pct(91));
    lv_obj_align(scr6_list, LV_ALIGN_BOTTOM_MID, 0, 0);
    // lv_obj_set_style_bg_color(scr6_list, lv_color_hex(EPD_COLOR_BG), LV_PART_MAIN);
    lv_obj_set_style_pad_top(scr6_list, 10, LV_PART_MAIN);
    lv_obj_set_style_pad_row(scr6_list, 15, LV_PART_MAIN);
    lv_obj_set_style_radius(scr6_list, 0, LV_PART_MAIN);
    // lv_obj_set_style_outline_pad(scr6_list, 1, LV_PART_MAIN);
    lv_obj_set_style_border_width(scr6_list, 0, LV_PART_MAIN);
    // lv_obj_set_style_border_color(scr6_list, lv_color_hex(EPD_COLOR_FG), LV_PART_MAIN);
    lv_obj_set_style_shadow_width(scr6_list, 0, LV_PART_MAIN);

    scr6_item_create("- SY6970", scr6_list_event);
    scr6_item_create("- BQ27220", scr6_list_event);

    // back
    scr_back_btn_create(parent, "Battery", scr6_btn_event_cb);
}

static void entry6(void) 
{
    ui_disp_full_refr();
}
static void exit6(void) {
    ui_disp_full_refr();
}
static void destroy6(void) { }

static scr_lifecycle_t screen6 = {
    .create = create6,
    .entry = entry6,
    .exit  = exit6,
    .destroy = destroy6,
};
#endif
// --------------------- screen 6.1 --------------------- BQ25896
#if 1
#define line_max 23

static lv_timer_t *batt_6_1_timer = NULL;

static void battery_set_line(lv_obj_t *label, const char *str1, const char *str2)
{
    int w2 = strlen(str2);
    int w1 = line_max - w2;
    lv_label_set_text_fmt(label, "%-*s%-*s", w1, str1, w2, str2);
}

static lv_obj_t * scr6_1_create_label(lv_obj_t *parent)
{
    lv_obj_t *label = lv_label_create(parent);
    lv_obj_set_width(label, lv_pct(90));
    lv_obj_set_style_text_font(label, FONT_BOLD_MONO_SIZE_15, LV_PART_MAIN);   
    lv_obj_set_style_border_width(label, 1, LV_PART_MAIN);
    lv_label_set_long_mode(label, LV_LABEL_LONG_WRAP);
    lv_obj_set_style_border_side(label, LV_BORDER_SIDE_BOTTOM, LV_PART_MAIN);
    return label;
}

static void scr6_1_battert_updata(void)
{
    char buf[line_max];

    battery_set_line(label_list[0], "Charging:", (ui_batt_25896_is_chg() == true ? "Charging" : "Not charged"));

    lv_snprintf(buf, line_max, "%.2fV", ui_batt_25896_get_vbus());
    battery_set_line(label_list[1], "VBUS:", buf);

    lv_snprintf(buf, line_max, "%.2fV", ui_batt_25896_get_vsys());
    battery_set_line(label_list[2], "VSYS:", buf);

    lv_snprintf(buf, line_max, "%.2fV", ui_batt_25896_get_vbat());
    battery_set_line(label_list[3], "VBAT:", buf);

    lv_snprintf(buf, line_max, "%.2fv", ui_batt_25896_get_volt_targ());
    battery_set_line(label_list[4], "VOLT Target:", buf);

    lv_snprintf(buf, line_max, "%.2fmA", ui_batt_25896_get_chg_curr());
    battery_set_line(label_list[5], "Charge Curr:", buf);

    lv_snprintf(buf, line_max, "%.2fmA", ui_batt_25896_get_pre_curr());
    battery_set_line(label_list[6], "Prechg Curr:", buf);

    lv_snprintf(buf, line_max, "%s", ui_batt_25896_get_chg_st());
    battery_set_line(label_list[7], "CHG ST:", buf);

    lv_snprintf(buf, line_max, "%s", ui_batt_25896_get_vbus_st());
    battery_set_line(label_list[8], "VBUS Status:", buf);

    lv_snprintf(buf, line_max, "%s", ui_batt_25896_get_ntc_st());
    battery_set_line(label_list[9], " ", buf);
}

static void batt_6_1_updata_timer_event(lv_timer_t *t) 
{
    scr6_1_battert_updata();
}

static void scr6_1_btn_event_cb(lv_event_t * e)
{
    if(e->code == LV_EVENT_CLICKED){
        scr_mgr_pop(false);
    }
}

static void create6_1(lv_obj_t *parent) 
{
    lv_obj_t *scr6_1_cont = lv_obj_create(parent);
    lv_obj_set_size(scr6_1_cont, lv_pct(100), lv_pct(88));
    lv_obj_set_style_bg_color(scr6_1_cont, DECKPRO_COLOR_BG, LV_PART_MAIN);
    lv_obj_set_scrollbar_mode(scr6_1_cont, LV_SCROLLBAR_MODE_OFF);
    lv_obj_clear_flag(scr6_1_cont, LV_OBJ_FLAG_SCROLLABLE);
    lv_obj_set_style_border_width(scr6_1_cont, 0, LV_PART_MAIN);
    lv_obj_set_style_pad_all(scr6_1_cont, 0, LV_PART_MAIN);
    lv_obj_set_style_pad_hor(scr6_1_cont, 0, LV_PART_MAIN);
    lv_obj_set_style_pad_row(scr6_1_cont, 5, LV_PART_MAIN);
    lv_obj_set_style_pad_column(scr6_1_cont, 0, LV_PART_MAIN);
    lv_obj_set_align(scr6_1_cont, LV_ALIGN_BOTTOM_LEFT);
    lv_obj_set_flex_flow(scr6_1_cont, LV_FLEX_FLOW_COLUMN);
    lv_obj_set_flex_align(scr6_1_cont, LV_FLEX_ALIGN_START, LV_FLEX_ALIGN_START, LV_FLEX_ALIGN_CENTER);

    for(int i = 0; i < sizeof(label_list) / sizeof(label_list[0]); i++) {
        label_list[i] = scr6_1_create_label(scr6_1_cont);
    }

    scr_back_btn_create(parent, ("SY6970"), scr6_1_btn_event_cb);
}
static void entry6_1(void) 
{
    scr6_1_battert_updata();
    ui_disp_full_refr();
    batt_6_1_timer = lv_timer_create(batt_6_1_updata_timer_event, 5000, NULL);
}
static void exit6_1(void) {
    if(batt_6_1_timer) {
        lv_timer_del(batt_6_1_timer);
        batt_6_1_timer = NULL;
    }
    ui_disp_full_refr();
}
static void destroy6_1(void) { }

static scr_lifecycle_t screen6_1 = {
    .create = create6_1,
    .entry = entry6_1,
    .exit  = exit6_1,
    .destroy = destroy6_1,
};
#undef line_max

#endif
// --------------------- screen 6.2 --------------------- BQ27220
#if 1

#define line_max 23

static lv_timer_t *batt_6_2_timer = NULL;

static lv_obj_t * scr6_2_create_label(lv_obj_t *parent)
{
    lv_obj_t *label = lv_label_create(parent);
    lv_obj_set_width(label, lv_pct(90));
    lv_obj_set_style_text_font(label, FONT_BOLD_MONO_SIZE_15, LV_PART_MAIN);   
    lv_obj_set_style_border_width(label, 1, LV_PART_MAIN);
    lv_label_set_long_mode(label, LV_LABEL_LONG_WRAP);
    lv_obj_set_style_border_side(label, LV_BORDER_SIDE_BOTTOM, LV_PART_MAIN);
    return label;
}

static void scr6_2_battert_updata(void)
{
    char buf[line_max];

    battery_set_line(label_list[0],"VBUS ST::", (ui_battery_27220_get_input() == true ? "Connected" : "Disonnected"));

    if(ui_battery_27220_get_input() == true ){
        lv_snprintf(buf, line_max, "%s", (ui_battery_27220_get_charge_finish()? "Finsish":"Charging"));
    } else {
        lv_snprintf(buf, line_max, "%s", "Discharge");
    }
    battery_set_line(label_list[1],"Charing ST:", buf);

    lv_snprintf(buf, line_max, "0x%x", ui_battery_27220_get_status());
    battery_set_line(label_list[2],"Battery ST:", buf);

    lv_snprintf(buf, line_max, "%dmV", ui_battery_27220_get_voltage());
    battery_set_line(label_list[3], "Voltage:", buf);

    lv_snprintf(buf, line_max, "%dmA", ui_battery_27220_get_current());
    battery_set_line(label_list[4], "Current:", buf);

    lv_snprintf(buf, line_max, "%.2fC", (float)(ui_battery_27220_get_temperature() / 10.0 - 273.0));
    battery_set_line(label_list[5], "Temperature:", buf);

    lv_snprintf(buf, line_max, "%dmAh", ui_battery_27220_get_remain_capacity());
    battery_set_line(label_list[6], "Cap Remain:", buf);

    lv_snprintf(buf, line_max, "%dmAh", ui_battery_27220_get_full_capacity());
    battery_set_line(label_list[7], "Cap Full:", buf);

    lv_snprintf(buf, line_max, "%d%%", ui_battery_27220_get_percent());
    battery_set_line(label_list[8], "Cap Percent:", buf);

    lv_snprintf(buf, line_max, "%d%%", ui_battery_27220_get_health());
    battery_set_line(label_list[9], "CapHealth:", buf);
}

static void batt_6_2_updata_timer_event(lv_timer_t *t) 
{
    scr6_2_battert_updata();
}

static void scr6_2_btn_event_cb(lv_event_t * e)
{
    if(e->code == LV_EVENT_CLICKED){
        scr_mgr_pop(false);
    }
}

static void create6_2(lv_obj_t *parent) 
{   
    lv_obj_t *scr6_2_cont = lv_obj_create(parent);
    lv_obj_set_size(scr6_2_cont, lv_pct(100), lv_pct(88));
    lv_obj_set_style_bg_color(scr6_2_cont, DECKPRO_COLOR_BG, LV_PART_MAIN);
    lv_obj_set_scrollbar_mode(scr6_2_cont, LV_SCROLLBAR_MODE_OFF);
    lv_obj_clear_flag(scr6_2_cont, LV_OBJ_FLAG_SCROLLABLE);
    lv_obj_set_style_border_width(scr6_2_cont, 0, LV_PART_MAIN);
    lv_obj_set_style_pad_all(scr6_2_cont, 0, LV_PART_MAIN);
    lv_obj_set_style_pad_hor(scr6_2_cont, 0, LV_PART_MAIN);
    lv_obj_set_style_pad_row(scr6_2_cont, 5, LV_PART_MAIN);
    lv_obj_set_style_pad_column(scr6_2_cont, 0, LV_PART_MAIN);
    lv_obj_set_align(scr6_2_cont, LV_ALIGN_BOTTOM_LEFT);
    lv_obj_set_flex_flow(scr6_2_cont, LV_FLEX_FLOW_COLUMN);
    lv_obj_set_flex_align(scr6_2_cont, LV_FLEX_ALIGN_START, LV_FLEX_ALIGN_START, LV_FLEX_ALIGN_CENTER);

    for(int i = 0; i < sizeof(label_list) / sizeof(label_list[0]); i++) {
        label_list[i] = scr6_2_create_label(scr6_2_cont);
    }
    // back
    scr_back_btn_create(parent, ("BQ27220"), scr6_btn_event_cb);
}

static void entry6_2(void) 
{
    scr6_2_battert_updata();
    ui_disp_full_refr();
    batt_6_2_timer = lv_timer_create(batt_6_2_updata_timer_event, 5000, NULL);
}
static void exit6_2(void) {
    if(batt_6_2_timer) {
        lv_timer_del(batt_6_2_timer);
        batt_6_2_timer = NULL;
    }
    ui_disp_full_refr();
}

static void destroy6_2(void) { }

static scr_lifecycle_t screen6_2 = {
    .create = create6_2,
    .entry = entry6_2,
    .exit  = exit6_2,
    .destroy = destroy6_2,
};
#undef line_max
#endif
//************************************[ screen 7 ]****************************************** Other
#if 1
static lv_obj_t *scr7_cont;
static lv_obj_t *input_touch;
static lv_obj_t *input_keypad;
static lv_obj_t *gyroscope;
static lv_timer_t *input_timer;

static void scr7_btn_event_cb(lv_event_t * e)
{
    if(e->code == LV_EVENT_CLICKED){
        scr_mgr_pop(false);
    }
}

static void input_timer_event(lv_timer_t *t)
{
    int touch_x, touch_y;

    int ret = ui_input_get_touch_coord(&touch_x, &touch_y);

    if(ret > 0)
    {
        lv_label_set_text_fmt(input_touch,  "Touch: x: %03d | y: %03d", touch_x, touch_y);
    }

    char keypay_v;
    ret = ui_input_get_keypay_val(&keypay_v);
    if(ret > 0)
    {
        ui_input_set_keypay_flag();
        lv_label_set_text_fmt(input_keypad, "Keypad: %s", keypad_key_name(keypay_v));
    }

    static int sec = 0;
    int ch0, ch1 ,ps;
    float gyro_x, gyro_y, gyro_z;

    sec++;
    if(sec > 20) // 2s
    {
        sec = 0;

        ui_other_get_gyro(&gyro_x, &gyro_y, &gyro_z);
        lv_label_set_text_fmt(gyroscope,    "   gyros_x: %.3f\n"
                                            "   gyros_y: %.3f\n"
                                            "   gyros_z: %.3f", gyro_x, gyro_y, gyro_z);
    }
}

static void create7(lv_obj_t *parent) 
{
    scr7_cont = lv_obj_create(parent);
    lv_obj_set_size(scr7_cont, lv_pct(100), lv_pct(88));
    lv_obj_set_style_bg_color(scr7_cont, DECKPRO_COLOR_BG, LV_PART_MAIN);
    lv_obj_set_scrollbar_mode(scr7_cont, LV_SCROLLBAR_MODE_OFF);
    lv_obj_clear_flag(scr7_cont, LV_OBJ_FLAG_SCROLLABLE);
    lv_obj_set_style_border_width(scr7_cont, 0, LV_PART_MAIN);
    lv_obj_set_style_pad_all(scr7_cont, 0, LV_PART_MAIN);
    lv_obj_set_style_pad_left(scr7_cont, 13, LV_PART_MAIN);
    lv_obj_set_flex_flow(scr7_cont, LV_FLEX_FLOW_COLUMN);
    lv_obj_set_style_pad_row(scr7_cont, 10, LV_PART_MAIN);
    lv_obj_set_style_pad_column(scr7_cont, 5, LV_PART_MAIN);
    lv_obj_set_align(scr7_cont, LV_ALIGN_BOTTOM_MID);

    input_touch = lv_label_create(scr7_cont);
    // lv_obj_set_height(input_touch, 90);
    lv_obj_set_width(input_touch, lv_pct(95));
    lv_obj_set_style_pad_all(input_touch, 0, LV_PART_MAIN);
    lv_obj_set_style_text_font(input_touch, FONT_BOLD_MONO_SIZE_15, LV_PART_MAIN);
    // lv_obj_set_style_border_width(input_touch, 1, LV_PART_MAIN);
    lv_label_set_long_mode(input_touch, LV_LABEL_LONG_WRAP);
    lv_label_set_text(input_touch,  "Touch: x:     | y:    ");

    input_keypad = lv_label_create(scr7_cont);
    // lv_obj_set_height(input_keypad, 100);
    lv_obj_set_width(input_keypad, lv_pct(95));
    lv_obj_set_style_pad_all(input_keypad, 0, LV_PART_MAIN);
    lv_obj_set_style_text_font(input_keypad, FONT_BOLD_MONO_SIZE_15, LV_PART_MAIN);
    // lv_obj_set_style_border_width(input_keypad, 1, LV_PART_MAIN);
    lv_label_set_long_mode(input_keypad, LV_LABEL_LONG_WRAP);
    lv_label_set_text_fmt(input_keypad, "Keypad: ");

    lv_obj_t *lab2 = lv_label_create(scr7_cont);
    lv_obj_set_style_text_font(lab2, FONT_BOLD_MONO_SIZE_15, LV_PART_MAIN);
    lv_label_set_text(lab2, "gyroscope");

    gyroscope = lv_label_create(scr7_cont);
    // lv_obj_set_height(input_keypad, 100);
    lv_obj_set_width(gyroscope, lv_pct(95));
    lv_obj_set_style_pad_all(gyroscope, 0, LV_PART_MAIN);
    lv_obj_set_style_text_font(gyroscope, FONT_BOLD_MONO_SIZE_15, LV_PART_MAIN);
    // lv_obj_set_style_border_width(gyroscope, 1, LV_PART_MAIN);
    lv_label_set_long_mode(gyroscope, LV_LABEL_LONG_WRAP);
    lv_label_set_text_fmt(gyroscope,    "   gyros_x: 000\n"
                                        "   gyros_y: 000\n"
                                        "   gyros_z: 000");

    lv_obj_t *back7_label = scr_back_btn_create(parent, ("Other"), scr7_btn_event_cb);
}
static void entry7(void) 
{
    ui_disp_full_refr();
    input_timer = lv_timer_create(input_timer_event, 100, NULL);
}
static void exit7(void) {
    if(input_timer)
    {
        lv_timer_del(input_timer);
        input_timer = NULL;
    }
    ui_disp_full_refr();
}
static void destroy7(void) { }

static scr_lifecycle_t screen7 = {
    .create = create7,
    .entry = entry7,
    .exit  = exit7,
    .destroy = destroy7,
};
#endif
//************************************[ screen 8 ]****************************************** A7682E
// --------------------- screen 8 --------------------- Phone
#if 1
static lv_obj_t *phone_dialer_ta = NULL;
static lv_obj_t *phone_dialer_status = NULL;
static lv_obj_t *phone_dialer_call_btn = NULL;
static lv_obj_t *phone_dialer_del_btn = NULL;
static lv_obj_t *phone_dialer_at_btn = NULL;
static lv_obj_t *phone_dialer_test_btn = NULL;
static lv_obj_t *phone_dialer_recent[UI_PHONE_HISTORY_MAX] = {0};

static lv_obj_t *phone_call_status = NULL;
static lv_obj_t *phone_call_number = NULL;
static lv_obj_t *phone_call_timer = NULL;

static lv_obj_t *phone_incoming_title = NULL;
static lv_obj_t *phone_incoming_number = NULL;

static lv_obj_t *phone_debug_label = NULL;

static int phone_active_screen = -1;
static bool phone_stack_active = false;
static bool phone_keypad_touch_down = false;
static ui_phone_state_t phone_last_state = UI_PHONE_STATE_UNAVAILABLE;

static const char phone_keypad_chars[4][3] = {
    {'1', '2', '3'},
    {'4', '5', '6'},
    {'7', '8', '9'},
    {'*', '0', '#'},
};

#define PHONE_KEYPAD_X 8
#define PHONE_KEYPAD_Y 96
#define PHONE_KEYPAD_W 224
#define PHONE_KEYPAD_H 118
#define PHONE_KEYPAD_COLS 3
#define PHONE_KEYPAD_ROWS 4

static void phone_set_button_enabled(lv_obj_t *btn, bool enabled)
{
    if (btn == NULL) {
        return;
    }

    bool disabled = lv_obj_has_state(btn, LV_STATE_DISABLED);
    if ((enabled && !disabled) || (!enabled && disabled)) {
        return;
    }

    if (enabled) {
        lv_obj_clear_state(btn, LV_STATE_DISABLED);
    } else {
        lv_obj_add_state(btn, LV_STATE_DISABLED);
    }
}

static void phone_set_label_text(lv_obj_t *label, const char *text)
{
    if (label == NULL) {
        return;
    }

    const char *safe_text = (text != NULL) ? text : "";
    const char *current_text = lv_label_get_text(label);
    if (current_text != NULL && strcmp(current_text, safe_text) == 0) {
        return;
    }

    lv_label_set_text(label, safe_text);
}

static lv_obj_t *phone_action_button_create(lv_obj_t *parent, const char *text, lv_coord_t x,
                                            lv_coord_t y, lv_coord_t w, bool filled,
                                            lv_event_cb_t cb)
{
    lv_obj_t *btn = lv_btn_create(parent);
    lv_obj_set_size(btn, w, 42);
    lv_obj_align(btn, LV_ALIGN_CENTER, x, y);
    lv_obj_clear_flag(btn, LV_OBJ_FLAG_SCROLLABLE);
    lv_obj_set_style_radius(btn, 8, LV_PART_MAIN);
    lv_obj_set_style_border_width(btn, 2, LV_PART_MAIN);
    lv_obj_set_style_border_color(btn, DECKPRO_COLOR_FG, LV_PART_MAIN);
    lv_obj_set_style_shadow_width(btn, 0, LV_PART_MAIN);
    lv_obj_set_style_bg_color(btn, filled ? DECKPRO_COLOR_FG : DECKPRO_COLOR_BG, LV_PART_MAIN | LV_STATE_DEFAULT);
    lv_obj_set_style_text_color(btn, filled ? DECKPRO_COLOR_BG : DECKPRO_COLOR_FG, LV_PART_MAIN | LV_STATE_DEFAULT);
    lv_obj_set_style_bg_color(btn, filled ? DECKPRO_COLOR_FG : DECKPRO_COLOR_BG, LV_PART_MAIN | LV_STATE_PRESSED);
    lv_obj_set_style_text_color(btn, filled ? DECKPRO_COLOR_BG : DECKPRO_COLOR_FG, LV_PART_MAIN | LV_STATE_PRESSED);
    lv_obj_set_style_border_color(btn, DECKPRO_COLOR_FG, LV_PART_MAIN | LV_STATE_PRESSED);
    lv_obj_set_style_shadow_width(btn, 0, LV_PART_MAIN | LV_STATE_PRESSED);
    lv_obj_add_event_cb(btn, cb, LV_EVENT_CLICKED, NULL);

    lv_obj_t *label = lv_label_create(btn);
    lv_obj_center(label);
    lv_label_set_text(label, text);
    lv_obj_set_style_text_color(label, filled ? DECKPRO_COLOR_BG : DECKPRO_COLOR_FG, LV_PART_MAIN | LV_STATE_DEFAULT);
    lv_obj_set_style_text_font(label, FONT_BOLD_SIZE_15, LV_PART_MAIN);

    return btn;
}

static void phone_format_duration(uint32_t duration_sec, char *buf, size_t len)
{
    if (duration_sec >= 3600U) {
        lv_snprintf(buf, len, "%02lu:%02lu:%02lu",
                    duration_sec / 3600UL,
                    (duration_sec / 60UL) % 60UL,
                    duration_sec % 60UL);
    } else {
        lv_snprintf(buf, len, "%02lu:%02lu",
                    duration_sec / 60UL,
                    duration_sec % 60UL);
    }
}

static void phone_history_to_text(const ui_phone_history_item_t *item, char *buf, size_t len)
{
    if (item == NULL || item->sequence == 0U) {
        lv_snprintf(buf, len, "-");
        return;
    }

    lv_snprintf(buf, len, "%s: %s (%s)", item->direction, item->number, item->result);
}

static char phone_keypad_to_digit(char key)
{
    char lower = (char)tolower((unsigned char)key);
    if (lower >= '0' && lower <= '9') {
        return lower;
    }

    switch (lower) {
    case KEYPAD_KEY_UP: return '1';
    case 'a':
    case 'b':
    case 'c': return '2';
    case 'd':
    case 'e':
    case 'f': return '3';
    case 'g':
    case 'h':
    case 'i': return '4';
    case 'j':
    case 'k':
    case 'l': return '5';
    case 'm':
    case 'n':
    case 'o': return '6';
    case 'p':
    case 'q':
    case 'r':
    case 's': return '7';
    case 't':
    case 'u':
    case 'v': return '8';
    case 'w':
    case 'x':
    case 'y':
    case 'z': return '9';
    case KEYPAD_KEY_ALT: return '*';
    case KEYPAD_KEY_SYM: return '#';
    default: return '\0';
    }
}

static void phone_dialer_add_char(char c)
{
    if (phone_dialer_ta == NULL || c == '\0') {
        return;
    }

    char txt[2] = {c, '\0'};
    ui_disp_partial_refr_for(250);
    lv_textarea_add_text(phone_dialer_ta, txt);
}

static char phone_keypad_hit_test(int x, int y)
{
    if (x < PHONE_KEYPAD_X ||
        x >= (PHONE_KEYPAD_X + PHONE_KEYPAD_W) ||
        y < PHONE_KEYPAD_Y ||
        y >= (PHONE_KEYPAD_Y + PHONE_KEYPAD_H)) {
        return '\0';
    }

    int col = ((x - PHONE_KEYPAD_X) * PHONE_KEYPAD_COLS) / PHONE_KEYPAD_W;
    int row = ((y - PHONE_KEYPAD_Y) * PHONE_KEYPAD_ROWS) / PHONE_KEYPAD_H;
    if (col < 0 || col >= PHONE_KEYPAD_COLS || row < 0 || row >= PHONE_KEYPAD_ROWS) {
        return '\0';
    }

    return phone_keypad_chars[row][col];
}

static void phone_handle_touch_keypad(const ui_phone_snapshot_t *snapshot)
{
    if (phone_active_screen != SCREEN8_ID ||
        phone_dialer_ta == NULL ||
        snapshot == NULL ||
        snapshot->state != UI_PHONE_STATE_IDLE ||
        strcmp(snapshot->status, "Testing 0-9") == 0) {
        phone_keypad_touch_down = false;
        return;
    }

    lv_indev_t *touch_indev = lv_indev_get_next(NULL);
    if (touch_indev == NULL || touch_indev->proc.state != LV_INDEV_STATE_PRESSED) {
        phone_keypad_touch_down = false;
        return;
    }

    lv_point_t point = {};
    lv_indev_get_point(touch_indev, &point);

    char digit = phone_keypad_hit_test(point.x, point.y);
    if (digit == '\0') {
        return;
    }

    if (!phone_keypad_touch_down) {
        phone_dialer_add_char(digit);
    }
    phone_keypad_touch_down = true;
}

static void phone_refresh_dialer(const ui_phone_snapshot_t *snapshot)
{
    if (snapshot == NULL || phone_dialer_status == NULL) {
        return;
    }

    const char *status = snapshot->status;
    bool idle_actions_enabled = snapshot->state == UI_PHONE_STATE_IDLE &&
                                strcmp(status, "Testing 0-9") != 0;
    if (snapshot->state == UI_PHONE_STATE_UNAVAILABLE) {
        status = "A7682E Failed";
    }

    phone_set_label_text(phone_dialer_status, status);
    phone_set_button_enabled(phone_dialer_call_btn,
                             idle_actions_enabled &&
                             phone_dialer_ta != NULL &&
                             strlen(lv_textarea_get_text(phone_dialer_ta)) > 0U);
    phone_set_button_enabled(phone_dialer_at_btn, idle_actions_enabled);
    phone_set_button_enabled(phone_dialer_test_btn, idle_actions_enabled);

    for (int i = 0; i < UI_PHONE_HISTORY_MAX; ++i) {
        if (phone_dialer_recent[i] == NULL) {
            continue;
        }
        char line[80] = {0};
        phone_history_to_text(&snapshot->recent_calls[i], line, sizeof(line));
        phone_set_label_text(phone_dialer_recent[i], line);
    }
}

static void phone_refresh_call_screen(const ui_phone_snapshot_t *snapshot)
{
    if (snapshot == NULL || phone_call_status == NULL || phone_call_number == NULL || phone_call_timer == NULL) {
        return;
    }

    phone_set_label_text(phone_call_status, snapshot->status[0] ? snapshot->status : "Calling");
    phone_set_label_text(phone_call_number, snapshot->current_number[0] ? snapshot->current_number : "Unknown");

    char timer_buf[16] = {0};
    phone_format_duration(snapshot->call_duration_sec, timer_buf, sizeof(timer_buf));
    phone_set_label_text(phone_call_timer, timer_buf);
}

static void phone_refresh_incoming(const ui_phone_snapshot_t *snapshot)
{
    if (snapshot == NULL || phone_incoming_title == NULL || phone_incoming_number == NULL) {
        return;
    }

    phone_set_label_text(phone_incoming_title, "Incoming Call");
    phone_set_label_text(phone_incoming_number, snapshot->current_number[0] ? snapshot->current_number : "Unknown");
}

static void phone_refresh_debug(const ui_phone_snapshot_t *snapshot)
{
    if (snapshot == NULL || phone_debug_label == NULL) {
        return;
    }

    phone_set_label_text(phone_debug_label,
                         "Serial bridge is active at 115200.\n"
                         "Use the host serial monitor for AT commands.\n"
                         "Leave this page to restore phone monitoring.");
}

static void phone_refresh_all(const ui_phone_snapshot_t *snapshot)
{
    phone_refresh_dialer(snapshot);
    phone_refresh_call_screen(snapshot);
    phone_refresh_incoming(snapshot);
    phone_refresh_debug(snapshot);
}

static void phone_handle_dial_request(void)
{
    if (phone_dialer_ta == NULL) {
        return;
    }

    const char *number = lv_textarea_get_text(phone_dialer_ta);
    if (number != NULL && number[0] != '\0') {
        (void)ui_phone_dial(number);
    }
}

static void phone_back_btn_event_cb(lv_event_t *e)
{
    if (e->code == LV_EVENT_CLICKED) {
        scr_mgr_pop(false);
    }
}

static void scr8_btn_event_cb(lv_event_t *e)
{
    phone_back_btn_event_cb(e);
}

static void phone_dialer_call_event_cb(lv_event_t *e)
{
    if (e->code == LV_EVENT_CLICKED) {
        phone_handle_dial_request();
    }
}

static void phone_dialer_del_event_cb(lv_event_t *e)
{
    if (e->code == LV_EVENT_CLICKED && phone_dialer_ta != NULL) {
        lv_textarea_del_char(phone_dialer_ta);
    }
}

static void phone_debug_open_event_cb(lv_event_t *e)
{
    if (e->code != LV_EVENT_CLICKED) {
        return;
    }

    ui_phone_snapshot_t snapshot = {};
    if (ui_phone_get_snapshot(&snapshot) && snapshot.state == UI_PHONE_STATE_IDLE) {
        scr_mgr_push(SCREEN8_3_ID, false);
    }
}

static void phone_test_digits_event_cb(lv_event_t *e)
{
    if (e->code != LV_EVENT_CLICKED) {
        return;
    }

    ui_phone_snapshot_t snapshot = {};
    if (ui_phone_get_snapshot(&snapshot) && snapshot.state == UI_PHONE_STATE_IDLE) {
        (void)ui_phone_play_test_digits();
    }
}

static void phone_answer_event_cb(lv_event_t *e)
{
    if (e->code == LV_EVENT_CLICKED) {
        (void)ui_phone_answer();
    }
}

static void phone_reject_event_cb(lv_event_t *e)
{
    if (e->code == LV_EVENT_CLICKED) {
        (void)ui_phone_hang_up();
    }
}

static void phone_end_call_event_cb(lv_event_t *e)
{
    if (e->code == LV_EVENT_CLICKED) {
        (void)ui_phone_hang_up();
    }
}

static void phone_handle_keyboard(void)
{
    if (phone_active_screen < SCREEN8_ID || phone_active_screen > SCREEN8_3_ID) {
        return;
    }

    char key = '\0';
    if (!ui_input_get_keypay_val(&key)) {
        return;
    }
    ui_input_set_keypay_flag();

    switch (phone_active_screen) {
    case SCREEN8_ID:
        if (key == KEYPAD_KEY_DEL) {
            if (phone_dialer_ta) {
                lv_textarea_del_char(phone_dialer_ta);
            }
        } else if (key == KEYPAD_KEY_ENT) {
            phone_handle_dial_request();
        } else {
            char mapped = phone_keypad_to_digit(key);
            phone_dialer_add_char(mapped);
        }
        break;
    case SCREEN8_1_ID:
        if (key == KEYPAD_KEY_DEL || key == KEYPAD_KEY_ENT) {
            (void)ui_phone_hang_up();
        }
        break;
    case SCREEN8_2_ID:
        if (key == KEYPAD_KEY_DEL) {
            (void)ui_phone_hang_up();
        } else if (key == KEYPAD_KEY_ENT) {
            (void)ui_phone_answer();
        }
        break;
    default:
        break;
    }
}

static void phone_state_timer_cb(lv_timer_t *t)
{
    (void)t;

    ui_phone_snapshot_t snapshot = {};
    if (!ui_phone_get_snapshot(&snapshot)) {
        return;
    }

    phone_handle_keyboard();
    phone_handle_touch_keypad(&snapshot);
    phone_refresh_all(&snapshot);

    if (snapshot.state == UI_PHONE_STATE_INCOMING) {
        if (!phone_stack_active) {
            phone_stack_active = true;
            scr_mgr_push(SCREEN8_2_ID, false);
        }
    } else if ((snapshot.state == UI_PHONE_STATE_OUTGOING || snapshot.state == UI_PHONE_STATE_ACTIVE) &&
               !phone_stack_active &&
               phone_active_screen != SCREEN8_3_ID) {
        phone_stack_active = true;
        scr_mgr_push(SCREEN8_1_ID, false);
    }

    if (snapshot.state == UI_PHONE_STATE_ACTIVE &&
        phone_stack_active &&
        phone_active_screen == SCREEN8_2_ID) {
        scr_mgr_replace_top(SCREEN8_1_ID, false);
    }

    if ((snapshot.state == UI_PHONE_STATE_IDLE || snapshot.state == UI_PHONE_STATE_UNAVAILABLE) &&
        phone_stack_active) {
        phone_stack_active = false;
        scr_mgr_pop(false);
    }

    phone_last_state = snapshot.state;
}

static void create8(lv_obj_t *parent)
{
    phone_dialer_ta = lv_textarea_create(parent);
    lv_textarea_set_one_line(phone_dialer_ta, true);
    lv_obj_set_size(phone_dialer_ta, 224, 38);
    lv_obj_align(phone_dialer_ta, LV_ALIGN_TOP_MID, 0, 34);
    lv_obj_clear_flag(phone_dialer_ta, LV_OBJ_FLAG_CLICKABLE);
    lv_obj_set_style_text_font(phone_dialer_ta, &Font_Mono_Bold_20, LV_PART_MAIN);
    lv_obj_set_style_text_align(phone_dialer_ta, LV_TEXT_ALIGN_CENTER, LV_PART_MAIN);
    lv_obj_set_style_pad_top(phone_dialer_ta, 7, LV_PART_MAIN);
    lv_textarea_set_placeholder_text(phone_dialer_ta, "Number");

    phone_dialer_status = lv_label_create(parent);
    lv_obj_set_width(phone_dialer_status, lv_pct(96));
    lv_obj_align(phone_dialer_status, LV_ALIGN_TOP_MID, 0, 78);
    lv_obj_set_style_text_align(phone_dialer_status, LV_TEXT_ALIGN_CENTER, LV_PART_MAIN);
    lv_obj_set_style_text_font(phone_dialer_status, FONT_BOLD_SIZE_14, LV_PART_MAIN);

    for (int row = 0; row < PHONE_KEYPAD_ROWS; ++row) {
        for (int col = 0; col < PHONE_KEYPAD_COLS; ++col) {
            lv_obj_t *cell = lv_obj_create(parent);
            lv_obj_remove_style_all(cell);
            lv_obj_clear_flag(cell, LV_OBJ_FLAG_CLICKABLE | LV_OBJ_FLAG_SCROLLABLE);
            lv_obj_set_size(cell,
                            PHONE_KEYPAD_W / PHONE_KEYPAD_COLS,
                            PHONE_KEYPAD_H / PHONE_KEYPAD_ROWS);
            lv_obj_align(cell,
                         LV_ALIGN_TOP_LEFT,
                         PHONE_KEYPAD_X + ((PHONE_KEYPAD_W * col) / PHONE_KEYPAD_COLS),
                         PHONE_KEYPAD_Y + ((PHONE_KEYPAD_H * row) / PHONE_KEYPAD_ROWS));
            lv_obj_set_style_bg_color(cell, DECKPRO_COLOR_BG, LV_PART_MAIN);
            lv_obj_set_style_bg_opa(cell, LV_OPA_COVER, LV_PART_MAIN);
            lv_obj_set_style_border_width(cell, 1, LV_PART_MAIN);
            lv_obj_set_style_border_color(cell, DECKPRO_COLOR_FG, LV_PART_MAIN);

            lv_obj_t *label = lv_label_create(cell);
            lv_obj_set_style_text_font(label, FONT_BOLD_SIZE_16, LV_PART_MAIN);
            lv_obj_set_style_text_color(label, DECKPRO_COLOR_FG, LV_PART_MAIN);
            char digit_text[2] = {phone_keypad_chars[row][col], '\0'};
            lv_label_set_text(label, digit_text);
            lv_obj_center(label);
        }
    }

    phone_dialer_call_btn = phone_action_button_create(parent, "Call", -58, 98, 115, true, phone_dialer_call_event_cb);
    phone_dialer_del_btn = phone_action_button_create(parent, "Del", 58, 98, 115, false, phone_dialer_del_event_cb);
    lv_obj_set_height(phone_dialer_call_btn, 34);
    lv_obj_set_height(phone_dialer_del_btn, 34);
    lv_obj_align(phone_dialer_call_btn, LV_ALIGN_TOP_LEFT, 4, 220);
    lv_obj_align(phone_dialer_del_btn, LV_ALIGN_TOP_RIGHT, -4, 220);

    phone_dialer_at_btn = phone_action_button_create(parent, "AT", 87, -130, 46, false, phone_debug_open_event_cb);
    lv_obj_set_size(phone_dialer_at_btn, 46, 28);
    lv_obj_align(phone_dialer_at_btn, LV_ALIGN_TOP_RIGHT, -54, 3);

    phone_dialer_test_btn = phone_action_button_create(parent, "Test", 87, -130, 46, false, phone_test_digits_event_cb);
    lv_obj_set_size(phone_dialer_test_btn, 46, 28);
    lv_obj_align(phone_dialer_test_btn, LV_ALIGN_TOP_RIGHT, -6, 3);

    lv_obj_t *recent_title = lv_label_create(parent);
    lv_obj_align(recent_title, LV_ALIGN_TOP_LEFT, 8, 256);
    lv_obj_set_style_text_font(recent_title, FONT_BOLD_SIZE_14, LV_PART_MAIN);
    lv_label_set_text(recent_title, "Recent Calls");

    for (int i = 0; i < UI_PHONE_HISTORY_MAX; ++i) {
        phone_dialer_recent[i] = lv_label_create(parent);
        lv_obj_set_width(phone_dialer_recent[i], lv_pct(95));
        lv_obj_align(phone_dialer_recent[i], LV_ALIGN_TOP_LEFT, 8, 272 + (i * 16));
        lv_obj_set_style_text_font(phone_dialer_recent[i], FONT_BOLD_SIZE_14, LV_PART_MAIN);
        lv_label_set_long_mode(phone_dialer_recent[i], LV_LABEL_LONG_CLIP);
        lv_label_set_text(phone_dialer_recent[i], "-");
    }

    scr_back_btn_create(parent, "Phone", phone_back_btn_event_cb);
}

static void entry8(void)
{
    phone_active_screen = SCREEN8_ID;
    phone_keypad_touch_down = false;
    ui_phone_snapshot_t snapshot = {};
    if (ui_phone_get_snapshot(&snapshot)) {
        phone_refresh_all(&snapshot);
    }
    ui_disp_full_refr();
}

static void exit8(void)
{
    if (phone_active_screen == SCREEN8_ID) {
        phone_active_screen = -1;
    }
    phone_keypad_touch_down = false;
    ui_disp_full_refr();
}

static void destroy8(void)
{
    phone_dialer_ta = NULL;
    phone_dialer_status = NULL;
    phone_dialer_call_btn = NULL;
    phone_dialer_del_btn = NULL;
    phone_dialer_at_btn = NULL;
    phone_dialer_test_btn = NULL;
    for (int i = 0; i < UI_PHONE_HISTORY_MAX; ++i) {
        phone_dialer_recent[i] = NULL;
    }
}

static scr_lifecycle_t screen8 = {
    .create = create8,
    .entry = entry8,
    .exit  = exit8,
    .destroy = destroy8,
};

static void create8_1(lv_obj_t *parent)
{
    phone_call_status = lv_label_create(parent);
    lv_obj_set_width(phone_call_status, lv_pct(100));
    lv_obj_align(phone_call_status, LV_ALIGN_TOP_MID, 0, 36);
    lv_obj_set_style_text_align(phone_call_status, LV_TEXT_ALIGN_CENTER, LV_PART_MAIN);
    lv_obj_set_style_text_font(phone_call_status, FONT_BOLD_SIZE_17, LV_PART_MAIN);
    lv_label_set_text(phone_call_status, "Calling");

    phone_call_number = lv_label_create(parent);
    lv_obj_set_width(phone_call_number, lv_pct(100));
    lv_obj_align(phone_call_number, LV_ALIGN_TOP_MID, 0, 92);
    lv_obj_set_style_text_align(phone_call_number, LV_TEXT_ALIGN_CENTER, LV_PART_MAIN);
    lv_obj_set_style_text_font(phone_call_number, &Font_Mono_Bold_20, LV_PART_MAIN);
    lv_label_set_text(phone_call_number, "Unknown");

    phone_call_timer = lv_label_create(parent);
    lv_obj_set_width(phone_call_timer, lv_pct(100));
    lv_obj_align(phone_call_timer, LV_ALIGN_TOP_MID, 0, 146);
    lv_obj_set_style_text_align(phone_call_timer, LV_TEXT_ALIGN_CENTER, LV_PART_MAIN);
    lv_obj_set_style_text_font(phone_call_timer, FONT_BOLD_SIZE_18, LV_PART_MAIN);
    lv_label_set_text(phone_call_timer, "00:00");

    phone_action_button_create(parent, "End Call", 0, 122, 148, true, phone_end_call_event_cb);
}

static void entry8_1(void)
{
    phone_active_screen = SCREEN8_1_ID;
    ui_phone_snapshot_t snapshot = {};
    if (ui_phone_get_snapshot(&snapshot)) {
        phone_refresh_all(&snapshot);
    }
    ui_disp_full_refr();
}

static void exit8_1(void)
{
    if (phone_active_screen == SCREEN8_1_ID) {
        phone_active_screen = -1;
    }
    ui_disp_full_refr();
}

static void destroy8_1(void)
{
    phone_call_status = NULL;
    phone_call_number = NULL;
    phone_call_timer = NULL;
}

static scr_lifecycle_t screen8_1 = {
    .create = create8_1,
    .entry = entry8_1,
    .exit  = exit8_1,
    .destroy = destroy8_1,
};
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
